fariszuh/IoT-Concrete-Heat-Hidration/Prototype/Gambar Panas Hidrasi.pptx

Permukaan yang dingin dan Thermal Cracking

Temperatur di tengah selama hidrasi

## Slide 2

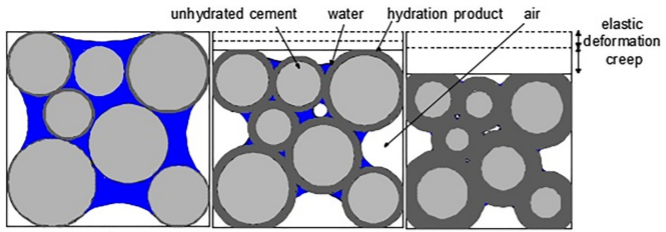
[picture p20: figure]
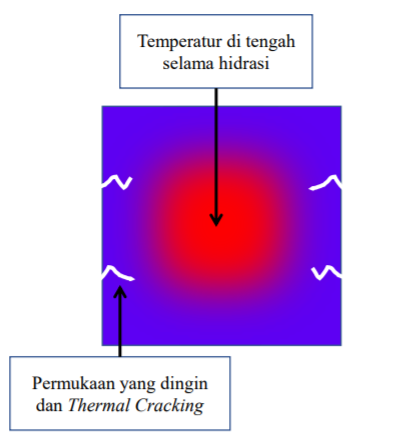
[picture p21: figure]

## Slide 3

Algoritma Pengolahan Data

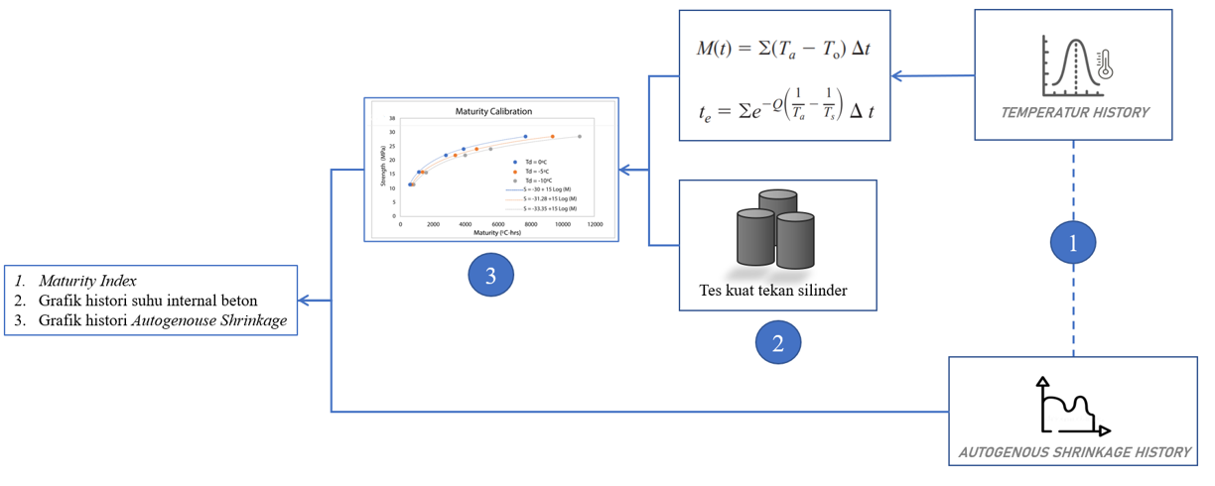
[picture p22: figure]

Cloud data base

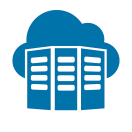
[picture p23: figure]

Penyimpanan Offline

Mikrokontroller ESP32

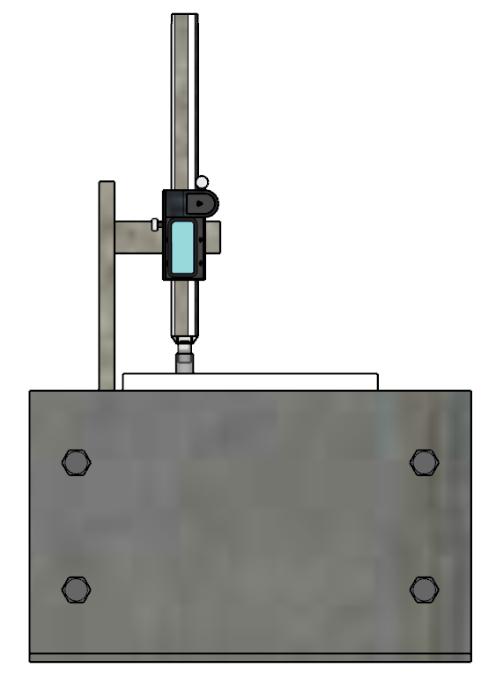
[picture p24: figure]

A

A

Tampak Depan

Unscaled

Digital Caliper

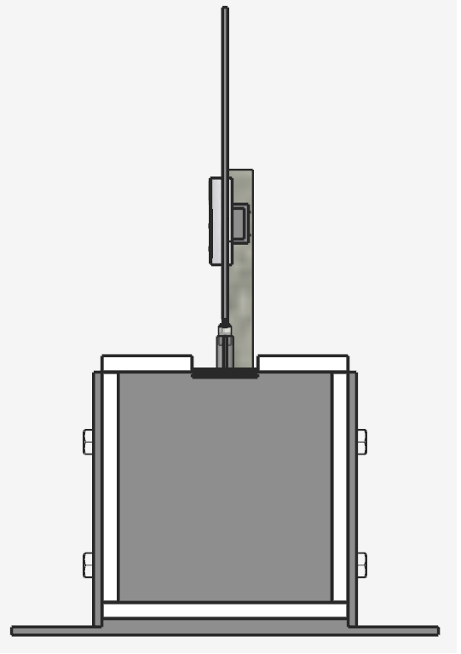
[picture p25: figure]

Potongan A-A

Unscaled

Cor Beton

Cetakan Beton

Sendor DS18B20

Insulasi

## Slide 4

Algoritma Pengolahan Data

## Slide 5

Algoritma Perhitungan

Potongan A-A

Unscaled

Cloud data base

Mikrokontroller ESP32

Penyimpanan Offline

A

A

Tampak Depan

Unscaled

Digital Caliper

Cor Beton

Cetakan Beton

Termokopel

Insulasi gabus

## Slide 6

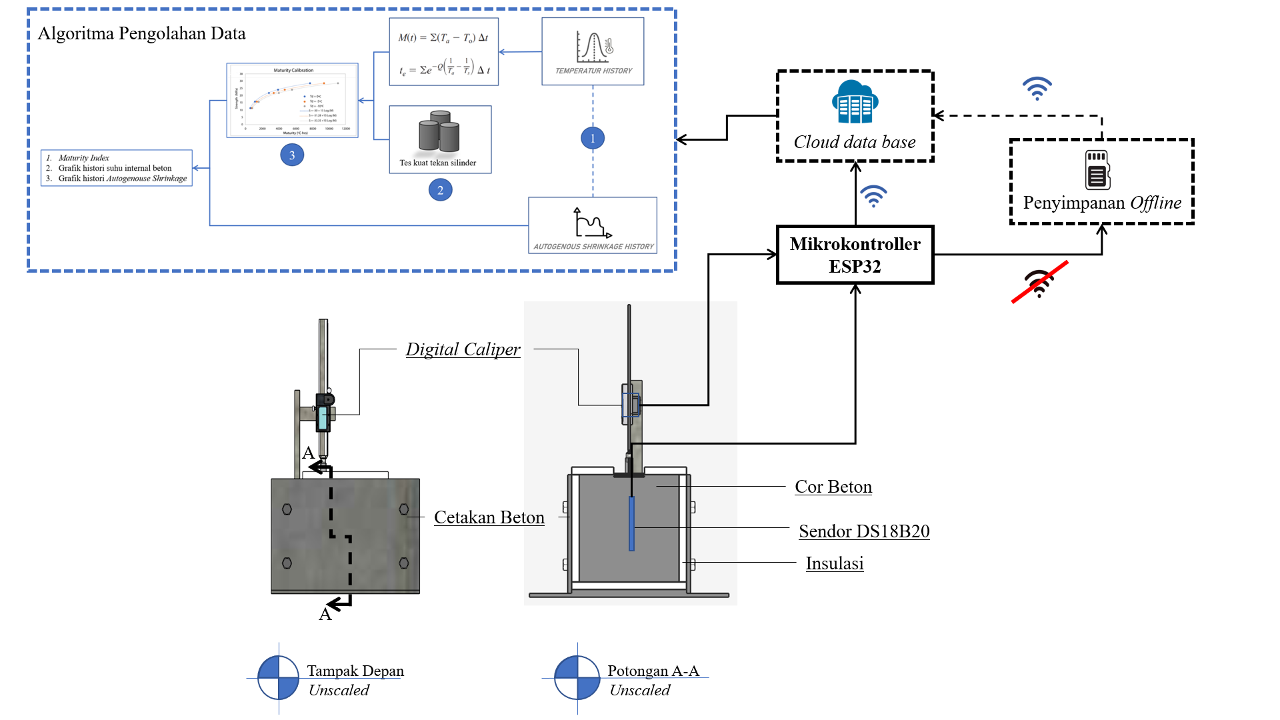
[picture p26: figure]

## Slide 7

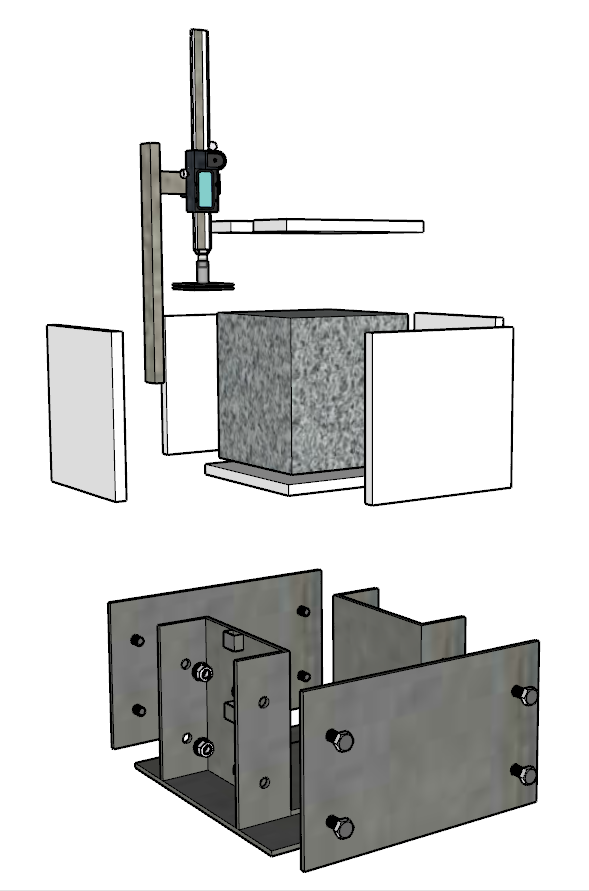
[picture p27: figure]
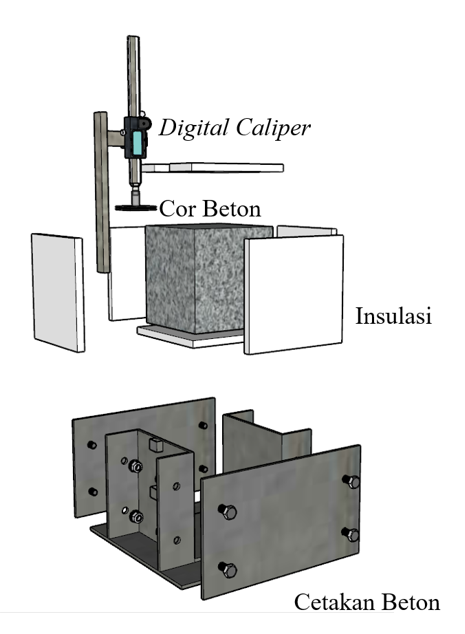
[picture p28: figure]

Digital Caliper

Cor Beton

Insulasi

Cetakan Beton

## Slide 8

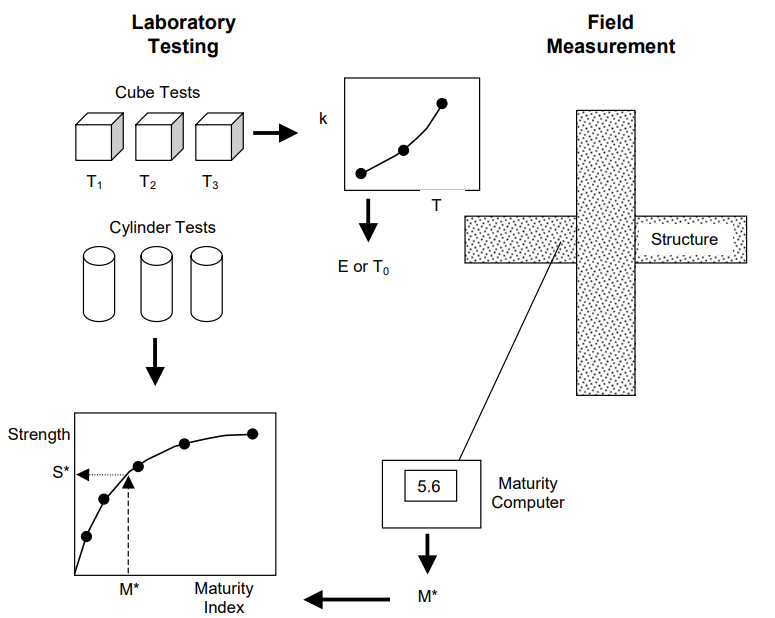
[picture p29: figure]

Pengukuran suhu Dengan alat yang sudah dibuat

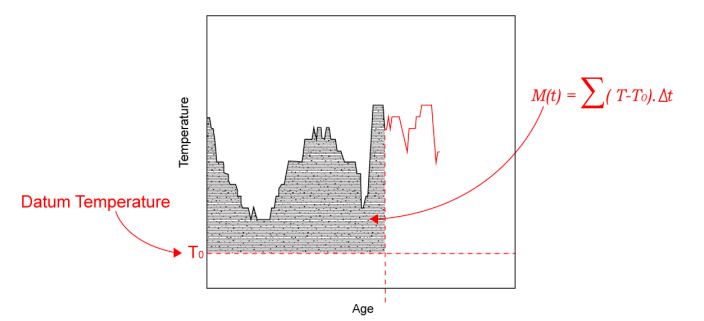
[picture p30: figure]
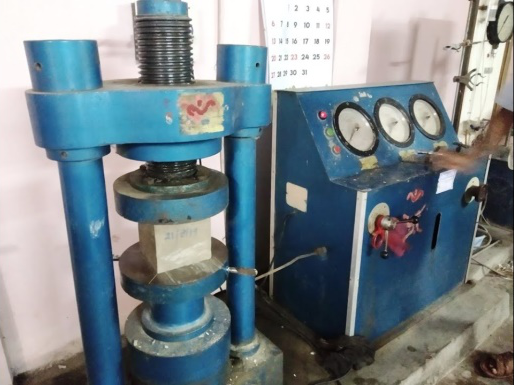
[picture p31: figure]
See the source image
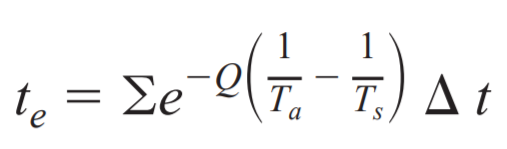
[picture p32: figure]
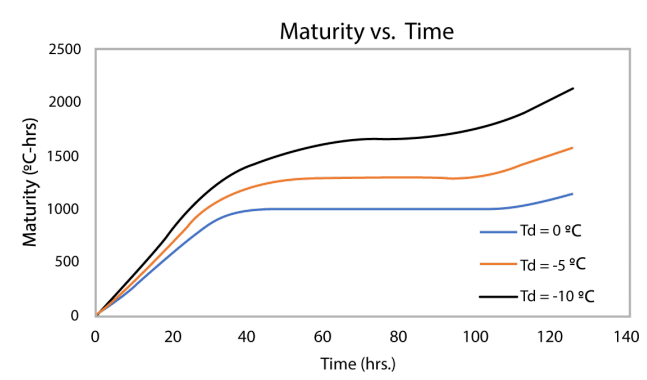
[picture p33: figure]
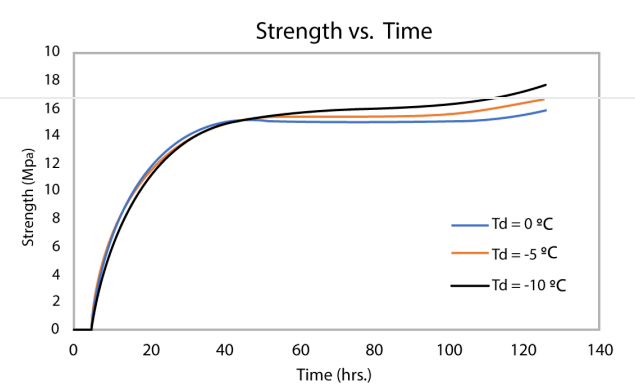
[picture p34: figure]
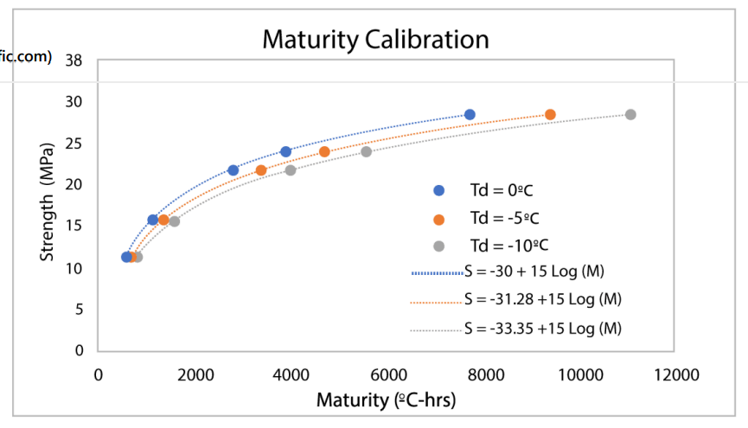
[picture p35: figure]

## Slide 9

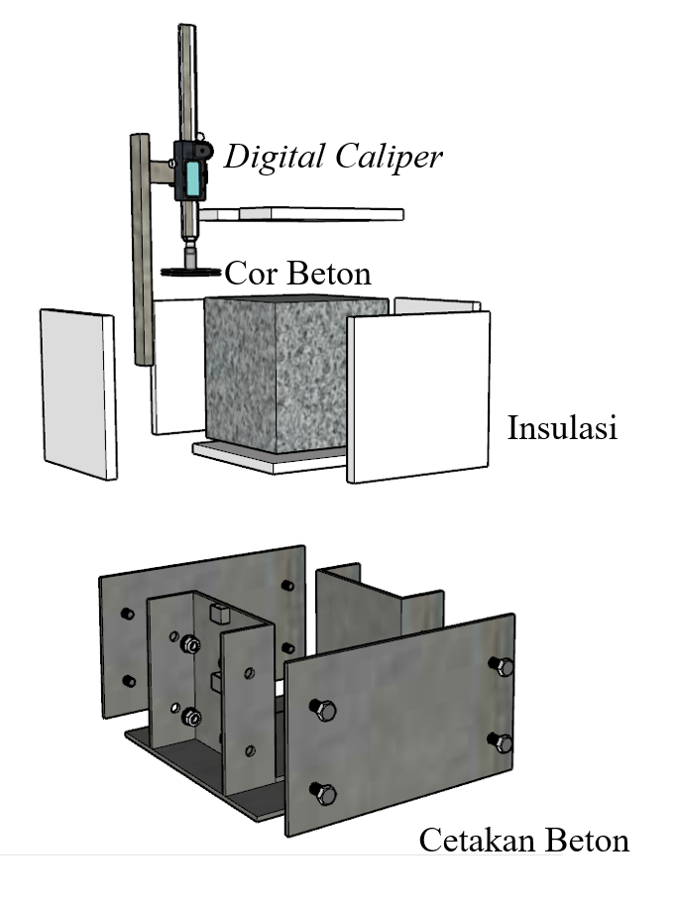
[picture p36: figure]
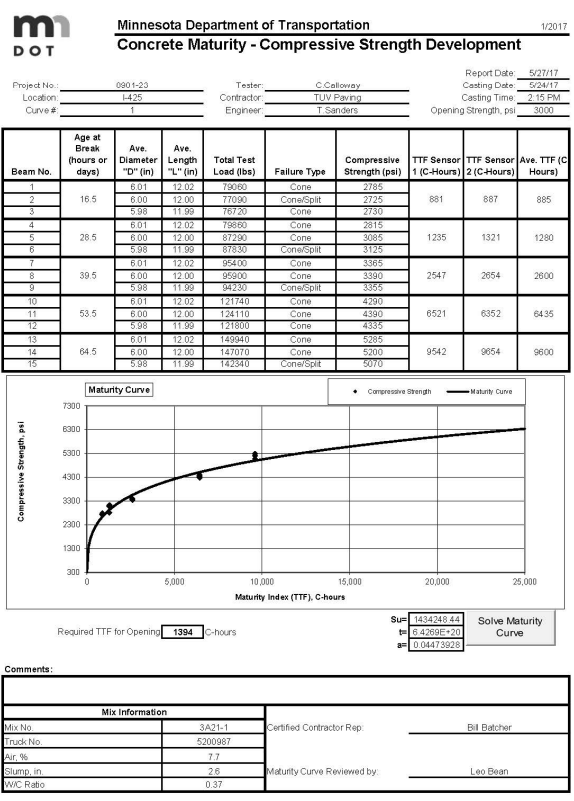
[picture p37: figure]
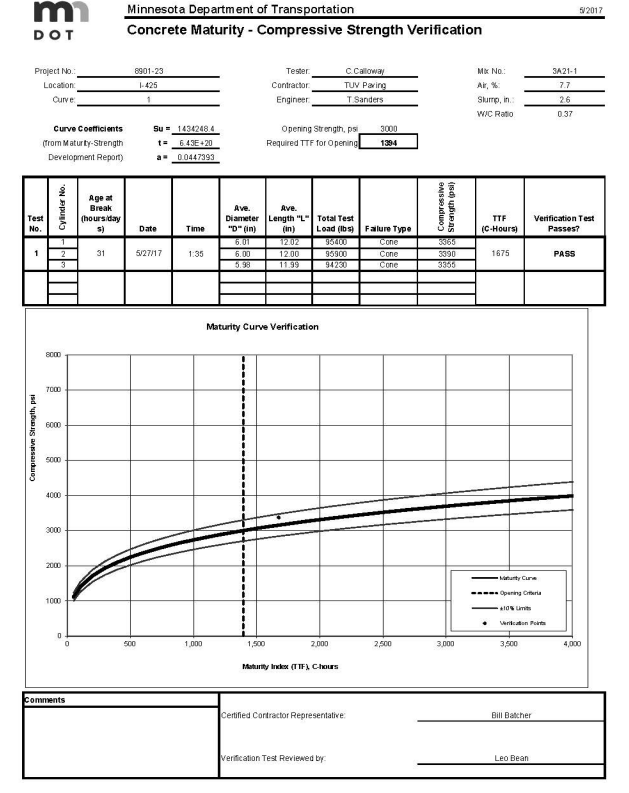
[picture p38: figure]

## Slide 10

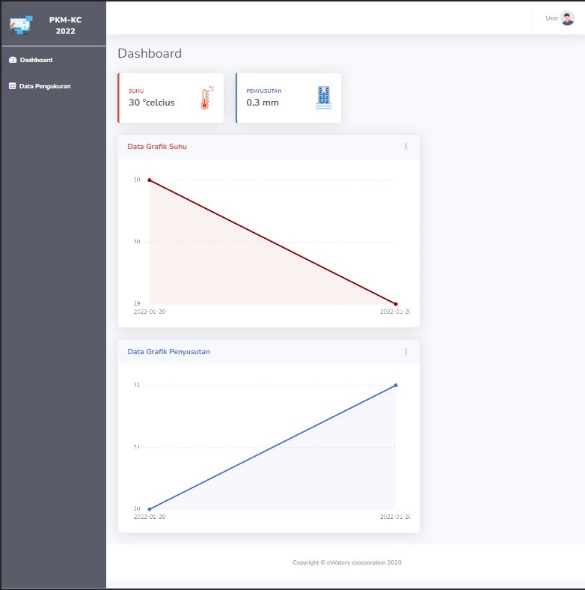
[picture p39: figure]
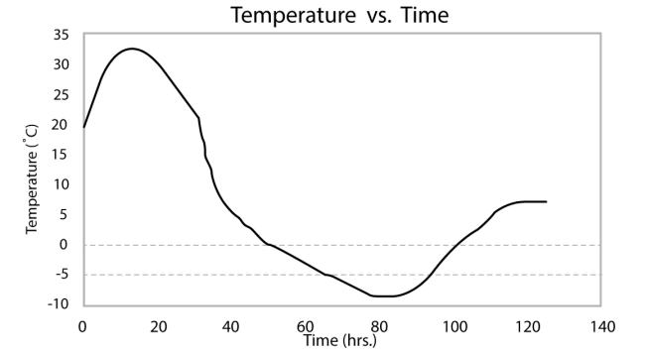
[picture p40: figure]
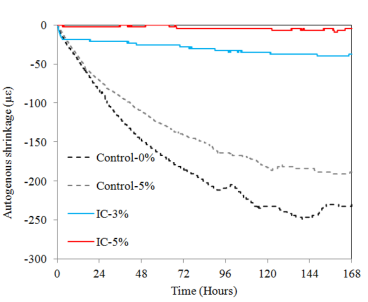
[picture p41: figure]

## Slide 11

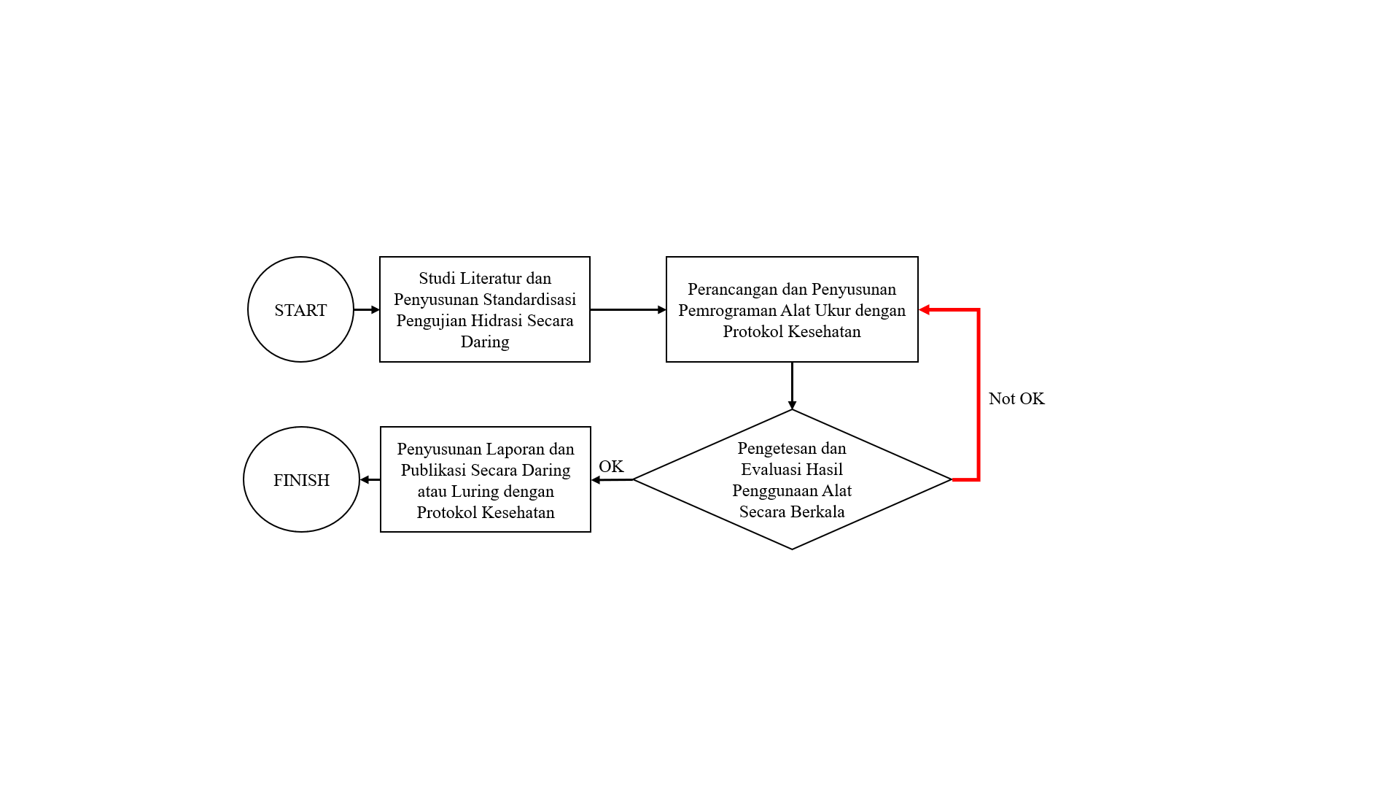
[picture p42: figure]
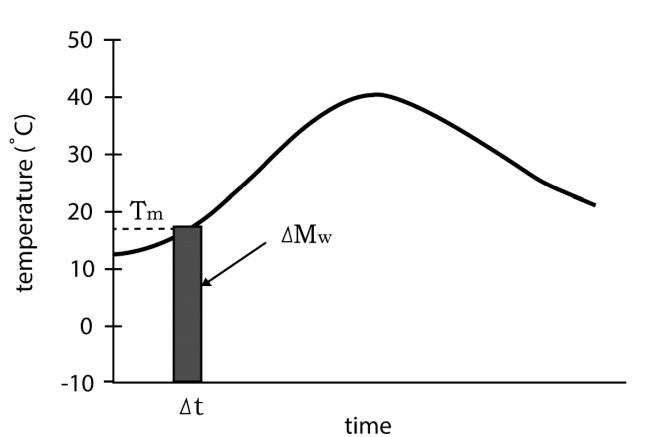
[picture p43: figure]

START

Studi Literatur dan Penyusunan Standardisasi Pengujian Hidrasi Secara Daring

Perancangan dan Penyusunan Pemrograman Alat Ukur dengan Protokol Kesehatan

Pengetesan dan Evaluasi Hasil Penggunaan Alat Secara Berkala

Not OK

FINISH

Penyusunan Laporan dan Publikasi Secara Daring atau Luring dengan Protokol Kesehatan

OK

## Slide 12

Tes Kuat Tekan Beton

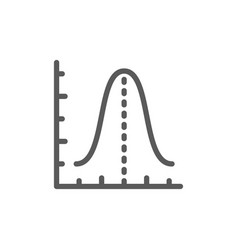
[picture p44: figure]
Curve Graph Vector Images (over 15,000)

TEMPERATUR HISTORY

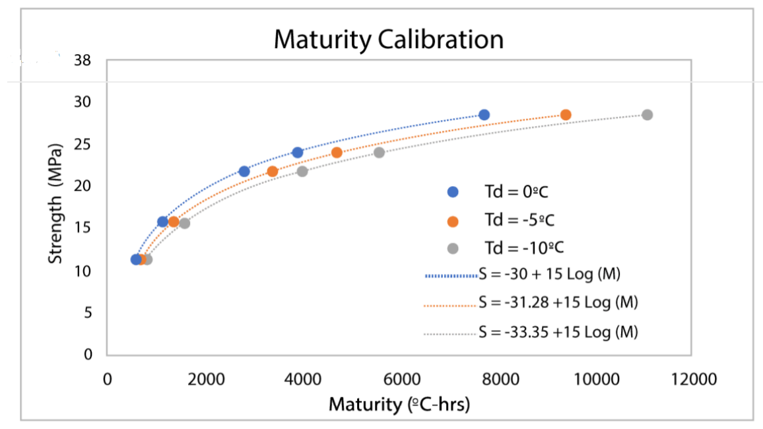
[picture p45: figure]

1. Maturity Index
2. Grafik histori suhu internal beton
3. Grafik histori Autogenouse Shrinkage

AUTOGENOUS SHRINKAGE HISTORY

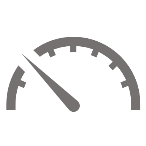
[picture p46: figure]
Speedometer Low with solid fill

## Slide 13

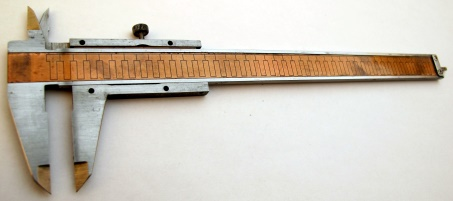
[picture p47: figure]
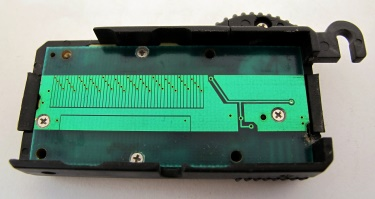
[picture p48: figure]
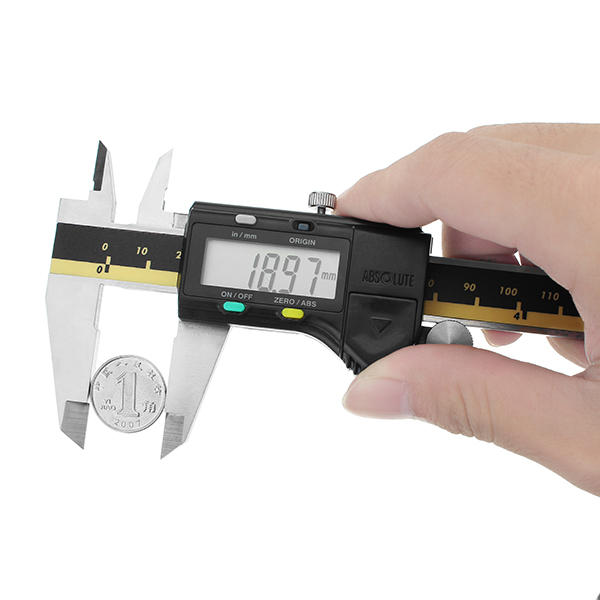
[picture p49: figure]
Hand Tools Business, Office & Industrial 6 Inch 150mm LCD Digital Electronic Vernier Caliper Micrometer Stainless Steel R suneducationgroup.com
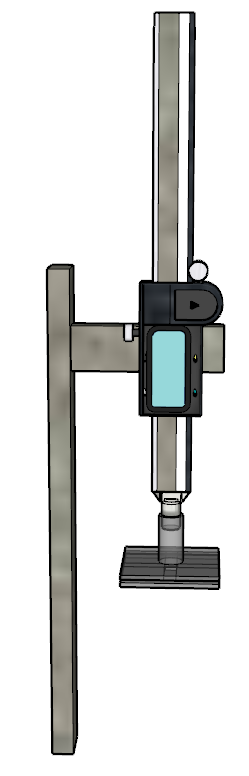
[picture p50: figure]

disambungkan

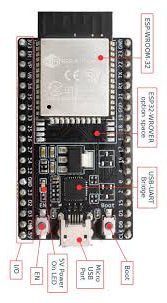
[picture p51: figure]
The Internet of Things with ESP32

1

2

3

disambungkan

Pengukuran Suhu Dengan Sensor
