fariszuh/IoT-Concrete-Heat-Hidration/Daftar Pustaka/Lapkhir.pdf

i

DAFTAR ISI

DAFTAR ISI | i
DAFTAR GAMBAR | i
DAFTAR TABEL | i
BAB 1. PENDAHULUAN | 1
1.1 | Latar Belakang | 1
1.2 | Perumusan Masalah | 2
1.3 | Tujuan | 3
BAB 2. TINJAUAN PUSTAKA | 3
2.1 Internet of Things (IoT) | 3
2.2 Modul Relay | 3
2.3 Sensor Arus ACS712 | 3
2.4 Sensor Tegangan ZMPT101B | 4
BAB 3. METODE PELAKSANAAN | 4
3.1 Studi Literatur | 4
3.2 Penyusunan Script | 4
3.3 Pembuatan Animasi | 4
3.4 Penyusunan Video | 4
3.5 Pembuatan Laporan | 4
BAB 4. HASIL YANG DICAPAI | 5
4.1 Hasil yang dicapai | 5
4.2 Potensi Khusus | 8
BAB 5 PENUTUP | 9
5.1 Kesimpulan | 9
5.2 Saran | 9
DAFTAR PUSTAKA | 10
LAMPIRAN | 11
Lampiran 1. Tabel Rincian Penggunaan Dana | 11
Lampiran 2. Nota Pembayaran | 12
Lampiran 3. Bukti Pendukung Kegiatan | 19
Lampiran 4. Lain Lain | 21
| DAFTAR GAMBAR
Gambar 1. Halaman Depan User Interface pada Aplikasi Pengguna | 9
Gambar 2. Desain Rangkaian Komponen Elcomic | 9
Gambar 3. Gambaran Peralatan Listrik Rumah Tangga | 10
Gambar 4. Gambaran Dalam Stop Kontak | 10
Gambar 5. Gambaran Depan Video Pelaksanaan Program | 11
| DAFTAR TABEL
Tabel 1.1 Tarif Dasar Listrik PLN dengan Daya 1300 VA Tahun 2015-2017.....4 Tabel 1.2 Perbandingan Elcomic dengan KWh Meter Digital dan Power Meter.5

BAB 1. PENDAHULUAN

### 1.1 Latar Belakang

Kenaikan pendapatan yang tidak sebanding dengan kebutuhan merupakan salah satu masalah ekonomi yang dirasakan oleh sebagian masyarakat Indonesia. Selain itu kenaikan biaya bahan bakar, pendidikan dan sembako juga menambah beban pengeluaran masyarakat. Adanya kebijakan menaikkan tarif dasar listrik menyebabkan pengeluaran masyarakat terus bertambah.
Salah satu belanja pokok masyarakat tiap bulan adalah biaya listrik yang dapat dihitung dengan cara besaran daya yang dipakai dikalikan tarif listrik lalu dikalikan waktu pemakaian. Pemakaian listrik semakin sulit untuk dikontrol dan dibatasi agar sesuai dengan anggaran keuangan rumah tangga yang tersedia seiring perkembangan teknologi. Akibat dari pemakaian yang tidak dibatasi, seringkali biaya listrik membengkak sehingga masyarakat harus sadar akan pemakaian listrik agar tidak berlebih. Dengan anggaran listrik rumah tangga yang terkontrol, sisa anggaran dapat dialokasikan untuk jenis pengeluaran yang lain dan juga tidak mengganggu anggaran belanja rumah tangga yang telah direncanakan.

Tabel 1.1 Tarif Dasar Listrik PLN dengan Daya 1300 VA Tahun 2015-2017
Tarif Dasar Listrik | Tahun
2014 | 2015 | 2016 | 2107
1300 VA | Rp 1.214/kWh | Rp 1.352/kWh | Rp 1.364,86/kWh | Rp 1.467,28/kWh

Saat ini kebanyakan rumah tangga di Indonesia menggunakan kWh meter digital yang dipakai untuk listrik prabayar. Alat tersebut hanya menampilkan daya listrik tersisa yang akan digunakan. Selain itu ada alat yang bernama Power Meter, yaitu alat yang mampu memonitor dan mengetahui besar daya listrik yang digunakan di dalam rumah. Kedua alat tersebut dapat memantau pemakaian daya listrik, namun tidak mampu melakukan pengawasan terhadap penggunaannya dari sisi biaya. Dari alat berbasis aplikasi ada juga yang dapat mengontrol penggunaan listrik perangkat elektronik yang terhubung dengan jaringan nirkabel namun tidak berbasis biaya listrik. Sehingga, solusi tersebut belum mampu mengatasi permasalahan anggaran pengeluaran kebutuhan listrik rumah tangga masyarakat Indonesia.
Oleh karena itu, dibutuhkan solusi berupa alat yang dapat memanage penggunaan listrik berdasarkan anggaran belanja rumah tangga yang dapat memonitor dan membantu konsumen untuk membatasi penggunaan listrik dengan menggunakan sistem wireless melalui smartphone dan aplikasi berbasis IoT (Internet of Things). Alat yang terdiri dari software dan hardware terintegrasi ini dilengkapi dengan algoritma yang menghitung penggunaan daya listrik berbasis tarif Rupiah untuk kemudian disampaikan kepada pengguna dalam bentuk alarm atau notifikasi penggunaan sebagai pengingat apabila penggunaan listrik hampir mendekati batas. Pada alat ini juga terdapat relay system yang terhubung dengan perangkat elektronik agar dapat mematikan peralatan listrik yang tidak terlalu dibutuhkan apabila pengunaan listrik di suatu rumah melebihi tarif yang ditentukan oleh budget planner secara otomatis dan real time. Alat ini dapat melakukan setting untuk berapa besar daya yang mau dikeluarkan bergantung biaya penggunaan listrik yang ingin dimasukkan dalam aplikasi. Selain itu, pada alat ini dilengkapi memory yang dapat menyimpan data penggunaan listrik bulan sebelumnya yang bisa digunakan untuk evaluasi pemakaian listrik. Dengan alat ini, tentunya mampu menjawab permasalahan masyarakat rumah tangga dalam menghemat listrik sehingga anggaran rumah tangga dapat dialokasikan ke kebutuhan yang lain.

Tabel 1.2 Perbandingan Elcomic dengan KWh Meter Digital dan Power Meter
| KWh Meter Digital (Schneider - IEM 3255) | Power Meter ( Siemens -SICAM P50/55) | ELCOMIC
Mengukur Daya Listrik | ✓ | ✓ | ✓
Mengukur Daya Listrik per Peralatan | - | ✓ | ✓
Mengukur Biaya Listrik yang Telah Digunakan | - | - | ✓
Pengingat Penggunaan Biaya Listrik | - | - | ✓
Rencana Anggaran Penggunaan Biaya Listrik | - | - | ✓
Pemutus Arus Listrik | ✓ | - | ✓

### 1.2 Perumusan Masalah

Permasalahan yang akan diselesaikan dari Program Kreativitas Mahasasiswa ini adalah bagaimana cara merancang desain, komponen penyusun alat, serta simulasi kerja alat ELCOMIC yang divisualisasikan dalam sebuah video animasi.

### 1.3 Tujuan

Tujuan yang akan dicapai dengan Program Kreativitas Mahasiswa ini berupa rancangan desain, komponen penyusun alat, serta simulasi kerja alat ELCOMIC yang divisualisasikan dalam sebuah video animasi.

### 1.4 Manfaat

Manfaat dari Program Kreativitas Mandiri ini sebagai berikut:
1. Bagi Rumah Tangga
Membantu merencanakan dan mengontrol penggunaan listrik sesuai dengan anggaran belanja sehingga dapat menghemat pengeluaran.
2. Bagi Mahasiswa
Mengembangkan kreativitas dalam bidang teknologi yang lebih efektif dan efisien sesuai dengan permasalahan yang ada dalam masyarakat.

BAB 2. TINJAUAN PUSTAKA

### 2.1 Internet of Things (IoT)

Terdapat lebih dari delapan juta perangkat berbasis Internet of Things (IoT) pada tahun 2019 (K.L.Lueth,2018).Internet of Things merupakan perpaduan perangkat keras yang diintegrasikan ke dalam jaringan informasi sebagai penghubung atau sarana komunikasi antar pengguna. Perangkat berbasis IoT dapat menghimpun dan membagikan data dari berbagai pengguna (J.Mills dkk.,2020). Dalam hal ini, data yang diperoleh dari sensor tegangan dan sensor arus akan dikirimkan kepada pengguna melalui sarana Internet of Things. Beberapa perangkat IoT seperti kamera keamanan, pelacak aktivitas kebugaran dan kesehatan, dan smartphones menghimpun data yang bersifat privasi sehingga pengguna tidak ingin membagikan data tersebut dengan pengguna lain. Sama halnya dengan alat yang ini dimana data dari sensor tegangan dan sensor arus hanya dibagikan kepada satu pengguna yang bersesuaian dengan sensor tersebut.

### 2.2 Modul Relay

Relay adalah alat yang digunakan sebagai pembuka/penutup suatu circuit elektrikal dengan suatu kondisi yang memicu. Relay merupakan elektromagnet yang sirkuit magnetnya terdiri atas coil, armature, switch contact point, dan spring yang bekerja berdasarkan medan elektromagnetik (Apples dkk.,1966). Relay menggunakan prinsip elektromagnetik untuk menggerakkan kontak saklar sehingga dengan arus listrik yang kecil dapat menghantarkan listrik yang bertegangan tinggi.. Dalam hal ini Modul Relay menjaga keamanan suatu rangkaian system elektrik dimana akan mendeteksi suatu keadaan abnormal dalam system lalu akan dilakukan tindakan sirkuit kontrol yang tepat (Kezunovic dkk., 2016).

### 2.3 Sensor Arus ACS712

Sensor Arus ACS712 merupakan sensor yang digunakan untuk mendeteksi arus listrik dengan keahlian memantau penggunaan arus listrik dan dapat memberikan nilai analog sehingga penggunaan tenaga listrik dapat dikontrol (Dalimunthe, 2018). Sensor ACS712 dapat mendeteksi arus baik AC maupun DC dimana sensor ini bekerja dengan prinsip efek Hall. Sensor ACS712 juga memiliki tingkat akurasi yang tinggi, linearitas yang baik, disuplai oleh 5V DC; tegangan output adalah 4.5V, dan perlu sedikit rangkaian untuk pengolahan data (Li dkk.,2010). Pada alat ini ACS712 berfungsi sebagai pendeteksi aliran arus listrik yang mengalir.

### 2.4 Sensor Tegangan ZMPT101B

Modul sensor tegangan ZMPT101B adalah sensor tegangan yang dibuat dari transformator tegangan ZMPT101B. Sensor ini memiliki akurasi tinggi, konsistensi yang baik untuk pengukuran tegangan dan dapat mengukur hingga 250V AC serta dilengkapi dengan potensiometer untuk menyesuaikan output ADC ke nilai yang sesuai dengan input referensi(Abubakar dkk., 2017). Pada alat ini ZMPT101B berfungsi sebagai pengukur tegangan pada peralatan listrik.

BAB 3. METODE PELAKSANAAN

### 3.1 Studi Literatur

Pada studi literatur dilakukan proses pencarian materi yang berkaitan dengan Internet of Things, Sensor Tegangan ZMPT101B, Sensor Arus ACS712, Modul Relay, STM32, Micro SD card, dan User Interface. Selain itu, juga dilakukan studi literatur mengenai permasalahan listrik rumah tangga. Literatur yang digunakan antara lain dari berita harian, artikel, jurnal, seminar internasional, dan publikasi ilmiah.

### 3.2 Penyusunan Script

Script dibuat agar video terarah serta terkonsep dengan baik. Script yang dibuat antara lain penjelasan latar belakang, animasi dialog, animasi desain interior, dan penjelasan mengenai User Interface aplikasi. Script ini sendiri dibuat di software Notepad.

### 3.3 Pembuatan Animasi

Animasi yang dibuat agar menjadikan video program lebih menarik serta dapat lebih dipahami dengan mudah. Animasi yang dibuat yaitu animasi dialog Elco dan Mico. mengenai alat ini serta animasi interior rumah dengan peralatan yang diintegrasikan dengan alat dan aplikasi Elcomic. Animasi Elco dan Mico dibuat menggunakan software Adobe After Effect, sedangkan animasi interior rumah dibuat menggunakan software SketchUp.

### 3.4 Penyusunan Video

Pada proses penyusunan video, seluruh scene dan animasi disusun dan diedit dengan menambahkan musik dan tulisan penjelasan didalamnya. Video diedit dan disusun menggunakan software Adobe Premiere Pro.

### 3.5 Pembuatan Laporan

Proses penulisan laporan dilakukan setelah semua tahap terselesaikan sehingga hasil yang diperoleh dapat dijelaskan secara rinci sesuai dengan data yang diperoleh. Kemudian semua kegiatan yang telah dilakukan akan didokumentasikan dalam foto dan pembuatan video simulasi sebagai luaran yang akan menggantikan prototipe karena faktor masa pandemi yang tidak memungkinkan kegiatan di luar rumah.

BAB 4. HASIL YANG DICAPAI

### 4.1 Hasil yang dicapai

Adapun hasil yang dicapai pada program kreatifitas mahasiswa ini adalah sebagai berikut :
1. Studi Literatur
Hasil : Mendapatkan berbagai sumber pendukung dari jurnal – jurnal yang terindeks scopus (jurnal ieee, springer, science direct), yaitu tentang STM32, sensor arus ACS712, sensor tegangan ZMPT101B dan relay.
2. Pembuatan User Interface
Hasil : Mendapatkan desain User Interface aplikasi Elcomic yang nantinya diterapkan di smartphone calon pengguna. Desain aplikasi dibuat menggunakan Adobe Ilustrator.Aplikasi ini terdiri dari beberapa fitur, diantaranya :
- Halaman depan (sign in & sign up) ;
- Halaman utama (home)-->memantau besar pemakaian ;
- History-->sejarah pemakaian ;
- Setting-->pengaturan & penambahan peralatan ;
- Beranda (terdapat fitur account user, about us, notification, infromation, dan help) :
*[account user]-->user mana yang terkoneksi dengan alat ; *[notification]-->pemberitahuan mengenai opsi pemutusan peralatan ;

*[information]-->informasi mengenai peraturan pemakaian & tarif.

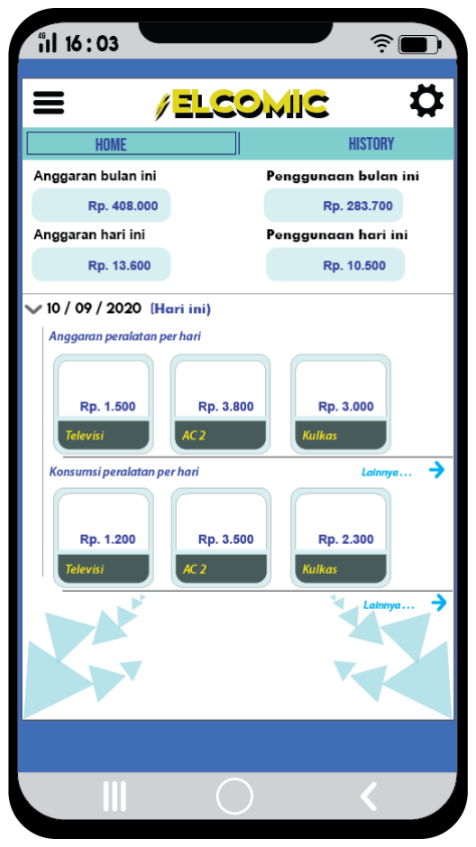
[picture p228: figure]

Gambar 1. Halaman Depan User Interface pada Aplikasi Pengguna
3. Assembly komponen
Hasil : Mendapatkan desain rangkaian komponen yang dibuat dalam bentuk 2D.

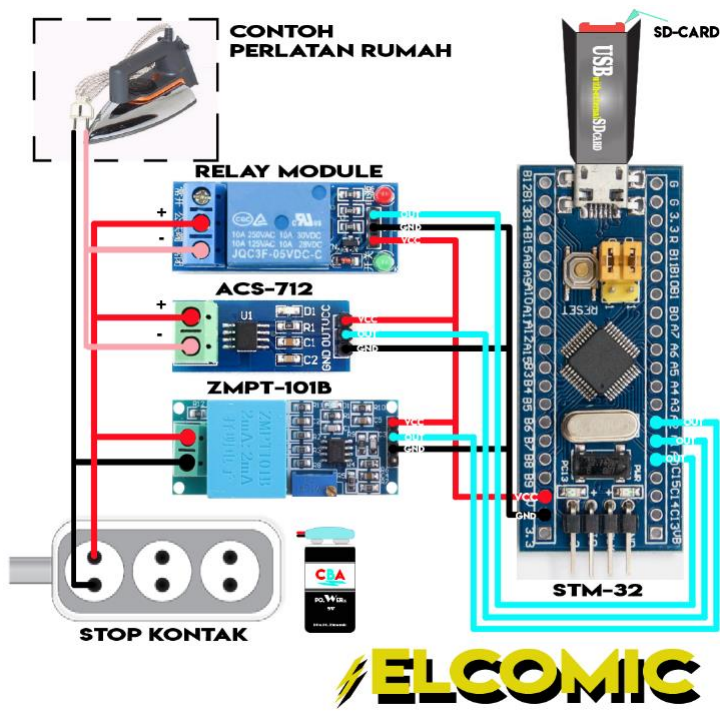
[picture p229: figure]

Gambar 2. Desain Rangkaian Komponen Elcomic

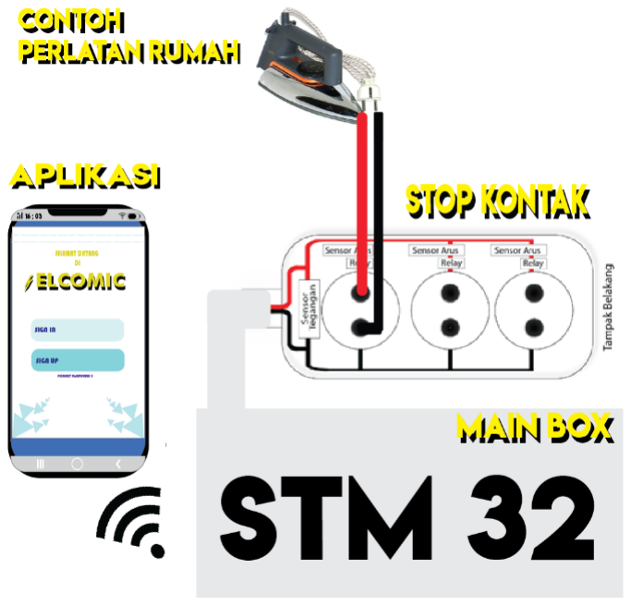
[picture p230: figure]

Gambar 3. Gambaran Peralatan Listrik Rumah Tangga

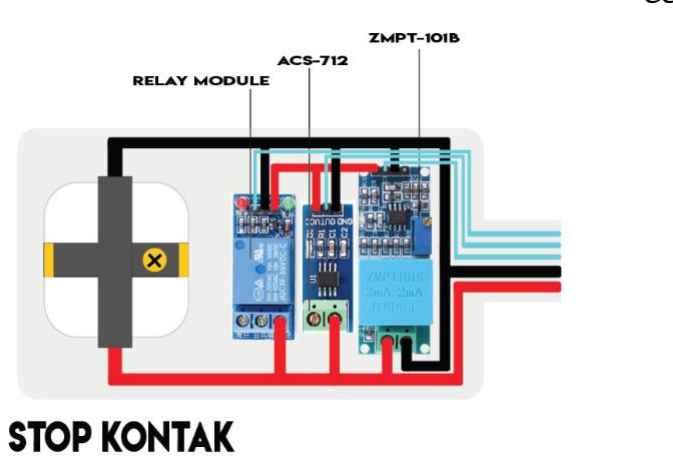
[picture p231: figure]

Gambar 4. Gambaran Dalam Stop Kontak
4. Analisis manfaat dan kontribusi alat terhadap masyarakat
Hasil : Mendapatkan analisis manfaat produk terhadap teknologi terkini, ekonomi dan sosial untuk saat ini dan masa depan serta kontribusi terhadap kebutuhan masyarakat.
5. Video Pelaksanaan Program
Hasil: Mendapatkan video penjelasan latar belakang, penjelasan rumusan masalah, pembuatan desain User Interface, dan pembuatan desain rangkaian komponen dari PKM ini.

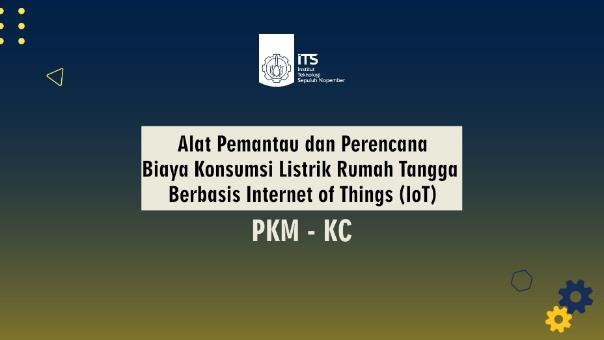
[picture p232: figure]

Gambar 5. Gambaran Depan Video Pelaksanaan Program

### 4.2 Potensi Khusus

Potensi khusus dari program kreatifitas mahasiswa ini adalah sebagai berikut :

### 1. Potensi Paten

Inovasi yang ada pada Elcomic terdapat pada fitur dimana user dapat memantau besar penggunaan masing peralatan elektronik secara real time serta fitur dimana user dapat melakukan tindakan pemutusan arus pada suatu peralatan elektronik apabila pengunaan listrik melebihi tarif yang ditentukan oleh budget planner secara otomatis dan real time yang bersifat opsional (terdapat notifikasi konfirmasi peralatan tertentu sudah dekat dengan batas pakai berupa “ya” atau “tidak”,untuk melakukan pemutusan). Terdapat juga perbadingan produk dengan produk paten No. 2016-13940 (Japan Patent) dimana keunggulan produk Elcomic, yaitu dapat melakukan monitoring biaya per peralatan, merencanakan biaya per peralatan, serta display monitoring menggunakan smartphone yang membuat lebih fleksibel. Hal berikut menjadikan produk kami berbeda dengan Kwh meter yang hanya menampilkan daya listrik tersisa yang akan digunakan dan Power Meter yang hanya memonitor dan mengetahui besar daya listrik yang digunakan di dalam rumah. Pernyataan ini mendukung produk Elcomic sangat potensial untuk dipatenkan.

### 2. Manfaat Bagi Teknologi Terkini, Ekonomi, dan Sosial untuk Saat

Ini dan Masa Depan
Dalam bidang teknologi di Indonesia belum ada alat atau prototipe yang dapat memantau laju penggunaan listrik rumah tangga setiap waktunya. Masyarakat hanya mengetahui biaya pemakaian listrik perbulannya untuk pascabayar dan mengetahui pulsa listrik akan habis terpakai untuk prabayar. Melalui produk ini, masyarakat dapat memantau serta mengontrol laju penggunaan listrik rumah tangga melalui aplikasi di smartphone. Hal tersebut menunjukkan manfaat dari produk untuk teknologi terkini. Subsidi listrik di APBN 2020 dianggarkan sebesar Rp. 54,79 triliun, diperkirakan akan membengkak menjadi Rp. 62,93 triliun akibat pengalokasian tambahan dalam bentuk keringanan tagihan listrik bagi masyarakat terdampak covid-19(Yolandha, 2020). Melalui produk ini, masyarakat setidaknya membantu mengurangi anggaran subsidi listrik dengan cara mengontrol penggunaan listrik rumah tangga. Pengurangan anggaran subsidi listrik dapat dialokasikan untuk pembangunan ekonomi lainnya seperti pembangunan infrastruktur, jalan tol, dan lain sebagainya. Hal tersebut menunjukkan manfaat produk dalam bidang ekonomi saat ini dan yang akan datang.
Pada awal semester tahun 2019, 61% dari 58.519 MW yang diproduksi oleh pembangkit listrik di Indonesia berasal dari batu bara (Banjarnahor, 2019). Penggunaan batu bara secara masif untuk bahan bakar pembangkit listrik dapat berdampak buruk bagi lingkungan yakni pemanasan global. Melalui cara mengontrol penggunaan listrik rumah tangga dari produk ini, masyarakat dapat mengurangi pemanasan global yang disebabkan dari bahan bakar fosil tersebut. Selain itu, mengontrol penggunaan listrik dapat dijadikan upaya untuk menghemat energi secara konkret. Hal tersebut menunjukkan manfaat dari produk dalam bidang sosial saat ini dan yang akan datang.

### 3. Kontribusi Produk Terhadap Kebutuhan Masyarakat

Adapun kontribusi produk terhadap kebutuhan masyarakat, yaitu membantu memanage perekonomian rumah tangga khususnya dalam pemakaian listrik karena adanya produk, pemakaian listrik rumah tangga dapat diatur sesuai kondisi kebutuhan dan keuangan dimana pengguna dapat memantau besar pengeluaran listrik tiap peralatan yang digunakan. Produk diharapkan menjadikan pemakaian peralatan listrik yang lebih displin dan efisiensi dengan terdapatnya relay pada produk guna membatasi pemakaian peralatan listrik dengan melakukan pemutusan terhadap sebuah peralatan yang bersifat opsional.

BAB 5 PENUTUP

### 5.1 Kesimpulan

Kesimpulan yang dapat diambil dari produk ELCOMIC, yaitu merupakan alat pemantau dan perencana biaya konsumsi listrik rumah tangga berbasis Internet of Things (IoT) yang tidak hanya dapat melakukan pengukuran daya listrik, listrik perperalatan, dan pemutusan arus listrik seperti pada KWh meter dan Power meter, tetapi juga dapat melakukan pengukuran biaya listrik yang telah digunakan, mengingatkan penggunaan biaya listrik yang akan dinotifikasikan melalui apklikasi produk, perencanaan anggaran penggunaan biaya listrik, serta dapat melakukan tindak pemutusan opsional tehadap suatu stop kontak peralatan jika pemakaian peralatan telah melewati batas penggunaan. Melalui ini, pengguna dapat terbantu dalam permasalahan perekonomian mereka khususnya dalam hal penggunaan listrik dimana menjadikan pengguna dapat memanage berapa besar biaya penggunaan listrik yang ingin mereka gunakan / keluarkan sehingga dapat menghemat pengeluaran.

### 5.2 Saran

Saran yang didapat adalah sebagai berikut :
1. Untuk desain main box yang berisi Mikrokontroler STM32, Micro SD Card, Regulator, dan modul WI-FI dapat dimaksimalkan dalam unsur seninya.
2. Aplikasi Elcomic dapat ditambahkan fitur spesifikasi peralatan yang didapatkan dari library atau internet setelah user memasukkan merk dan serinya.

DAFTAR PUSTAKA
Abubakar, dkk. 2017. Calibration of ZMPT101B Voltage Sensor ModSule using Polynomial Regression for Accurate Load Monitoring. APRN Journal of Engineering and Applied Sciences. Volume 12, No. 4.
Appels J. Th dan Geels B. H. 1966. Handbook of Relay Switching Technique. Springer-Verlag Berlin Heidelberg.
Banjarnahor, Donald. 2019. Dari 58 Ribu MW, 61% Pembangkit Listrik RI Masih Batu Bara. www.cnbcindonesia.com/news/20190923114710-4-101382/dari-58-ribu-mw-61-pembangkit-listrik-ri-masih-batu-bara (diakses tanggal 20 Agustus 2020)
Dalimunthe, R. A. 2018 .Pemantau Arus Listrik Berbasis Alarm Dengan Sensor Arus. Seminar Nasional Royal., pp. 333–338
Kezunovic, Mladen, dkk. 2016. Design, Modeling dan Evaluation of Protective Relays for Power Systems. Springer International Publishing Switzerland Li, L. dkk,. 2010. The Application of Hall Sensors ACS712 in The Protection Circuit of Controller for Humanoid Robots. International Conference on Computer Sciences and Appliead Mathematics. vol. 12.
Lueth, K.L. 2018. State of the IoT 2018: Number of IoT Devices Now at 7B—Market Accelerating. Available: iot-analytics.com/state-of-the-iot-update-q1-q2-2018-number-of-iot-devices-now-7b
Mills, J. dkk. 2020. Communication-Efficient Federated Learning for Wireless Edge Intelligence in IoT. IEEE Internet of Things Journal. Vol. 7, No. 7, pp. 5986-5994.
Yolandha, Friska. 2020. Subsidi Listrik Diproyeksi Jebol Sampai Rp 62,93 Triliun. www.republika.co.id/berita/qeewjv370/subsidi-listrik-diproyeksi-jebol-sampai-rp-6293-triliun (diakses tanggal 20 Agustus 2020)

LAMPIRAN

Lampiran 1. Tabel Rincian Penggunaan Dana

### 1. Pemasukan

No. | Keterangan | Total (Rp)
1. | Pendanaan PKM 2020 | Rp 5.000.000
TOTAL PEMASUKAN (Rp) | | Rp 5.000.000

### 2. Pengeluaran

No | Keterangan | Total (Rp)
1. | Kuota Internet | Rp 593.050
2. | Produk | Rp3.574.100
3. | Media penyimpanan soft file | Rp 825.000
TOTAL PENGELUARAN (Rp) | | Rp.4.992.150

### 3. Saldo

No | Keterangan | Total (Rp)
1. | Total Pemasukan | Rp 5.000.000
2. | Total Pengeluaran | Rp.4.992.150
SALDO = PEMASUKAN - PENGELUARAN | | Rp 7.850
(Tujuh Ribu Delapan Ratus Lima Puluh Rupiah)

Lampiran 2. Nota Pembayaran No. | Tanggal
Keterangan | Nota Pembayaran | Jumlah

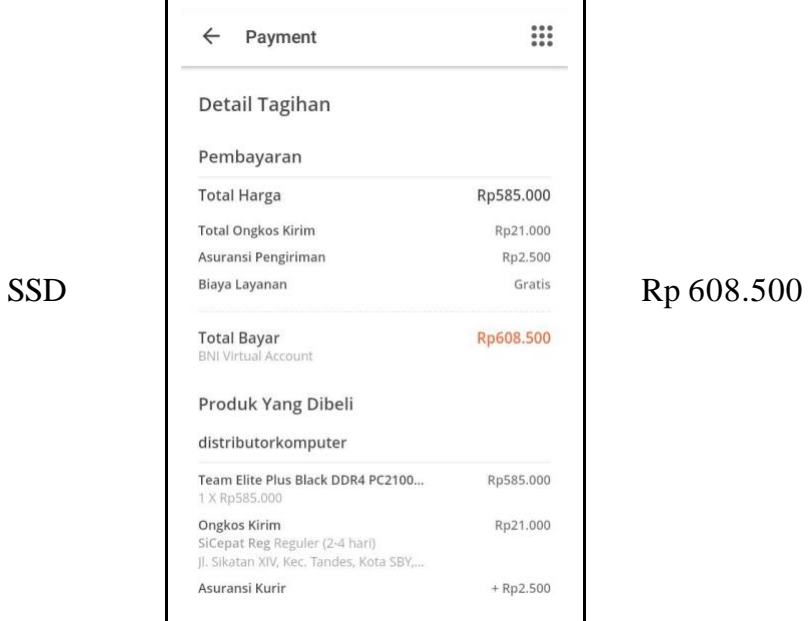
[picture p233: figure]
SSD

1. 28/0
8

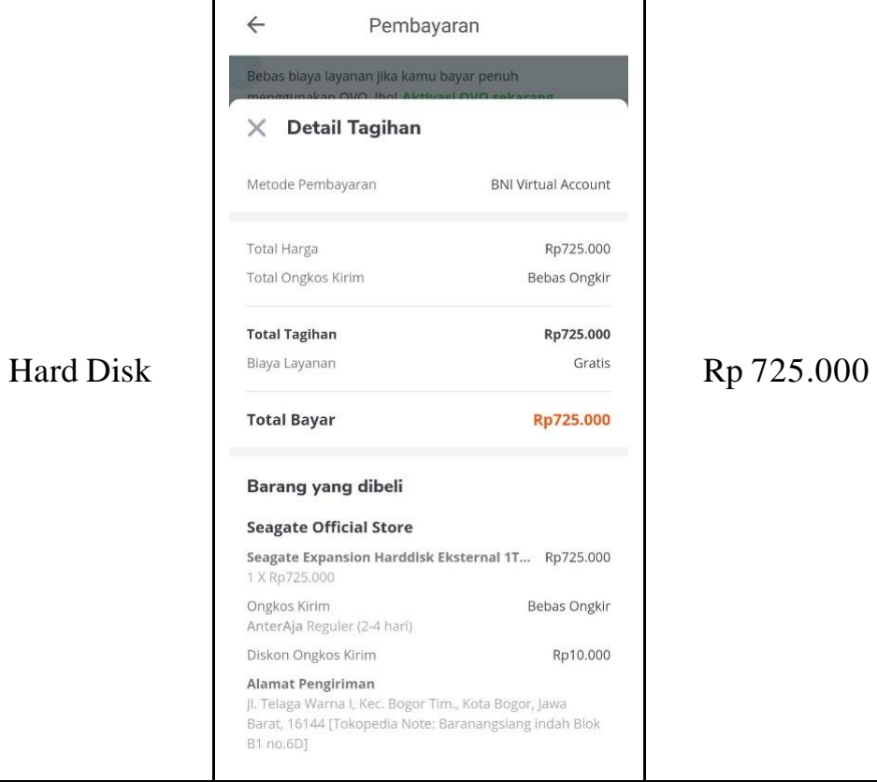
[picture p234: figure]
Hard Disk

2. 20/0
9

3. 28/0
9

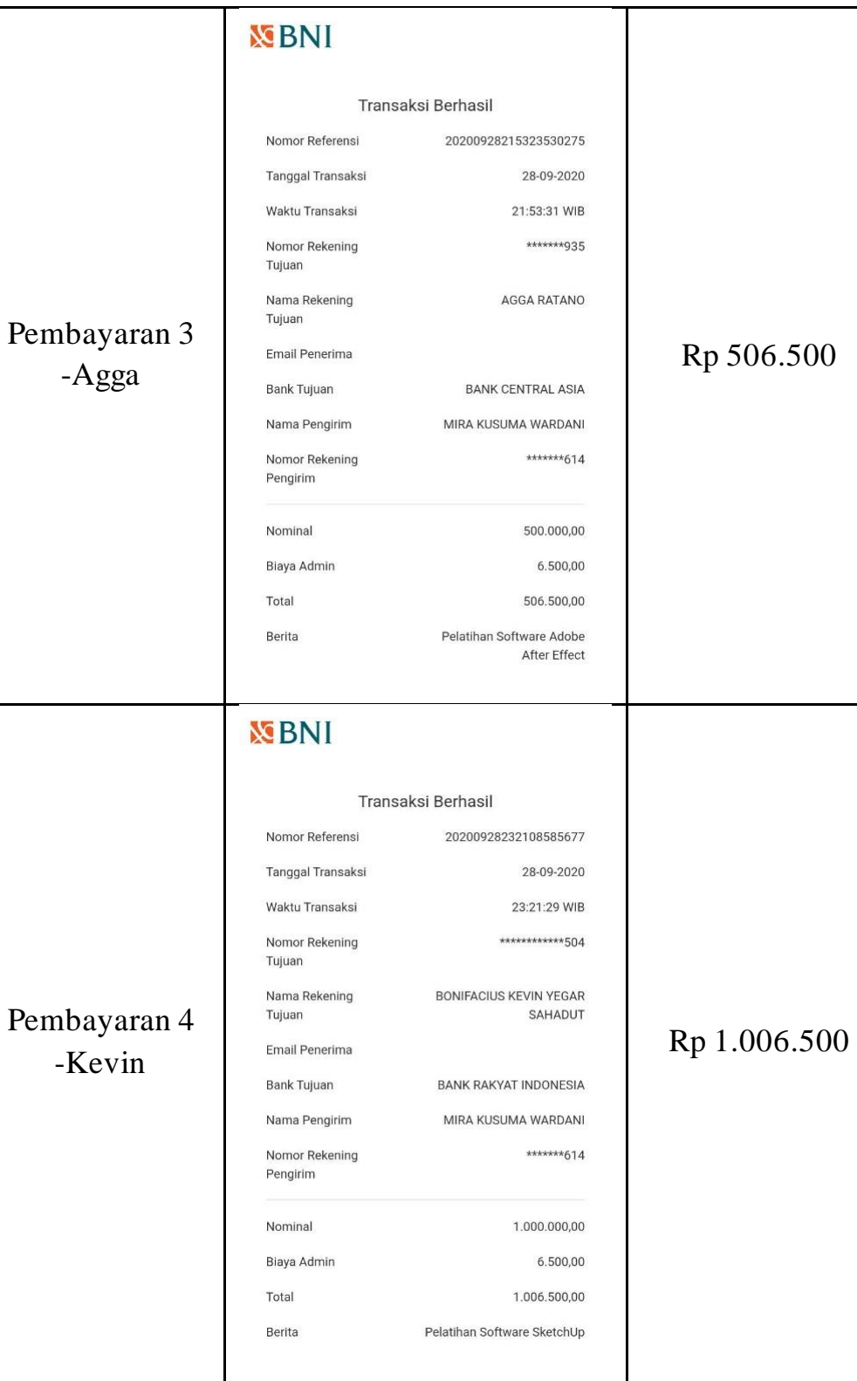
[picture p235: figure]
-Agga; Pembayaran 4; -Kevin

Pembayaran 3

4. 28/0
9

5.

24/0
9
Pulsa Arnold | Rp 198.550

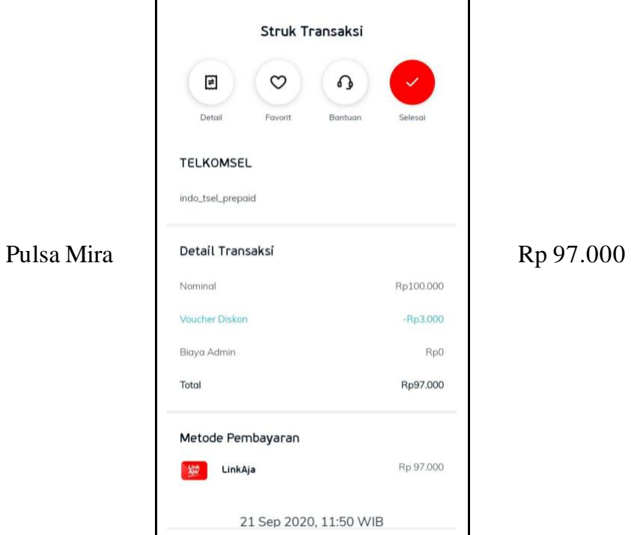
[picture p236: figure]
Pulsa Mira

6.

21/0
9

29/0
9

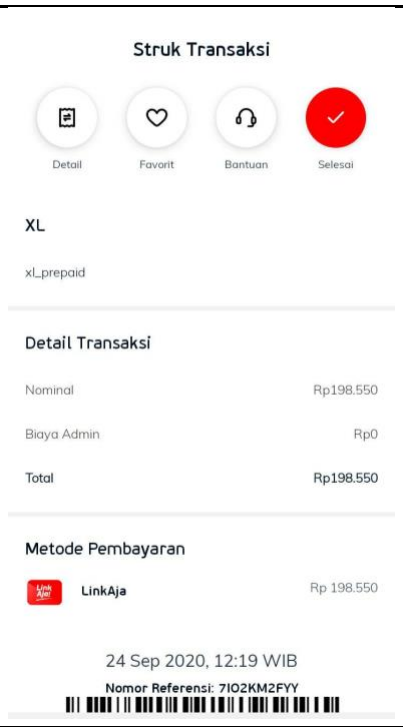
[picture p237: figure]

Pulsa Mira | Rp 100.000

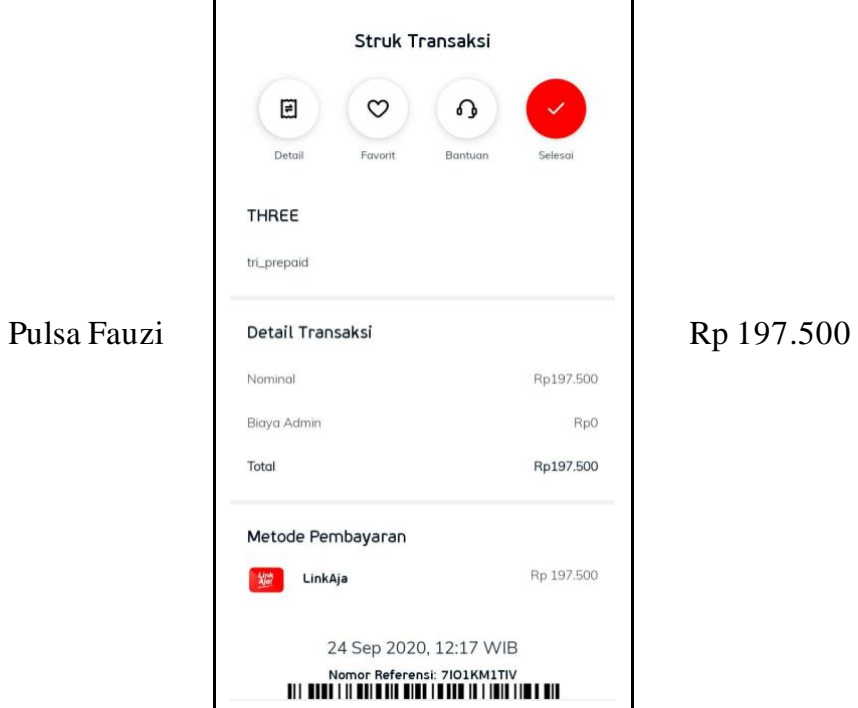
[picture p238: figure]
Pulsa Fauzi

7.

24/0
9

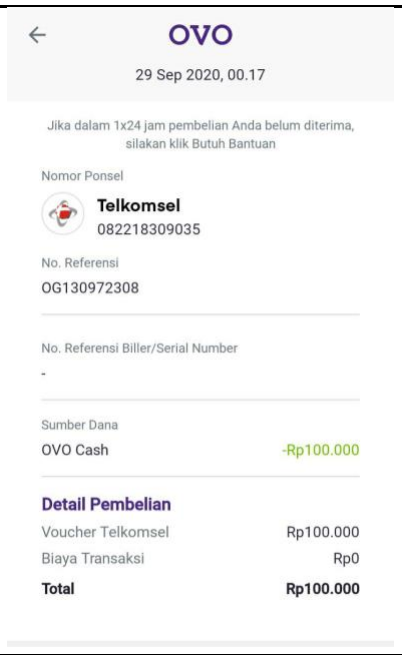
[picture p239: figure]

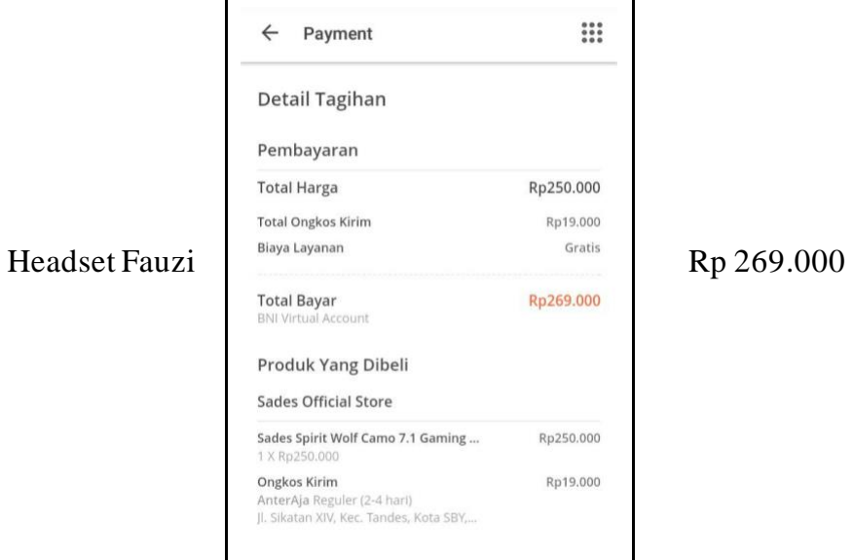
[picture p240: figure]
Headset Fauzi

8.

22/0
9

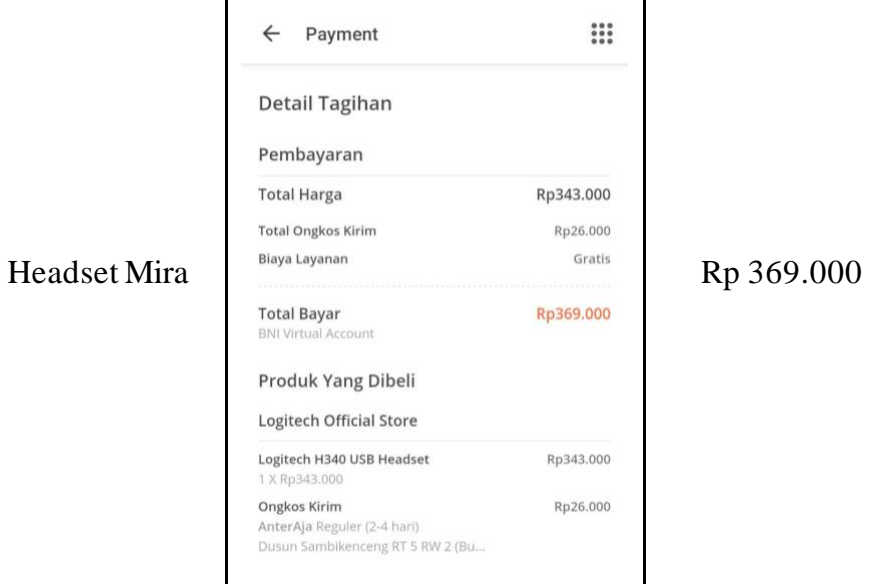
[picture p241: figure]
Headset Mira

9.

23/0
9

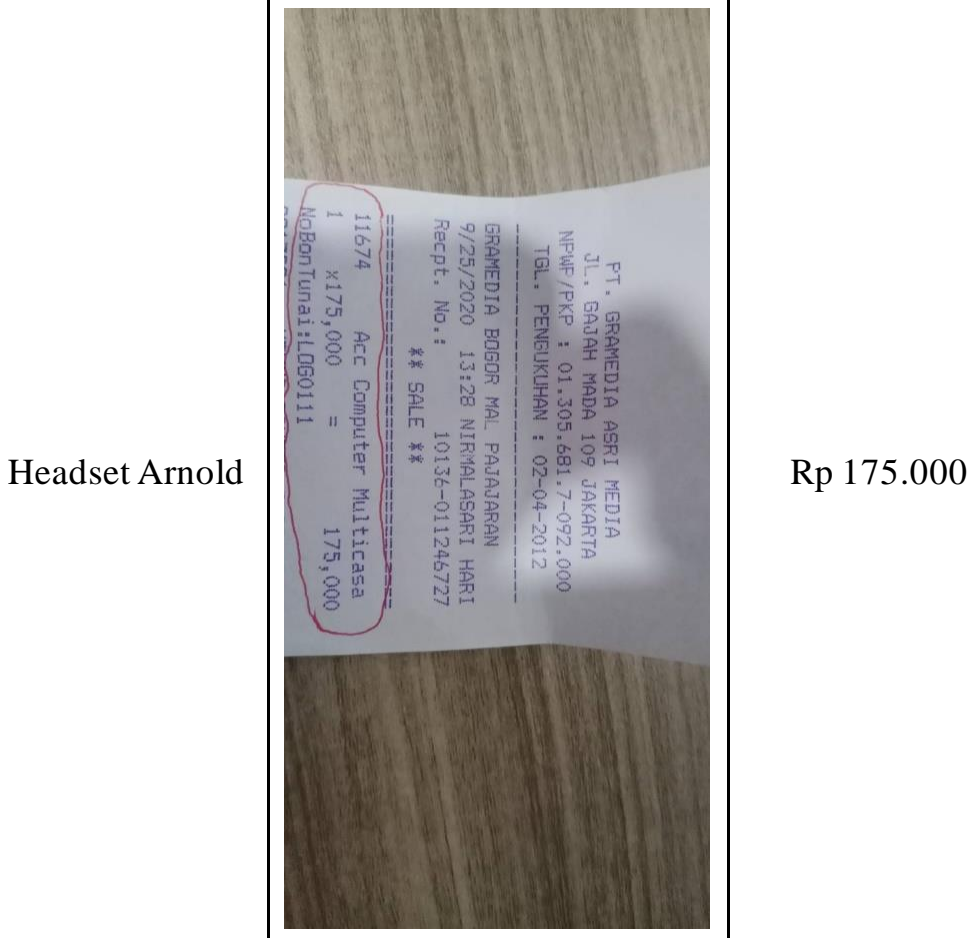
[picture p242: figure]
Headset Arnold

1
0.

25/0
9

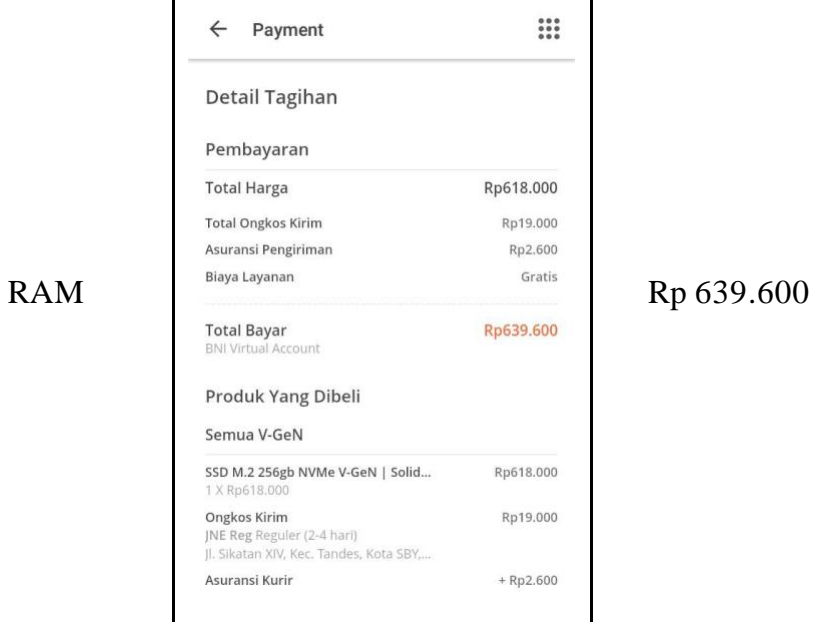
[picture p243: figure]
RAM

1
1.

28/0
8

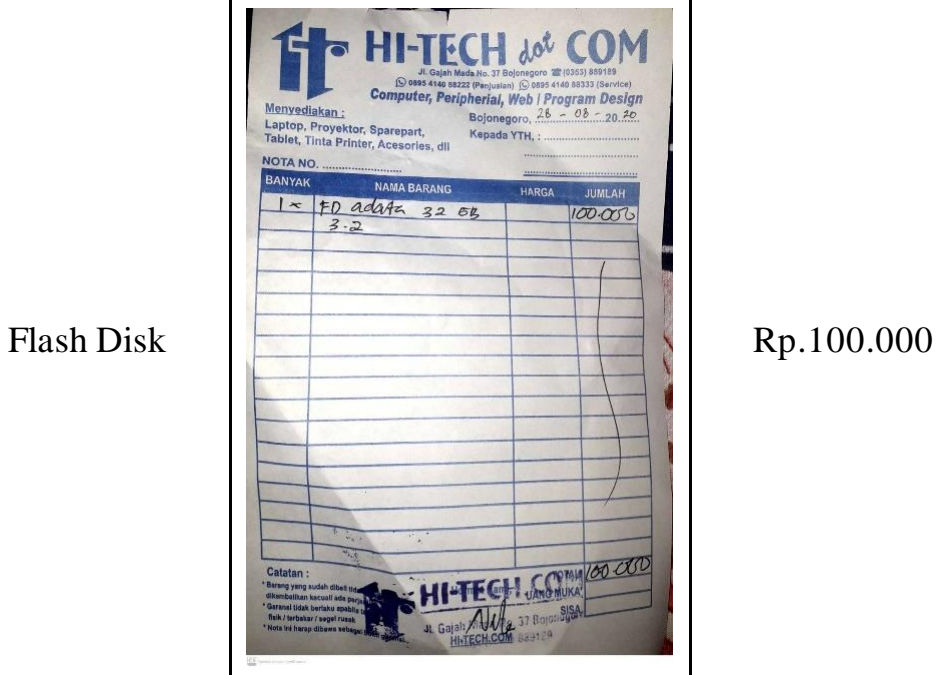
[picture p244: figure]
Flash Disk

1
2.

28/0
8
TOTAL | Rp.4.992.150

Lampiran 3. Bukti Pendukung Kegiatan No. | Tanggal | Keteranga n | Dokumentasi

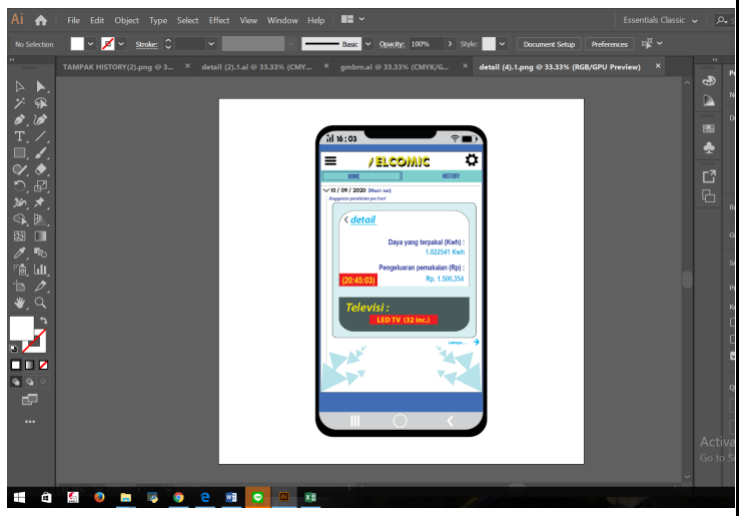
[picture p245: figure]

1. 24/0 | 9 | Kegiatan

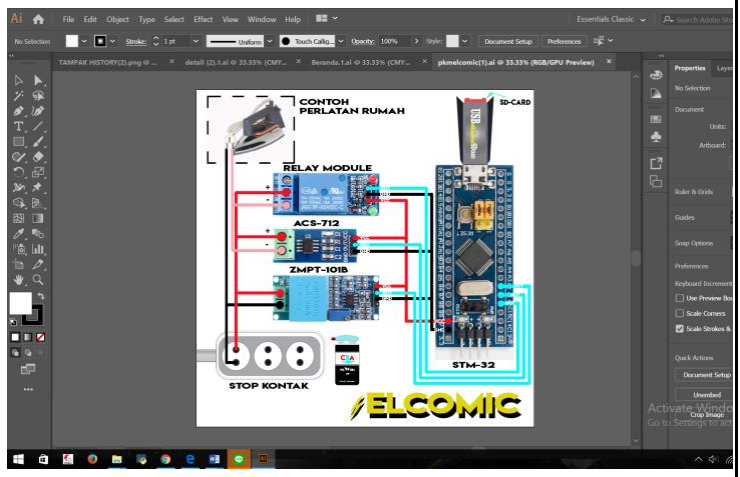
[picture p246: figure]

2. 26/0 | 9 | Kegiatan

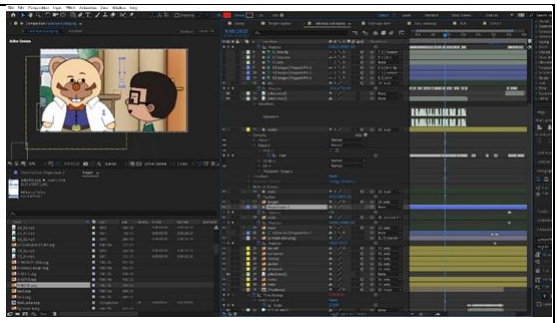
[picture p247: figure]

3. 27/0 | 9 | Kegiatan 3

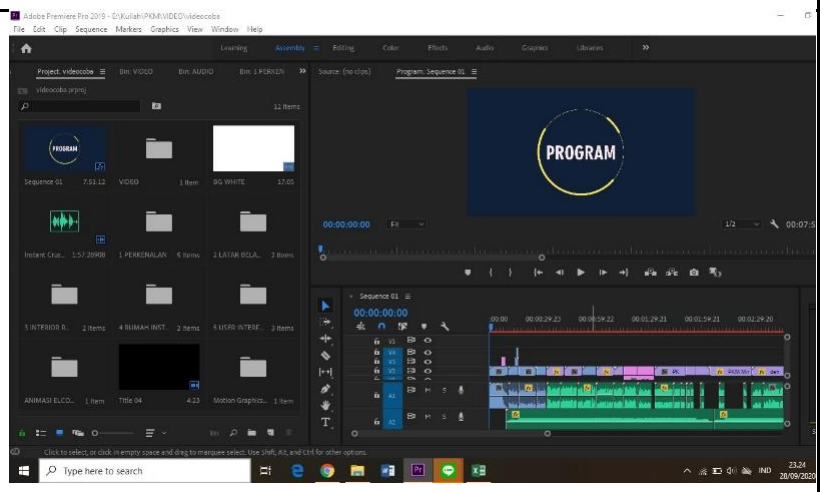
[picture p248: figure]

4. 28/0 | 9 | Kegiatan 4

Lampiran 4. Lain Lain
No. | Keterangan | Link
1. | Video Pelaksanaan PKM KC | https://youtu.be/fXeNl7Yi94w
