fariszuh/IoT-Concrete-Heat-Hidration/KALENDER KERJA/PPT Monev/BIKOM 1 FIXX.pptx

## PKM – KC : SISTEM AKUISISI DATA BERBASIS WIRELESS UNTUK EVALUASI EFEK PANAS HIDRASI BETON PADA UMUR AWAL

Institut Teknologi Sepuluh Nopember - Wikipedia bahasa Indonesia, ensiklopedia bebas

PKM – KC 2461

Dosen Pembimbing :
Ir. Faimun, M.sc., Ph.D.

## ANGGOTA TIM :

PKM – KC 2461

AHMAD DZIRULLAH AKBAR

MUHAMMAD FARIS
ZUHAIRI

HAKHI
GYA
YEKTIANTO

MUHAMMAD ALFIYAN ZULFA

TEKNIK
SIPIL
03111940000005

TEKNIK ELEKTRO
07111940000164

TEKNIK ELEKTRO
07111940000022

TEKNIK
SIPIL
5012201003

## WORK PACKAGES

## TABLE OF CONTENTS KETERBARUAN INOVASI 01

02

03

KEBERMANFAATAN
JANGKA PANJANG

WORK BREAKDOWN STRUCTURE

PKM – KC 2461

## Latar Belakang

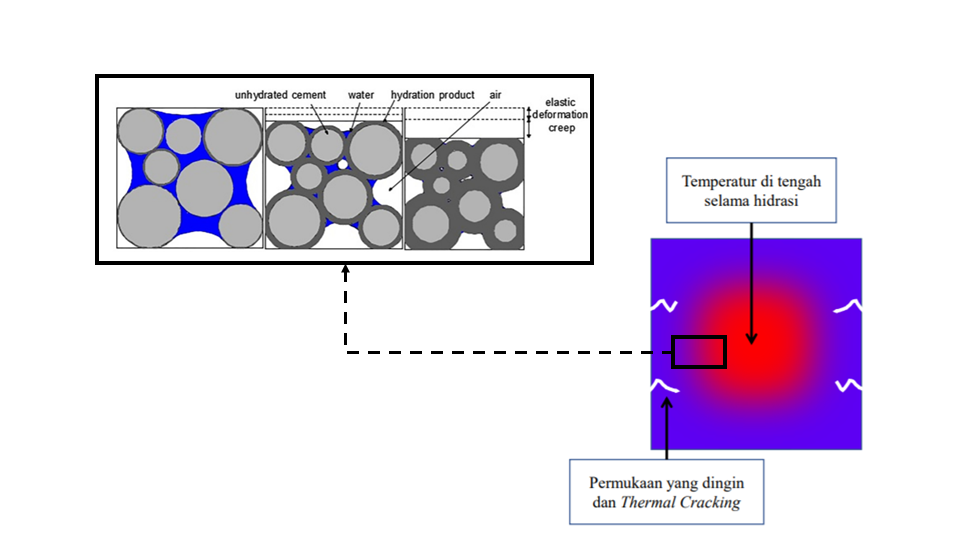
[picture p293: figure]

## Standardisasi yang digunakan

- Penyiapan Spesimen Uji
a. Mix design beton (ACI 211.1.91 dan SNI 03-3449-2002)
b. Uji konsistensi normal semen (ASTM C 187-16, SNI 03-6826-2002)
c. Uji setting time semen (ASTM C 191-3, SNI 15-2049-2004)
d. Uji saringan/lolos ayakan (ASTM C 117-95)
e. Uji slump (SNI 03-1972-1990)
f. Uji kuat tekan (SNI 03-1974-1990)
- Prasyarat Standardisasi Alat
a. Uji suhu internal beton segar (ASTM C 1064)
b. Uji autogenous shrinkage (ASTM C 1698-09)
c. Estimasi kematangan beton (ASTM C 1074)

## KETERBARUAN INOVASI

PKM – KC 2461

## KETERBARUAN INOVASI

Dikutip dari,
- Pengukuran dan monitoring suhu dan susut akibat hidrasi umumnya menggunakan data logger, sensor suhu dan pengukur displacement yang dihasilkan tiap waktu yang ditetapkan. Data yang tersimpan diakusisi oleh data logger menuju komputer.
- Sensor suhu yang digunakan adalah thermocouple. Pada penelitian (Kim et al., 2009) sensor yang digunakan adalah DS18B20.
- Sedangkan, pengukuran susut yang ada saat ini menggunakan LVDT, dilatometer, dan strain gauge (Holt, 2001; Springenschmid, 2004).
- Pengolahan data untuk analisis masih manual.

ASTM C1698

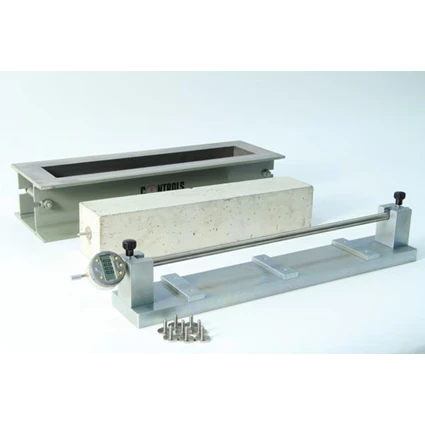
[picture p294: figure]

PKM – KC 2461

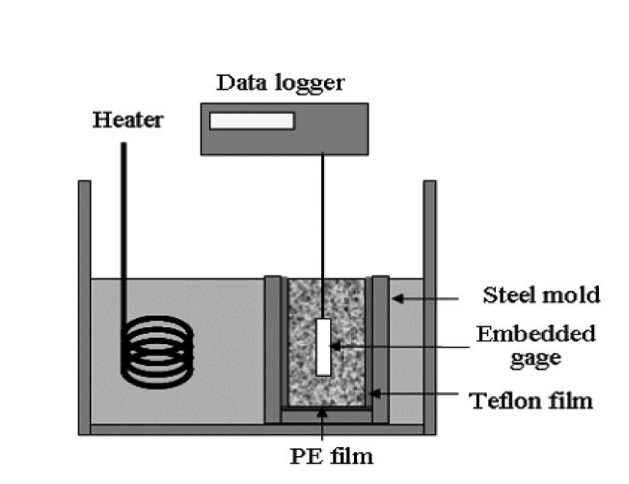
[picture p295: figure]

## KETERBARUAN INOVASI

Oleh karena itu,
Pada PKM – KC kali ini, kami melakukan pembaruan terhadap alat yang sudah ada, pembaruan tersebut meliputi :
- Penggunaan sistem monitoring dengan automasi transfer data ke cloud database sebagai wadah penyimpanan dan pengolahan data.
- Modifikasi digital kaliper yang semula menggunakan jangka sorong digital, menjadi alat pengukur susut beton yang bekerja bersamaan dengan thermocouple.

PKM – KC 2461

## Slide 10

Algoritma Pengolahan Data


Cloud data base

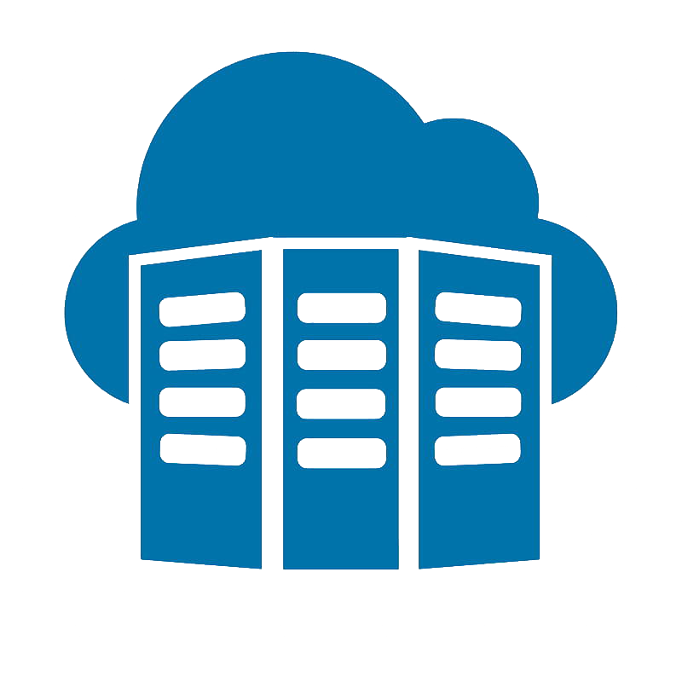
[picture p296: figure]
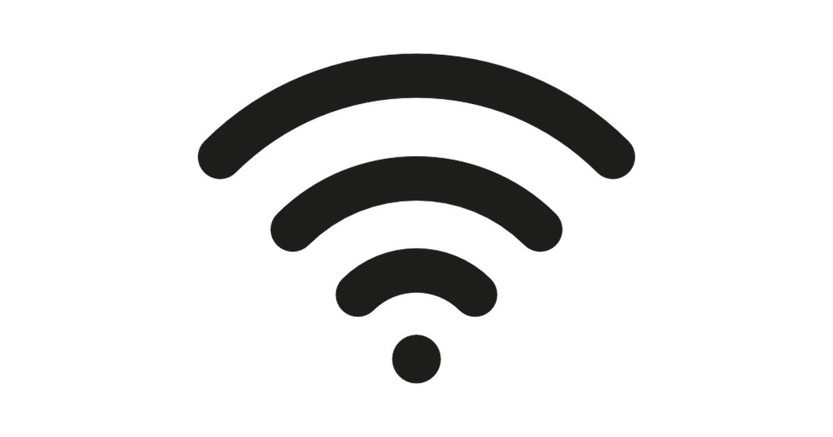
[picture p297: figure]
Wifi Signal free vector icons designed by Freepik | Wifi icon, Vector icon design, Icon design

Penyimpanan Offline

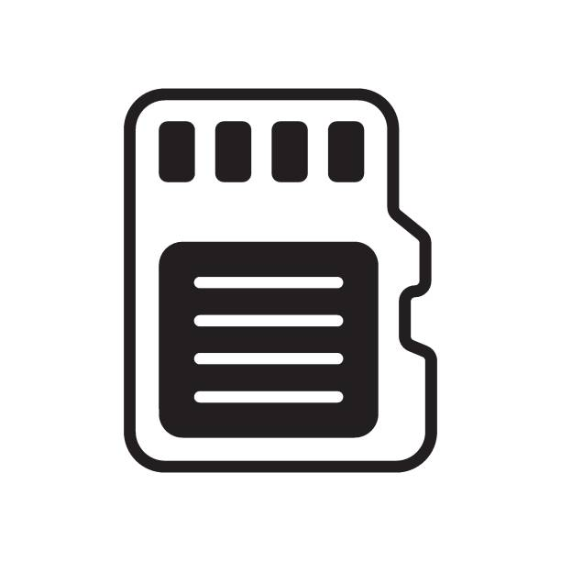
[picture p298: figure]
Micro Sd Card Vector Art, Icons, and Graphics for Free Download

Mikrokontroller ESP32

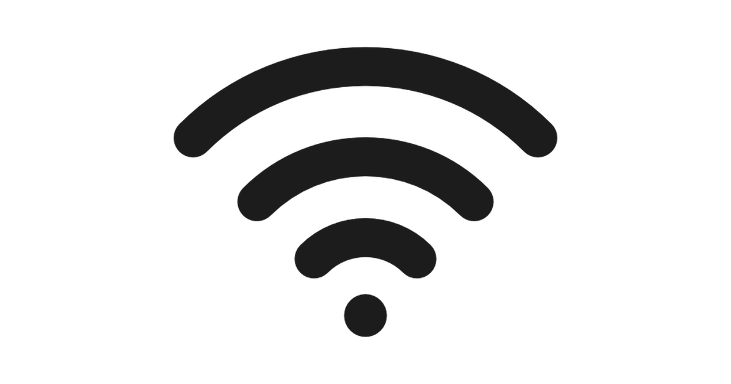
[picture p299: figure]
Wifi Signal free vector icons designed by Freepik | Wifi icon, Vector icon design, Icon design

A

A

Tampak Depan

Unscaled

Digital Caliper


Potongan A-A

Unscaled

Cor Beton

Cetakan Beton

Thermocouple

Insulasi

## KETERBARUAN INOVASI


## OUTPUT:

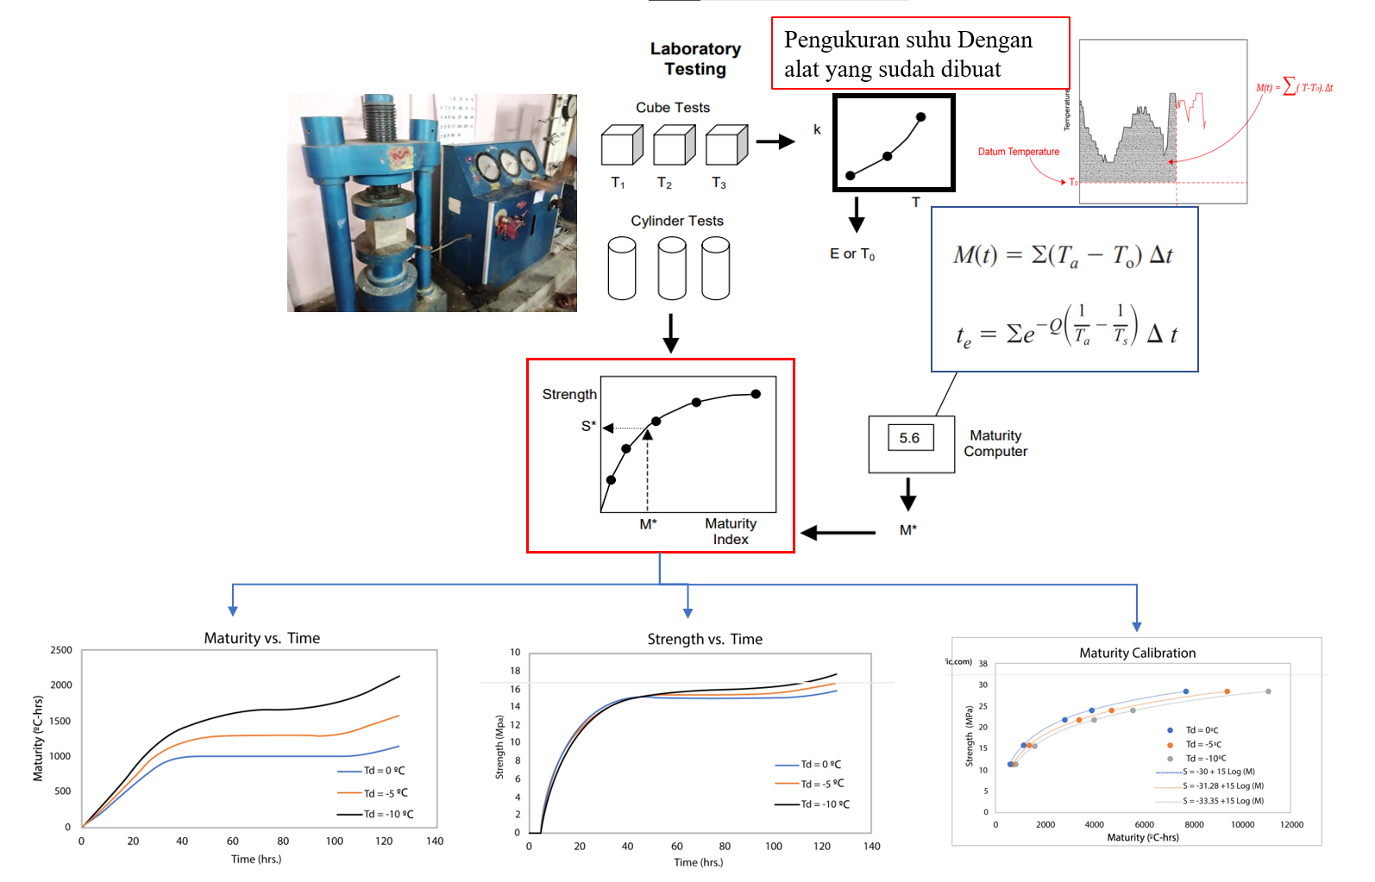
[picture p300: figure]
P670#yIS1

## Slide 13

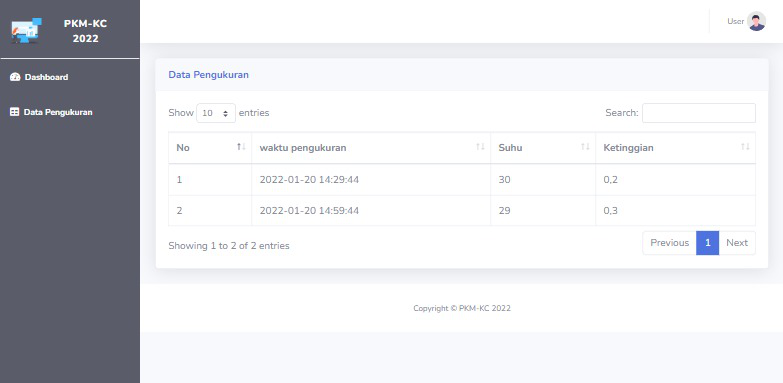
[picture p301: figure]
P675#yIS1

## Slide 14

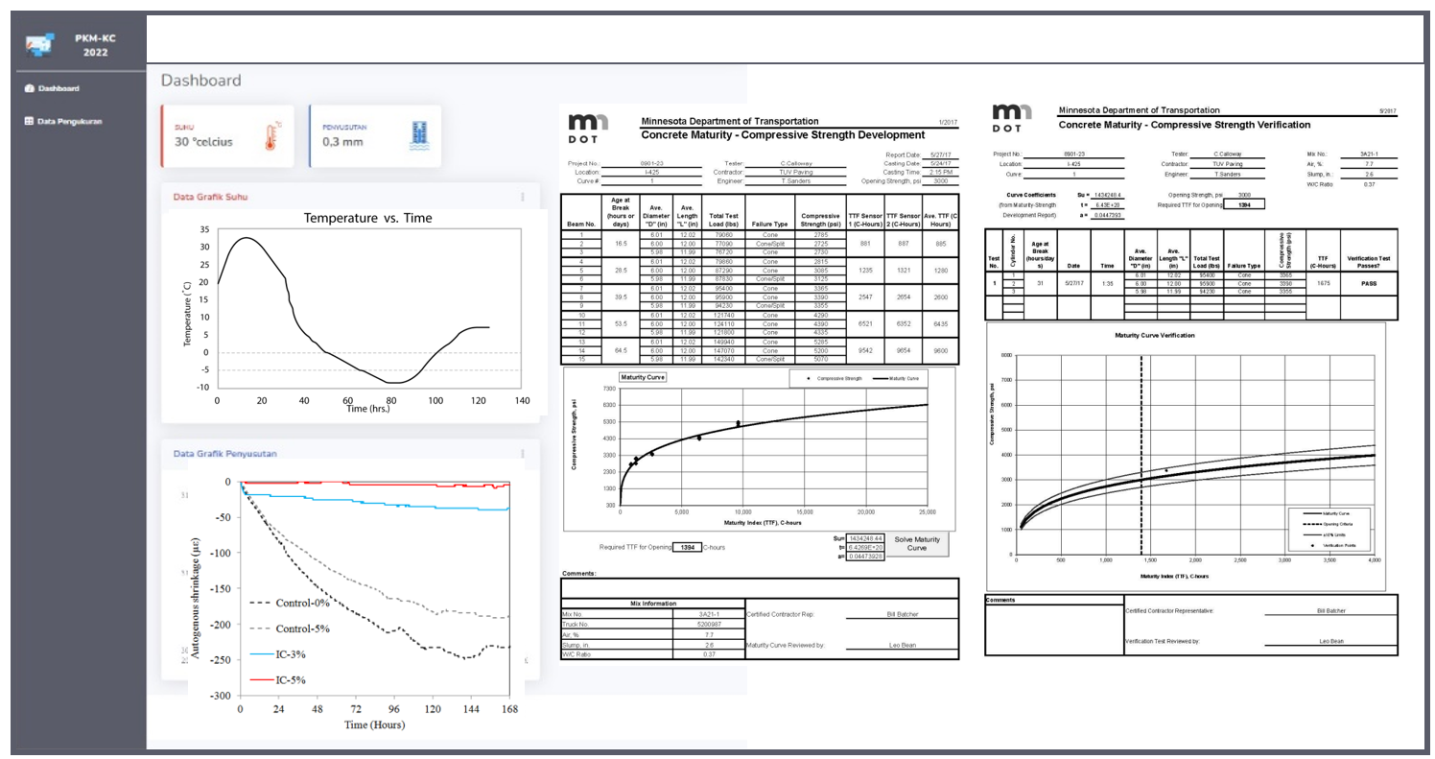
[picture p302: figure]
P673#yIS1

## KEBERMANFAATAN JANGKA PANJANG

PKM – KC 2461

## KEBERMANFAATAN JANGKA PANJANG

Pada dasarnya, sistem akuisisi ini bertujuan untuk melakukan evaluasi kematangan beton akibat efek panas hidrasi pada beton umur awal. Output dari pengukusan sistem akuisisi ini sendiri adalah :
- Maturity Index dari Beton
- Grafik hubungan antara susut dan perubahan suhu akibat panas hidrasi yang terjadi pada beton

PKM – KC 2461

## KEBERMANFAATAN JANGKA PANJANG

Dua output tersebut digunakan untuk memprediksi kekuatan beton yang diuji.
Dengan kata lain, pengetesan suhu dan susut pada beton umur awal ini bertujuan untuk :
- Memprediksi apakah kuat tekan beton yang digunakan sudah sesuai dengan kuat tekan beton yang telah direncanakan sebelumnya.
- Mengukur seberapa besar pengaruh panas hidrasi pada kuat tekan beton.
Jadi, dengan adanya inovasi ini maka akan meningkatkan nilai akurasi dari pengukuran suhu dan susut pada beton. Sehingga nilai kuat beton hasil pengolahan data adalah nilai kuat beton yang paling sesuai dengan kondisi suhu dan susut yang telah dicatat oleh system.

PKM – KC 2461

## KEBERMANFAATAN JANGKA PANJANG

Jika ditinjau lebih jauh, inovasi ini akan sangat bermanfaat dibidang konstruksi kedepannya. Mengingat akan dilakukan proyek pembangunan IKN Baru yang tentunya akan melakukan pembangunan besar-besaran di bidang konstruksi.
Oleh karena itu, diharapkan alat ini nantinya dapat menjadi salah satu alat uji yang digunakan oleh pelaku proyek pembangunan IKN Baru untuk pengujian beton.

PKM – KC 2461

## WORK BREAKDOWN STRUCTURE

PKM – KC 2461

## WORK BREAKDOWN STRUCTURE

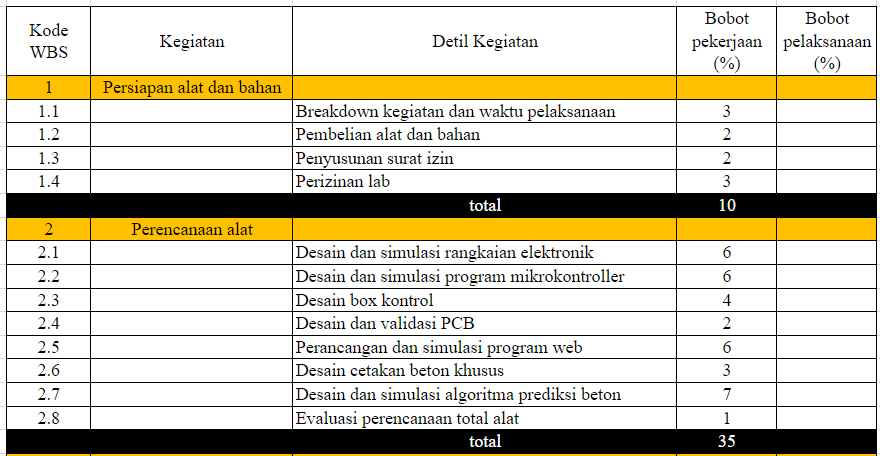
[picture p303: figure]

PKM – KC 2461

## WORK BREAKDOWN STRUCTURE

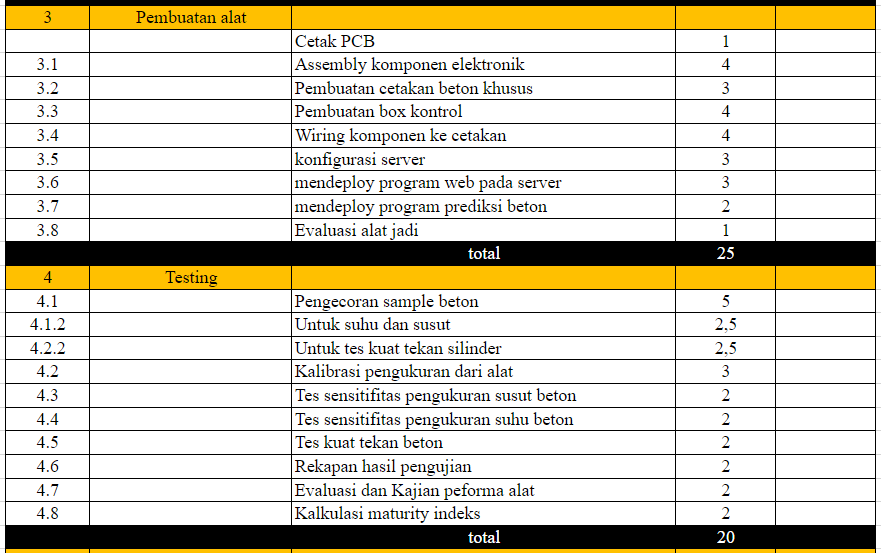
[picture p304: figure]

PKM – KC 2461

## WORK BREAKDOWN STRUCTURE

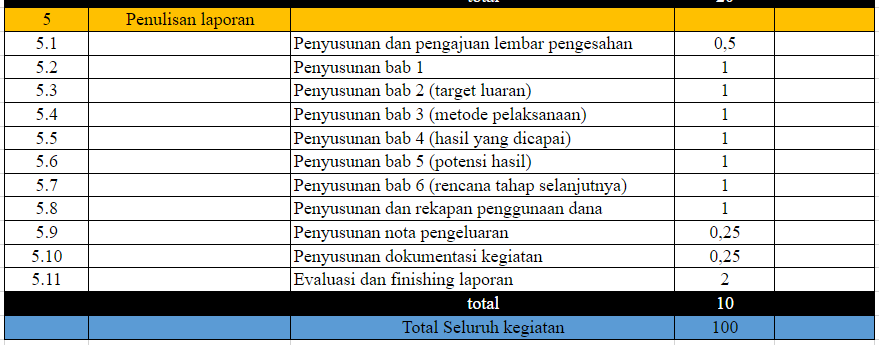
[picture p305: figure]

Total Rancangan Anggaran Biaya : Rp6.950.000

PKM – KC 2461

## Timeline

## Detail Rincian RAB

## THANK YOU!
