fariszuh/IoT-Concrete-Heat-Hidration/KALENDER KERJA/Progress pelaksanaan/Progreess kerja.pptx

## 30/05/2022 → Breakdown kegiatan dan revisi anggaran
