fariszuh/IoT-Concrete-Heat-Hidration/Daftar Pustaka/Maturity/20220627_205502.jpg

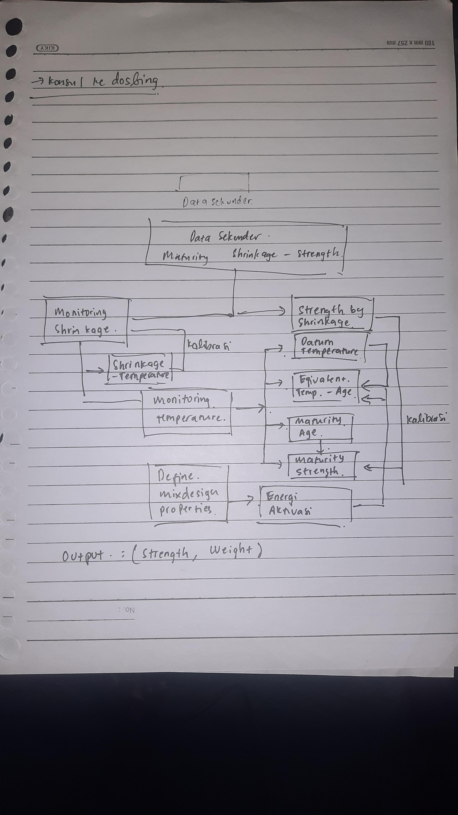
Daftar Pustaka/Maturity/20220627_205502.jpg
