fariszuh/IoT-Concrete-Heat-Hidration/Daftar Pustaka/Maturity/Calculation of Index Maturity.png

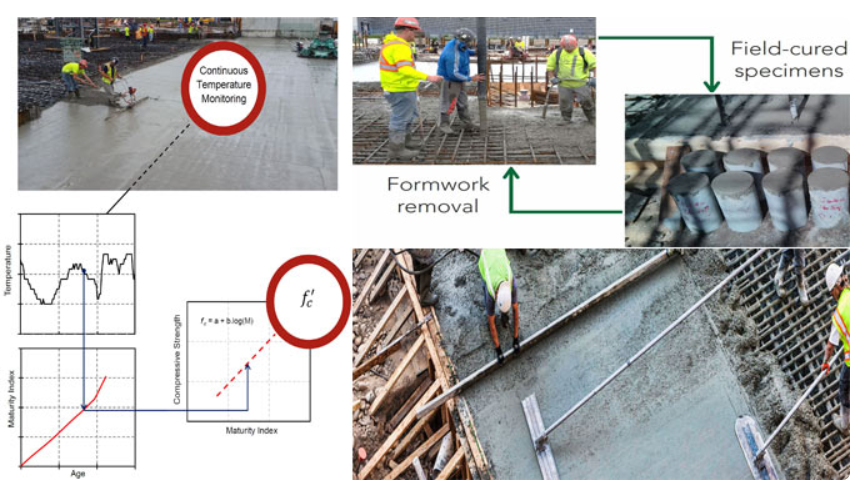
Daftar Pustaka/Maturity/Calculation of Index Maturity.png
