fariszuh/IoT-Concrete-Heat-Hidration/Daftar Pustaka/Maturity/Concrete prediction/WhatsApp Image 2022-09-01 at 14.39.11.jpeg

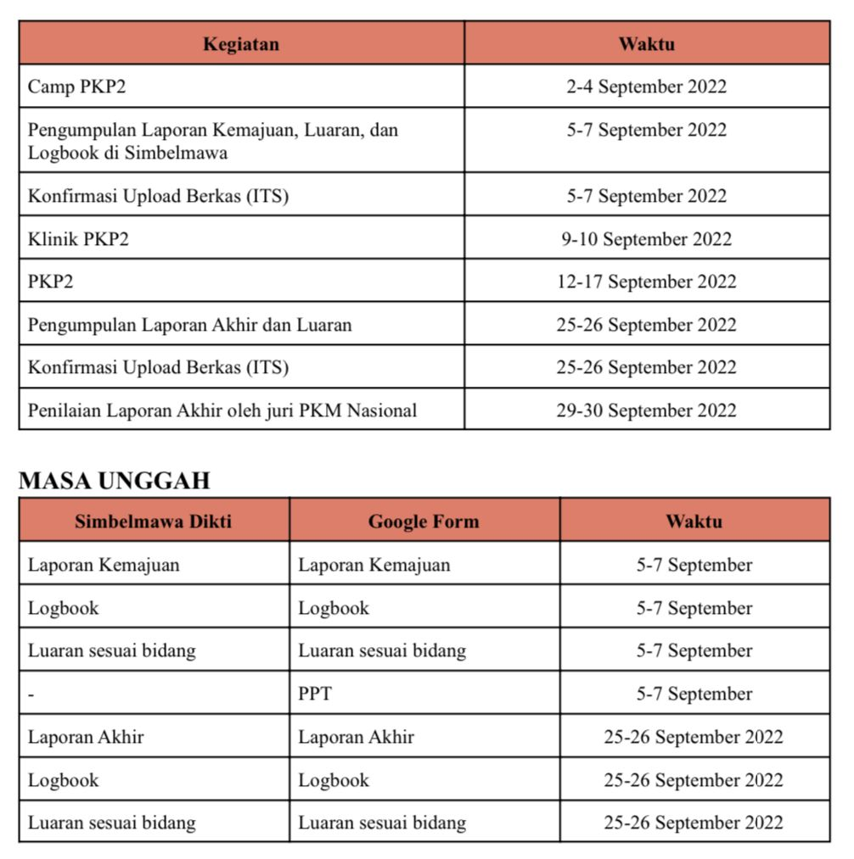
Daftar Pustaka/Maturity/Concrete prediction/WhatsApp Image 2022-09-01 at 14.39.11.jpeg
