fariszuh/IoT-Concrete-Heat-Hidration/Dokumentasi/Cuplikan layar 2022-05-30 192725.png

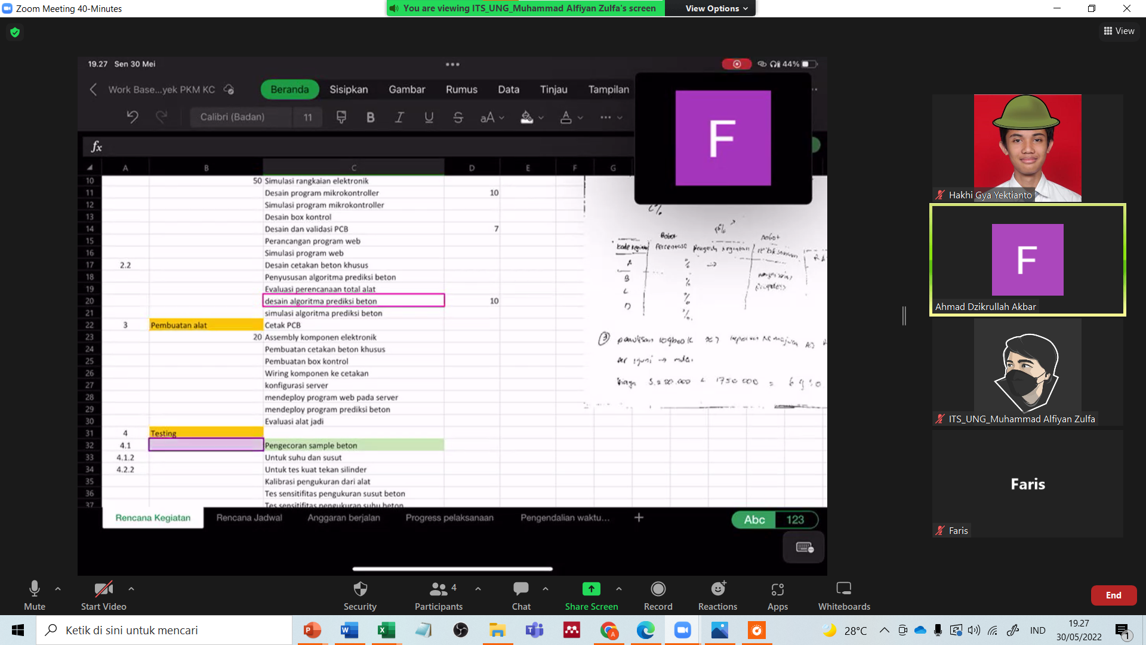
Dokumentasi/Cuplikan layar 2022-05-30 192725.png
