fariszuh/IoT-Concrete-Heat-Hidration/Dokumentasi/Cuplikan layar 2022-12-15 222952.jpg

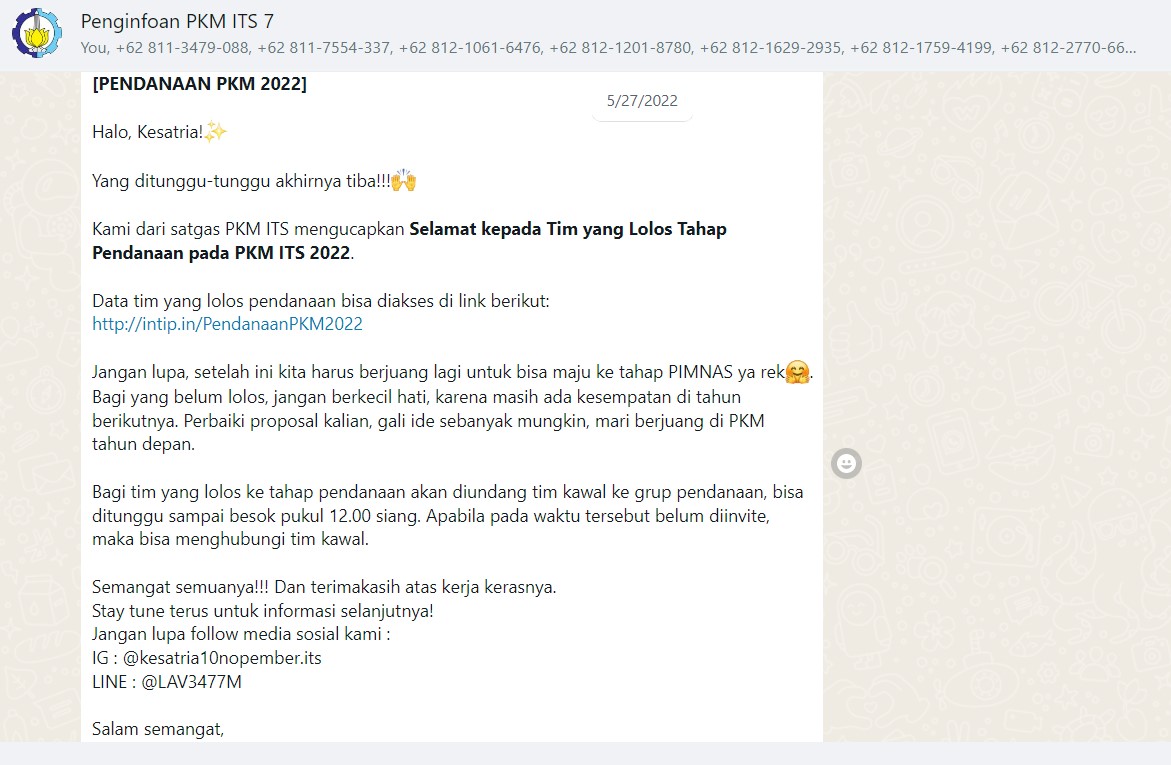
Dokumentasi/Cuplikan layar 2022-12-15 222952.jpg
