fariszuh/IoT-Concrete-Heat-Hidration/Dokumentasi/Cuplikan layar 2022-12-15 223126.jpg

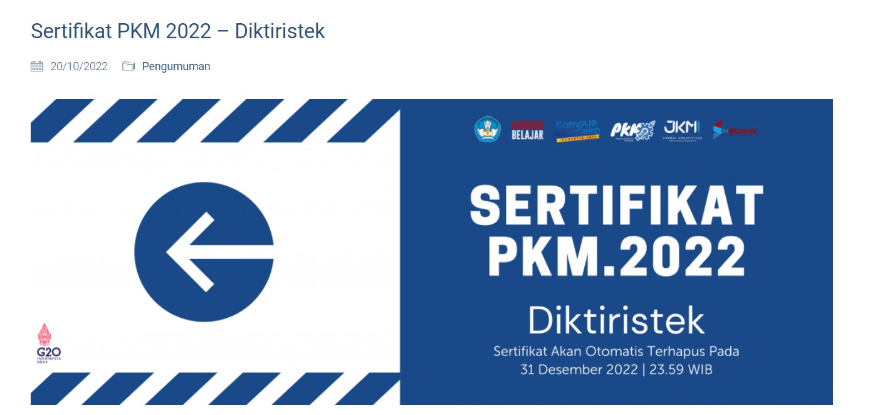
Dokumentasi/Cuplikan layar 2022-12-15 223126.jpg
