fariszuh/IoT-Concrete-Heat-Hidration/Dokumentasi/identifikasi caliper.jpg

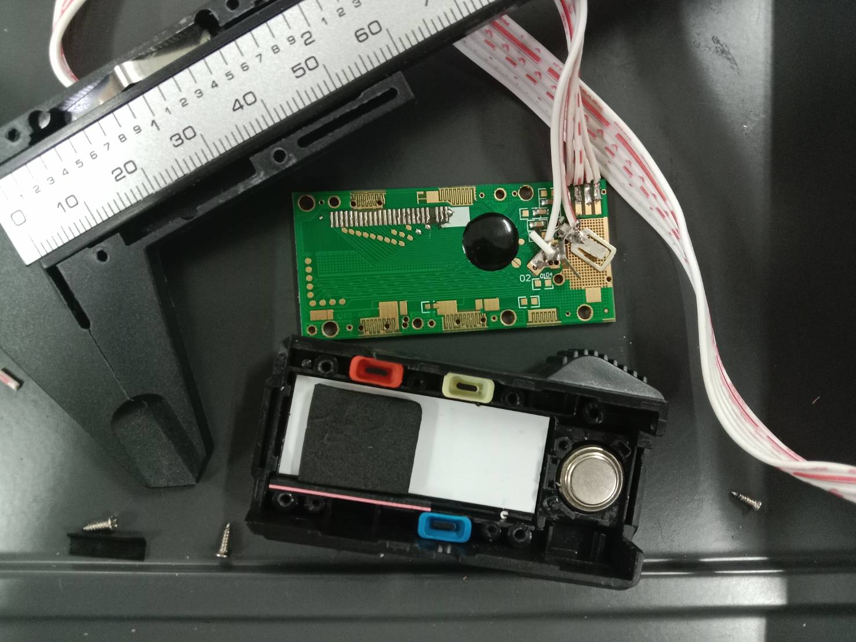
Dokumentasi/identifikasi caliper.jpg
