fariszuh/IoT-Concrete-Heat-Hidration/Dokumentasi/Sosialisasi/WhatsApp Image 2022-05-28 at 20.03.18.jpeg

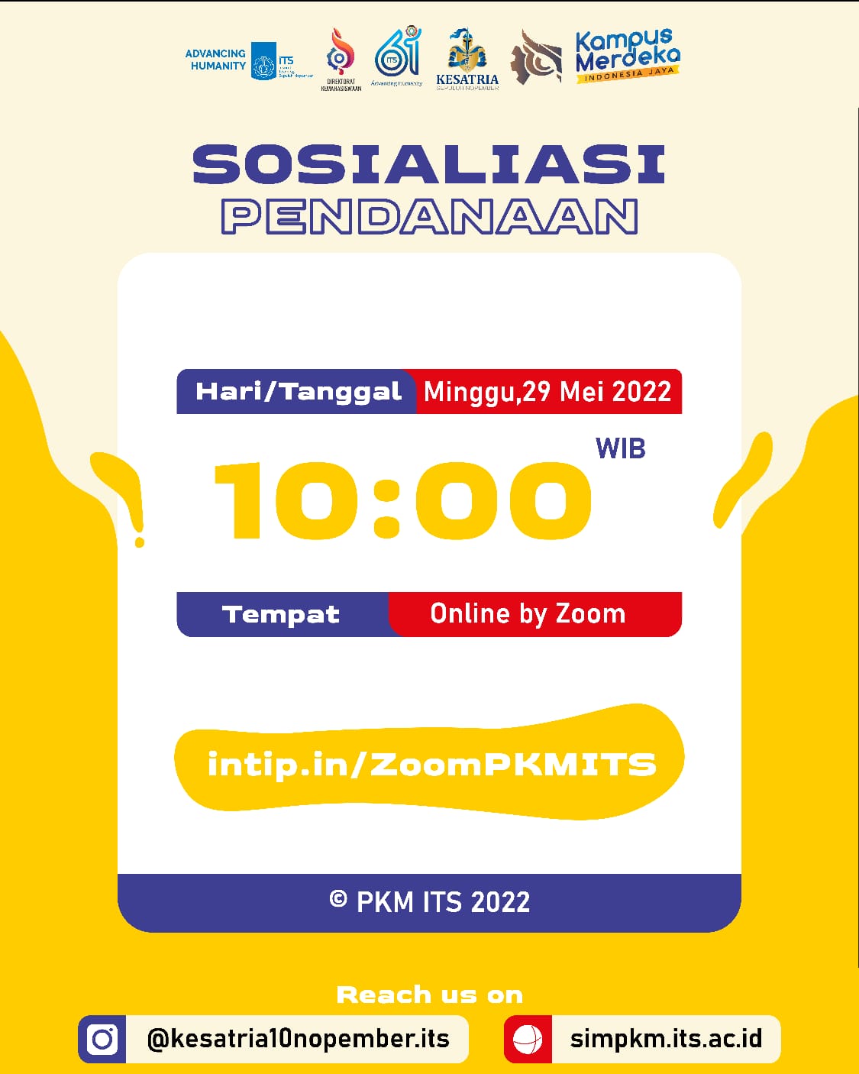
Dokumentasi/Sosialisasi/WhatsApp Image 2022-05-28 at 20.03.18.jpeg
