fariszuh/IoT-Concrete-Heat-Hidration/Dokumentasi/Sosialisasi/WhatsApp Image 2022-05-29 at 10.45.23.jpeg

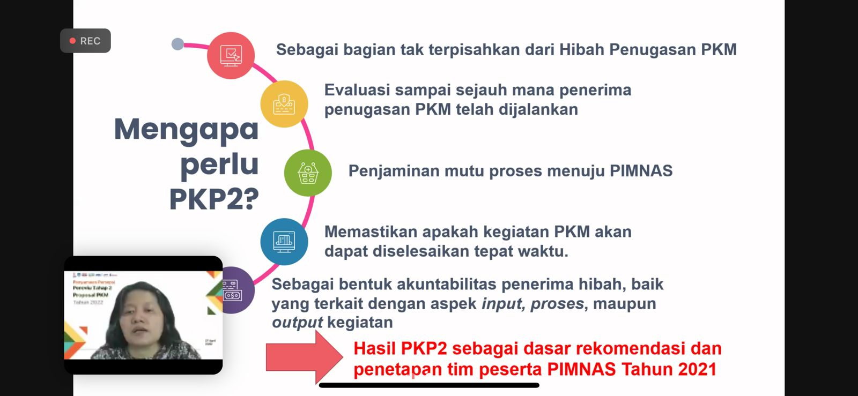
Dokumentasi/Sosialisasi/WhatsApp Image 2022-05-29 at 10.45.23.jpeg
