fariszuh/IoT-Concrete-Heat-Hidration/Dokumentasi/Sosialisasi/WhatsApp Image 2022-05-29 at 13.06.50.jpeg

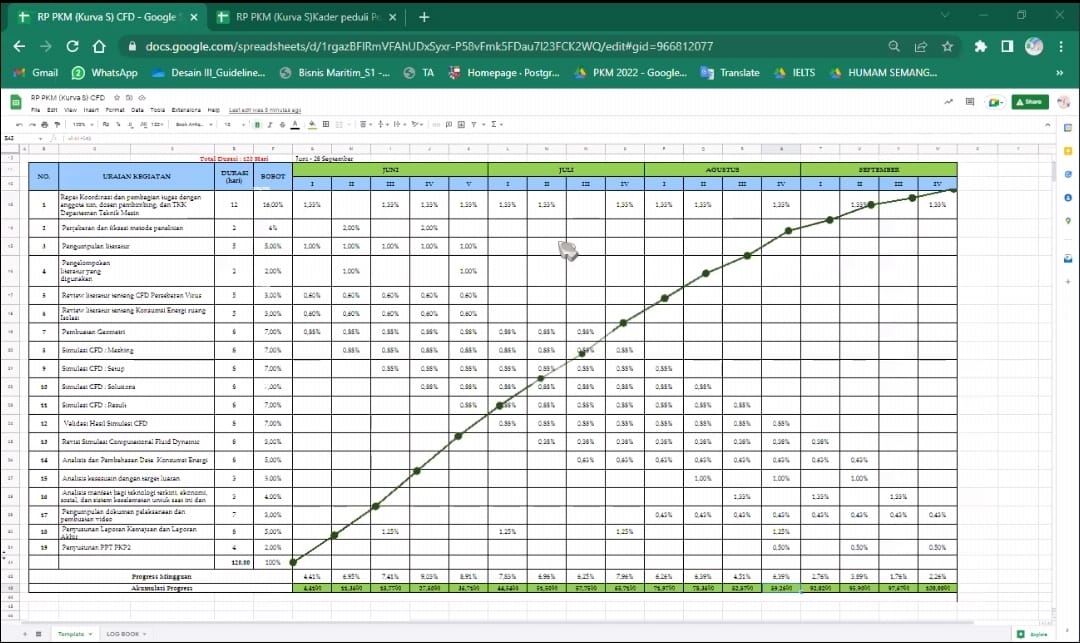
Dokumentasi/Sosialisasi/WhatsApp Image 2022-05-29 at 13.06.50.jpeg
