fariszuh/IoT-Concrete-Heat-Hidration/Dokumentasi/Sosialisasi/WhatsApp Image 2022-05-29 at 13.06.52 (1).jpeg

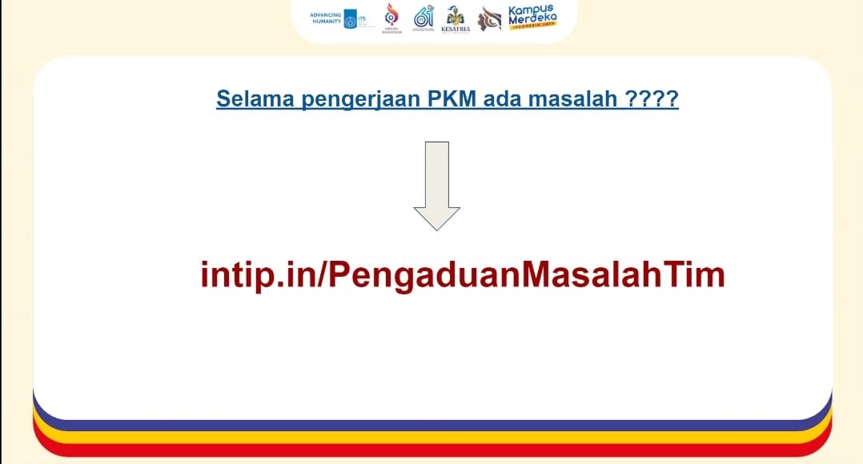
Dokumentasi/Sosialisasi/WhatsApp Image 2022-05-29 at 13.06.52 (1).jpeg
