fariszuh/IoT-Concrete-Heat-Hidration/Dokumentasi/WhatsApp Image 2022-05-29 at 10.45.27.jpeg

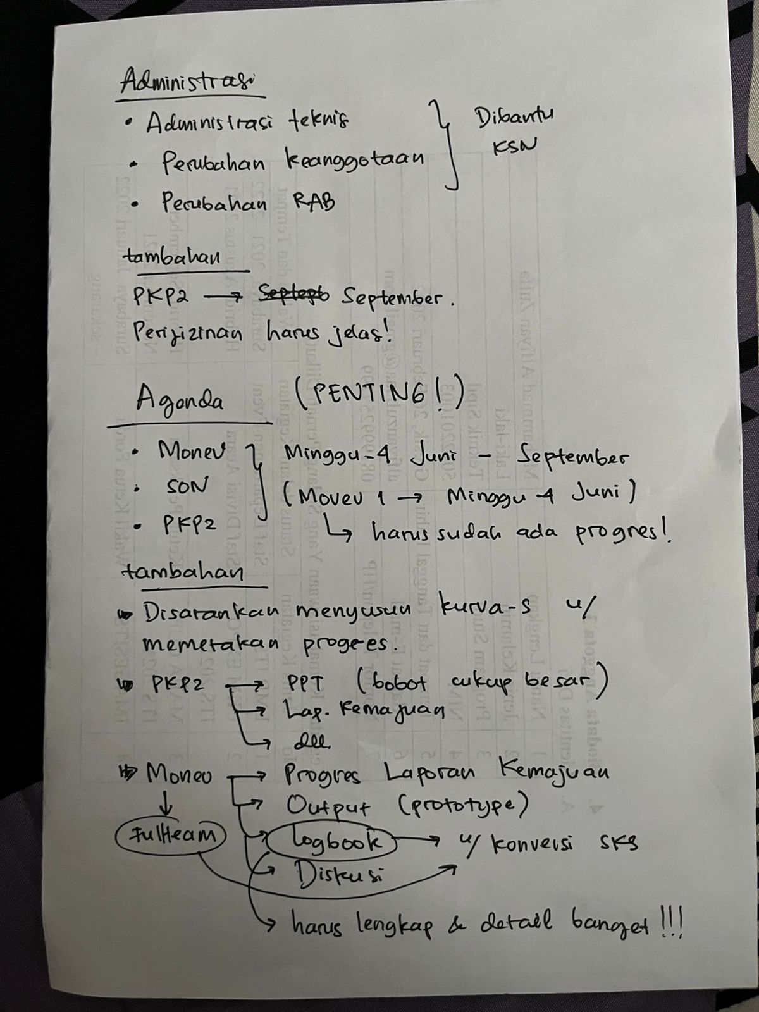
Dokumentasi/WhatsApp Image 2022-05-29 at 10.45.27.jpeg
