fariszuh/IoT-Concrete-Heat-Hidration/Dokumentasi/WhatsApp Image 2022-05-30 at 18.29.06.jpeg

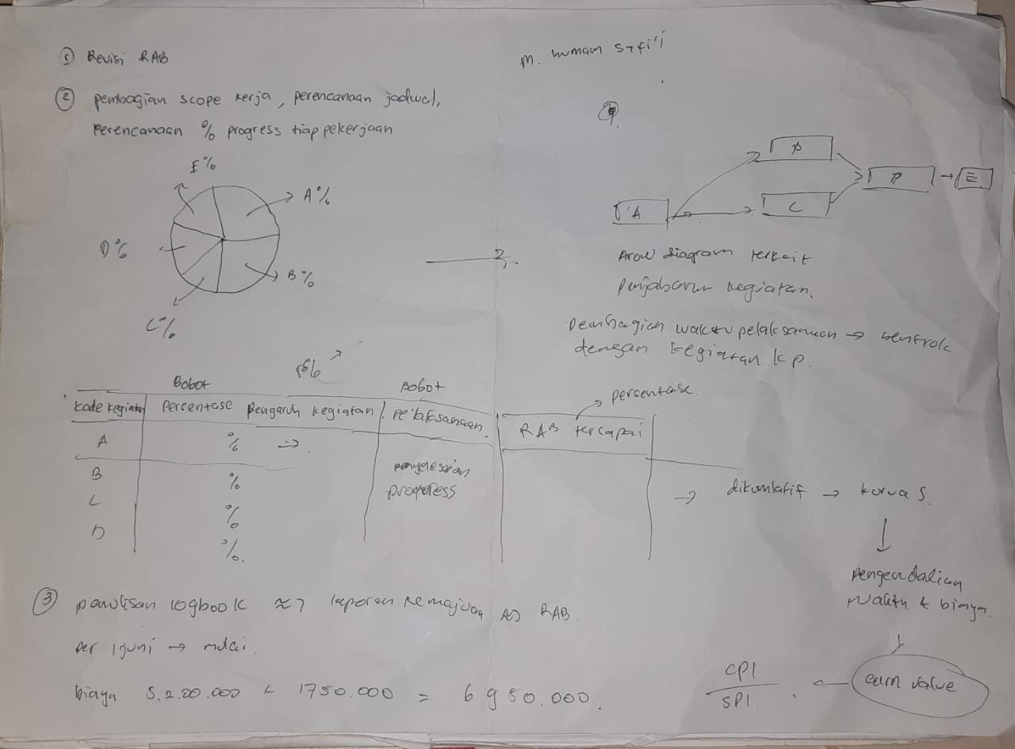
Dokumentasi/WhatsApp Image 2022-05-30 at 18.29.06.jpeg
