fariszuh/IoT-Concrete-Heat-Hidration/Dokumentasi/WhatsApp Image 2022-06-24 at 21.39.59.jpeg

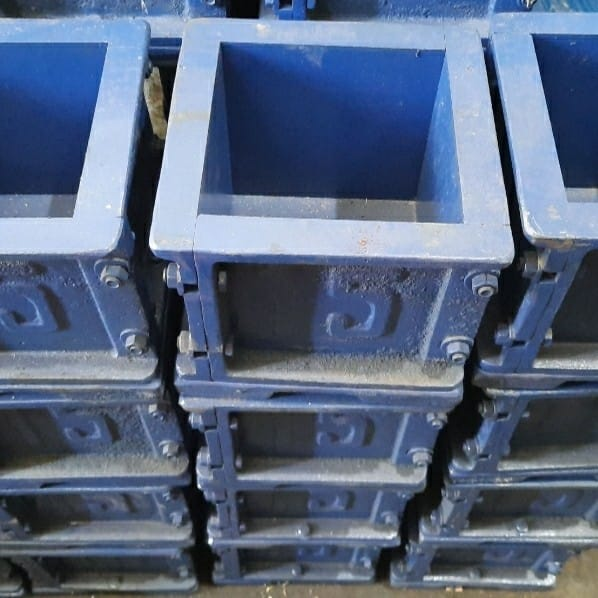
Dokumentasi/WhatsApp Image 2022-06-24 at 21.39.59.jpeg
