fariszuh/IoT-Concrete-Heat-Hidration/Dokumentasi/WhatsApp Image 2022-07-04 at 14.36.48.jpeg

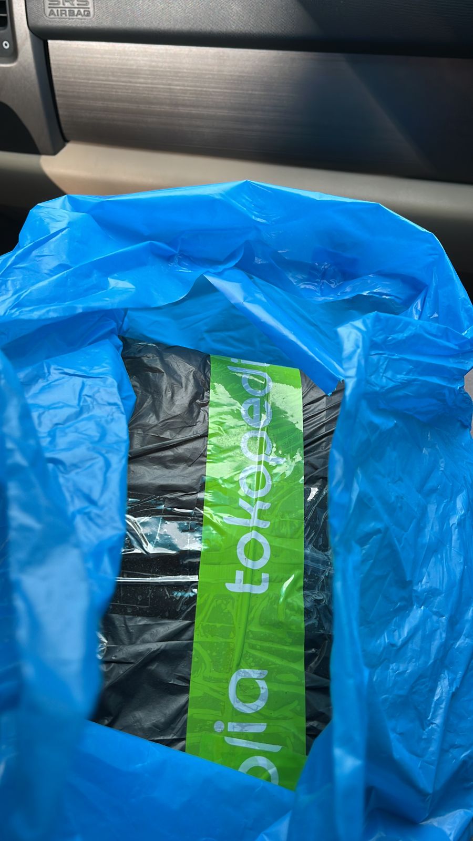
Dokumentasi/WhatsApp Image 2022-07-04 at 14.36.48.jpeg
