fariszuh/IoT-Concrete-Heat-Hidration/Dokumentasi/WhatsApp Image 2022-07-06 at 11.50.43.jpeg

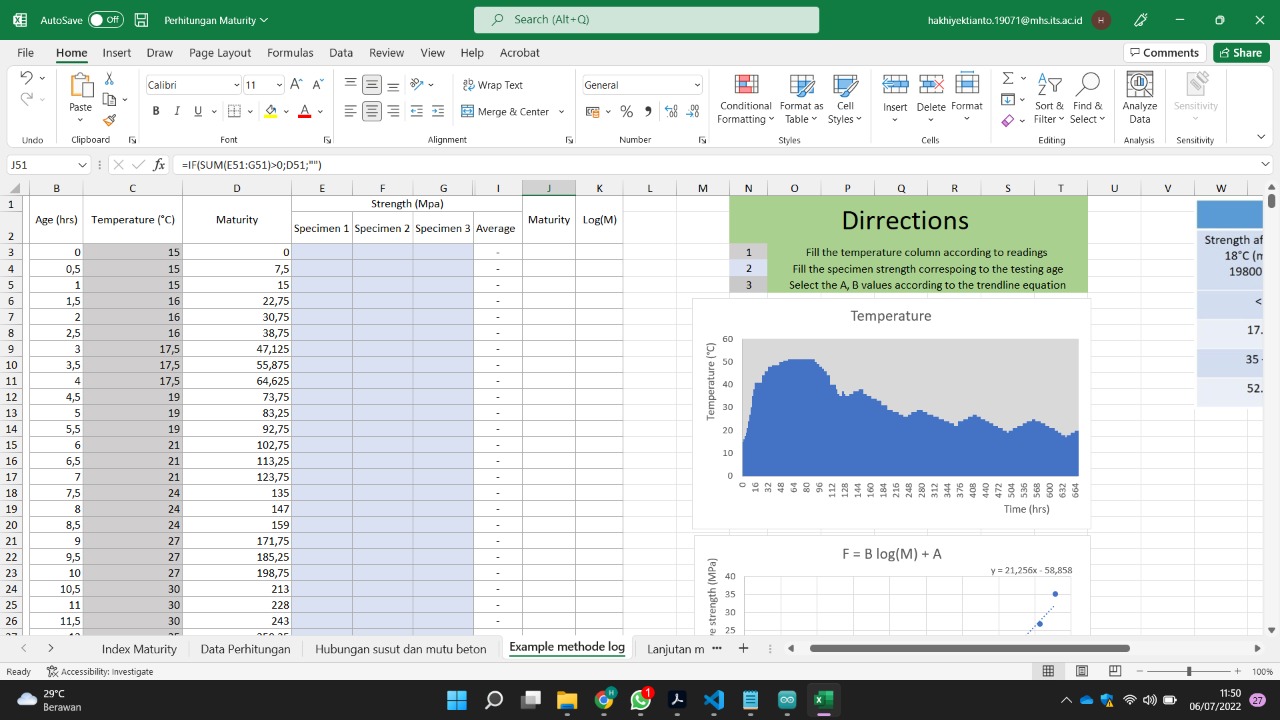
Dokumentasi/WhatsApp Image 2022-07-06 at 11.50.43.jpeg
