fariszuh/IoT-Concrete-Heat-Hidration/Dokumentasi/WhatsApp Image 2022-07-09 at 10.05.34.jpeg

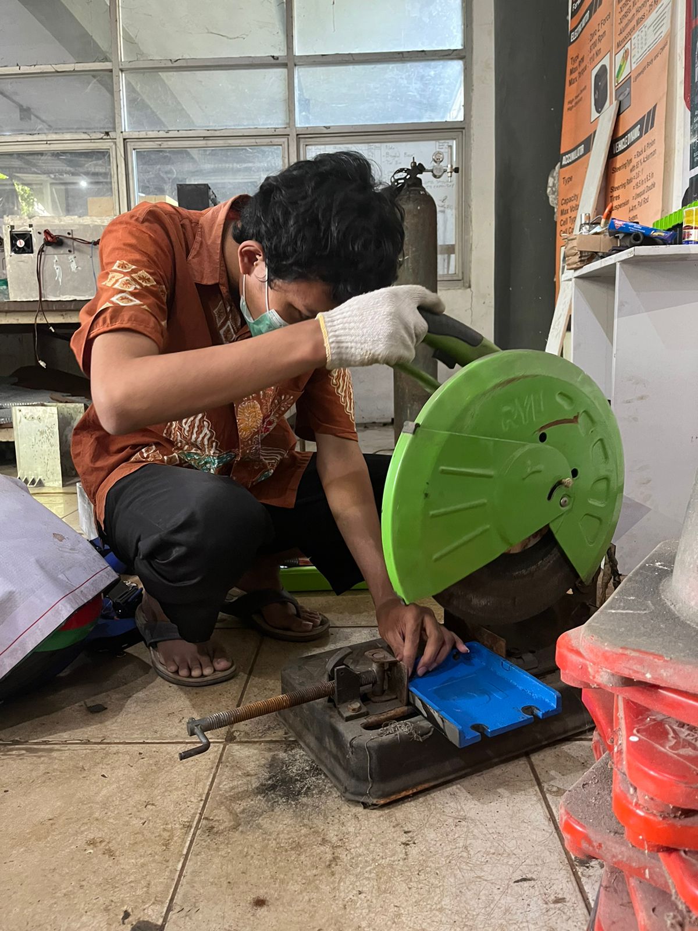
Dokumentasi/WhatsApp Image 2022-07-09 at 10.05.34.jpeg
