fariszuh/IoT-Concrete-Heat-Hidration/Dokumentasi/WhatsApp Image 2022-07-09 at 10.05.36.jpeg

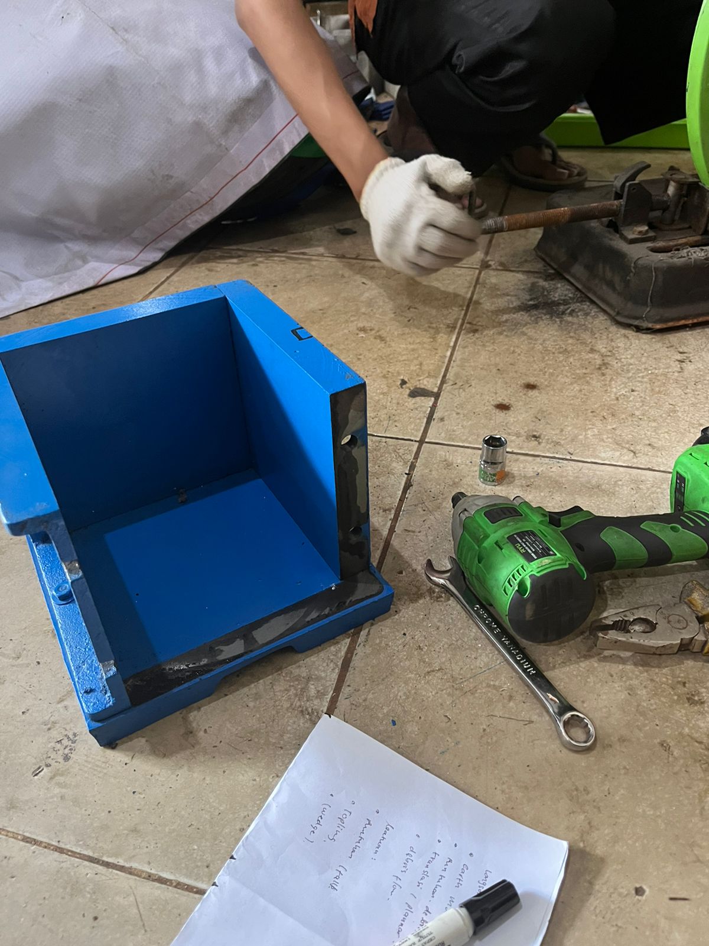
Dokumentasi/WhatsApp Image 2022-07-09 at 10.05.36.jpeg
