fariszuh/IoT-Concrete-Heat-Hidration/Dokumentasi/WhatsApp Image 2022-07-18 at 22.02.26.jpeg

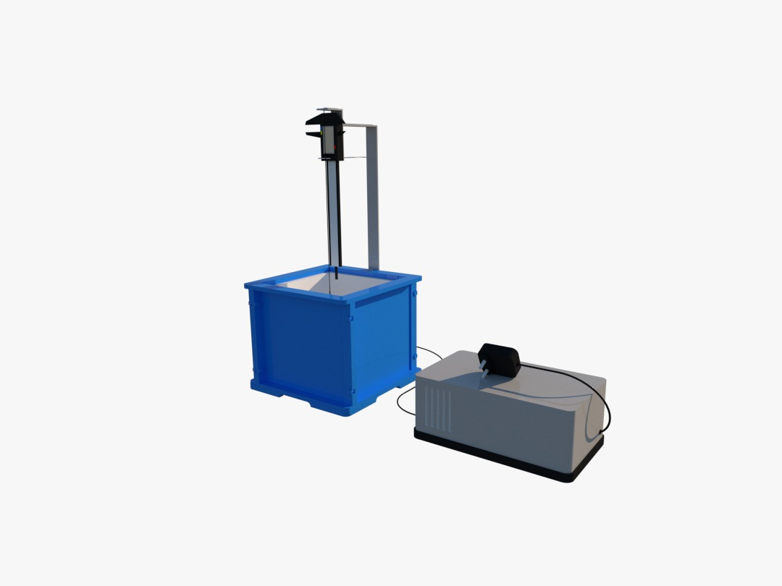
Dokumentasi/WhatsApp Image 2022-07-18 at 22.02.26.jpeg
