fariszuh/IoT-Concrete-Heat-Hidration/KALENDER KERJA/Timeline PKM Fase 2 ITS.jpeg

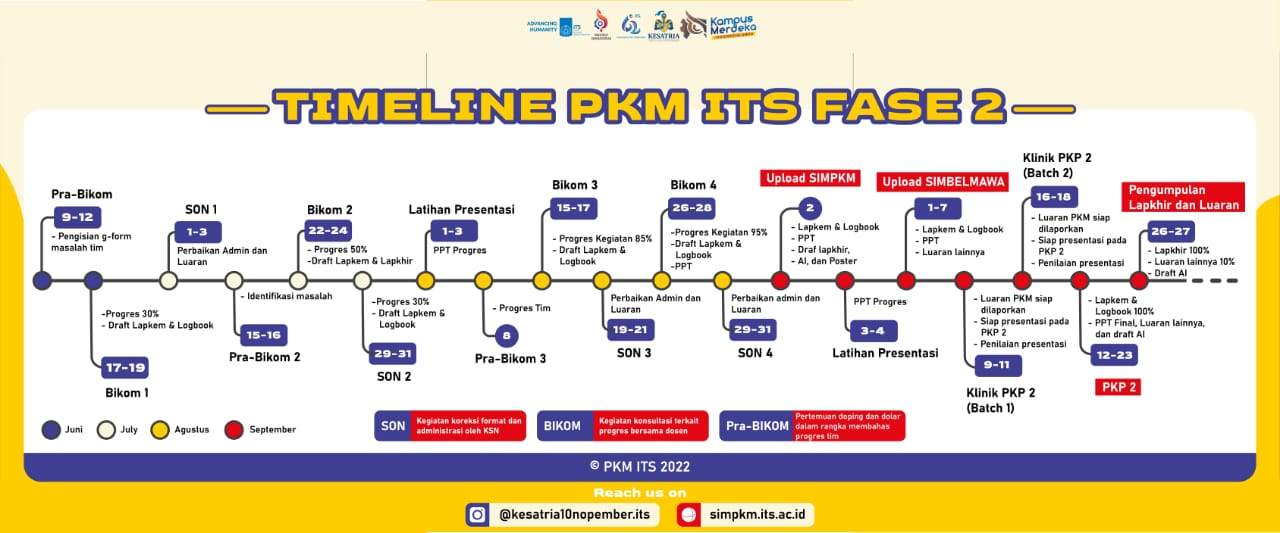
KALENDER KERJA/Timeline PKM Fase 2 ITS.jpeg
