fariszuh/IoT-Concrete-Heat-Hidration/Luaran PKM (Video dan Foto)/Album foto/2.jpg

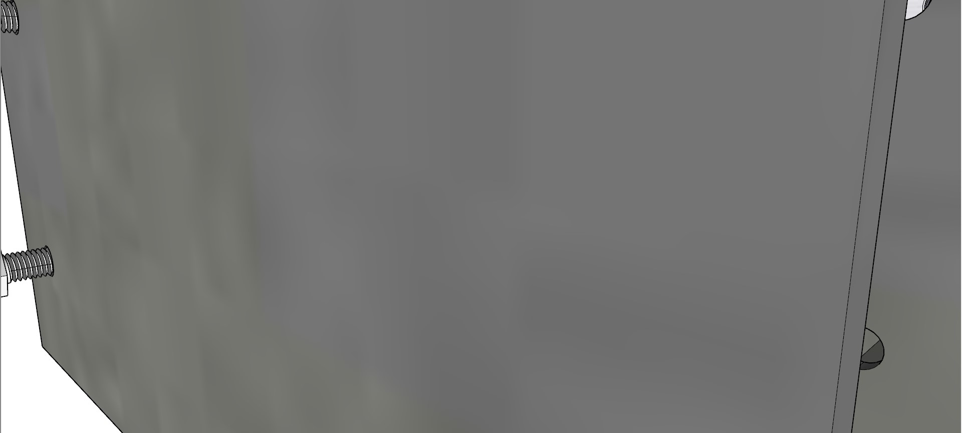
Luaran PKM (Video dan Foto)/Album foto/2.jpg
