fariszuh/IoT-Concrete-Heat-Hidration/Luaran PKM (Video dan Foto)/Album foto/3.jpg

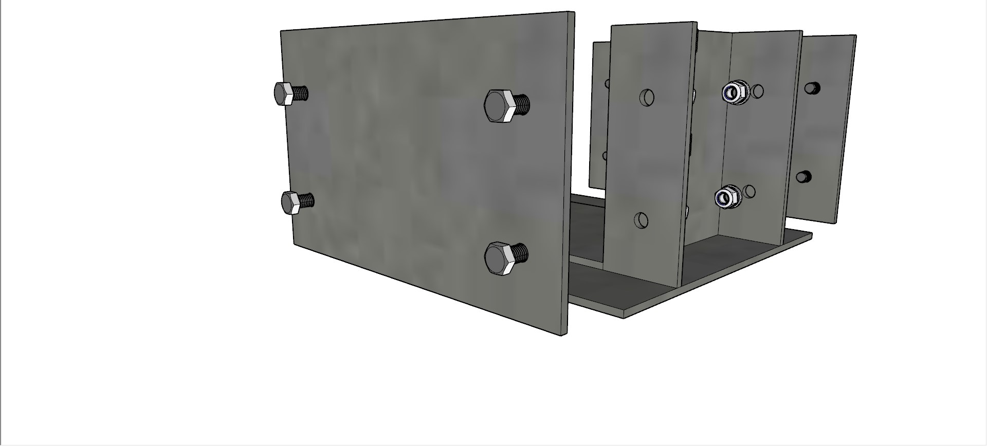
Luaran PKM (Video dan Foto)/Album foto/3.jpg
