fariszuh/IoT-Concrete-Heat-Hidration/Luaran PKM (Video dan Foto)/Album foto/4.jpg

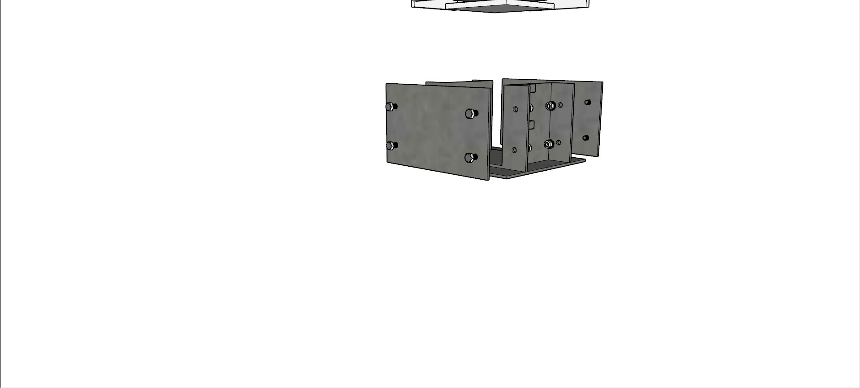
Luaran PKM (Video dan Foto)/Album foto/4.jpg
