fariszuh/IoT-Concrete-Heat-Hidration/Luaran PKM (Video dan Foto)/Album foto/11.jpg

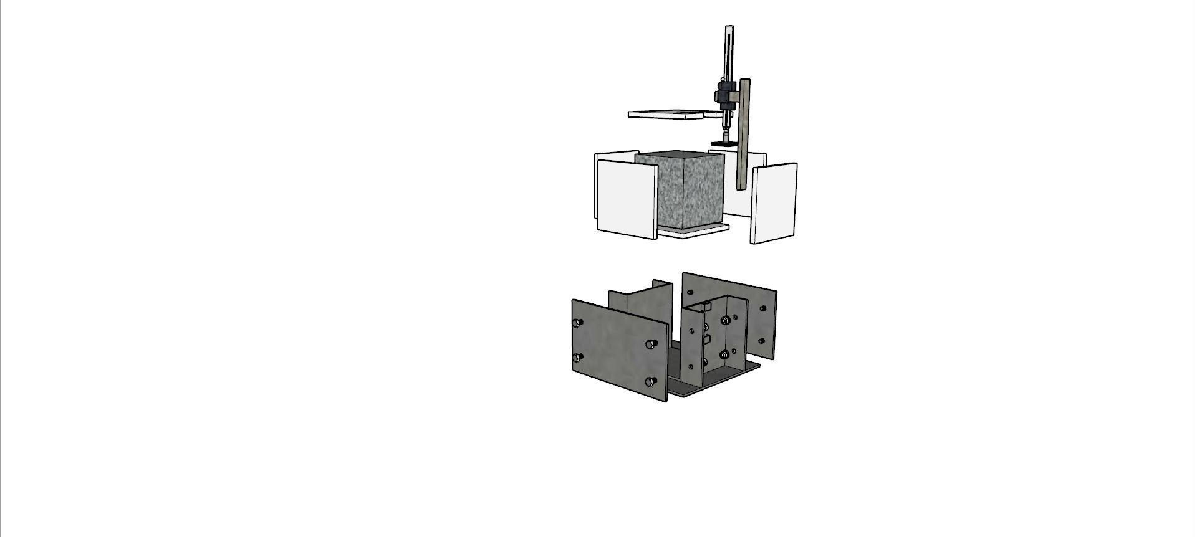
Luaran PKM (Video dan Foto)/Album foto/11.jpg
