fariszuh/IoT-Concrete-Heat-Hidration/Luaran PKM (Video dan Foto)/Album foto/14.jpg

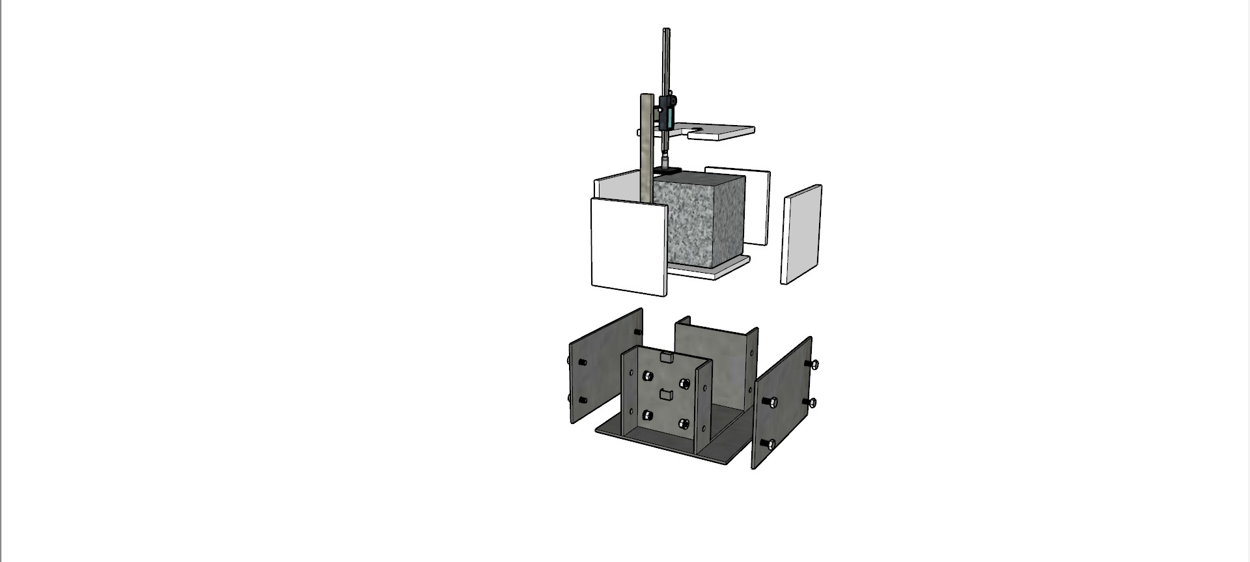
Luaran PKM (Video dan Foto)/Album foto/14.jpg
