fariszuh/IoT-Concrete-Heat-Hidration/Luaran PKM (Video dan Foto)/Album foto/20210918_203038.jpg

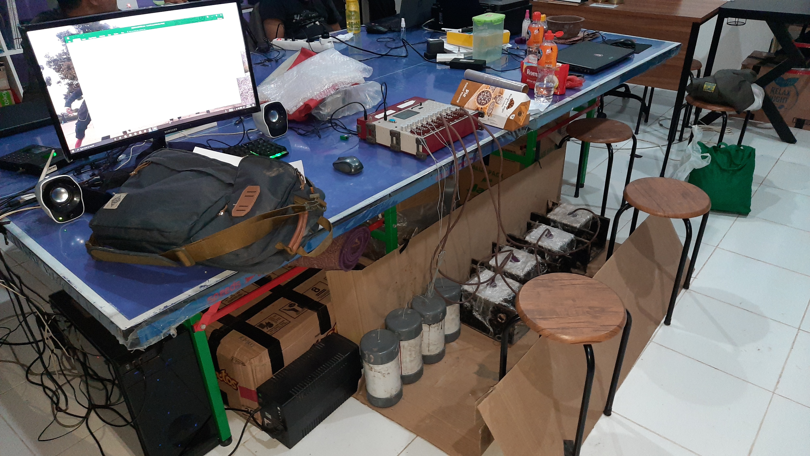
Luaran PKM (Video dan Foto)/Album foto/20210918_203038.jpg
