fariszuh/IoT-Concrete-Heat-Hidration/Luaran PKM (Video dan Foto)/Album foto/20220827_115939.jpg

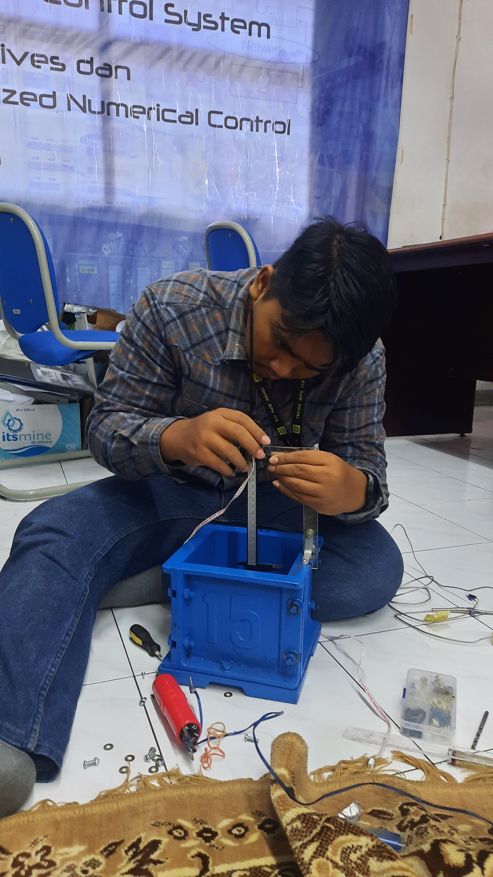
Luaran PKM (Video dan Foto)/Album foto/20220827_115939.jpg
