fariszuh/IoT-Concrete-Heat-Hidration/Luaran PKM (Video dan Foto)/Album foto/20220905_112701.jpg

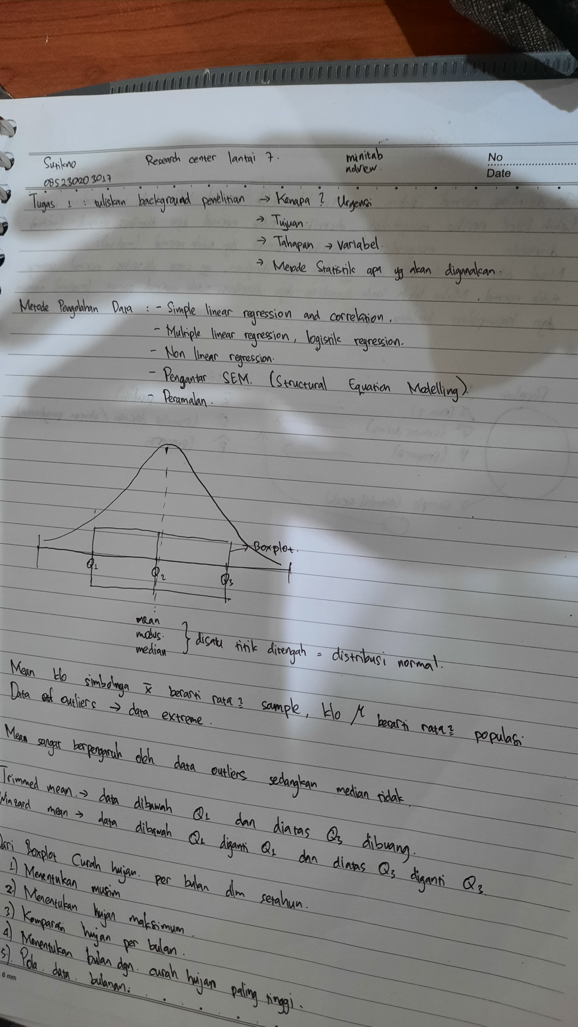
Luaran PKM (Video dan Foto)/Album foto/20220905_112701.jpg
