fariszuh/IoT-Concrete-Heat-Hidration/Luaran PKM (Video dan Foto)/Album foto/20220905_112703.jpg

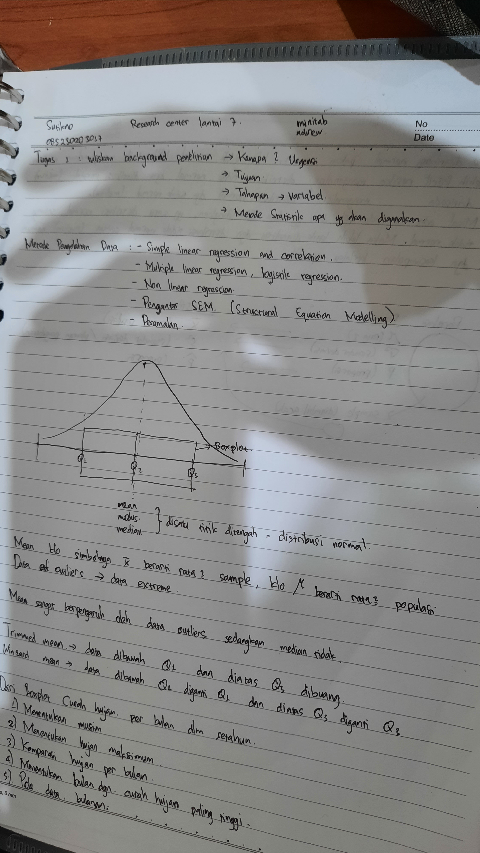
Luaran PKM (Video dan Foto)/Album foto/20220905_112703.jpg
