fariszuh/IoT-Concrete-Heat-Hidration/Luaran PKM (Video dan Foto)/Album foto/20220905_155105.jpg

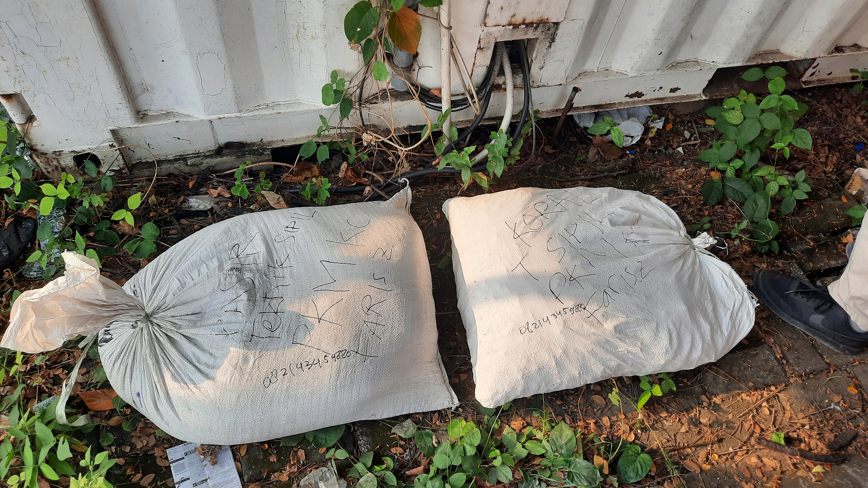
Luaran PKM (Video dan Foto)/Album foto/20220905_155105.jpg
