fariszuh/IoT-Concrete-Heat-Hidration/Luaran PKM (Video dan Foto)/Album foto/20220908_114701.jpg

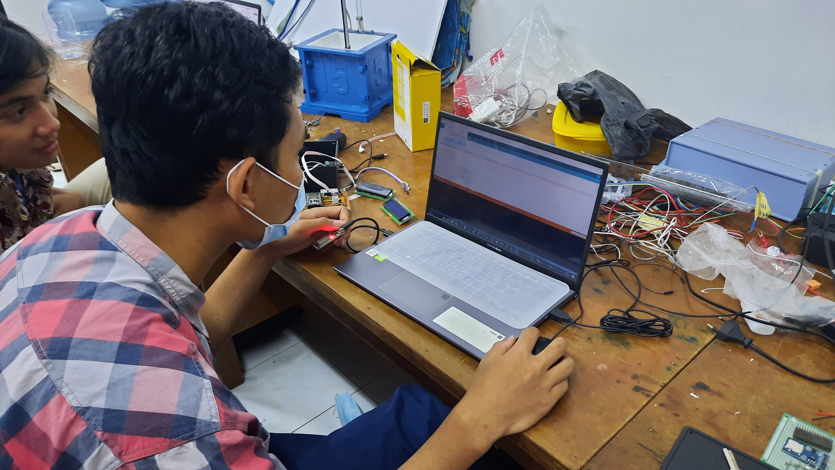
Luaran PKM (Video dan Foto)/Album foto/20220908_114701.jpg
