fariszuh/IoT-Concrete-Heat-Hidration/Luaran PKM (Video dan Foto)/Album foto/20220908_132144_Moment.jpg

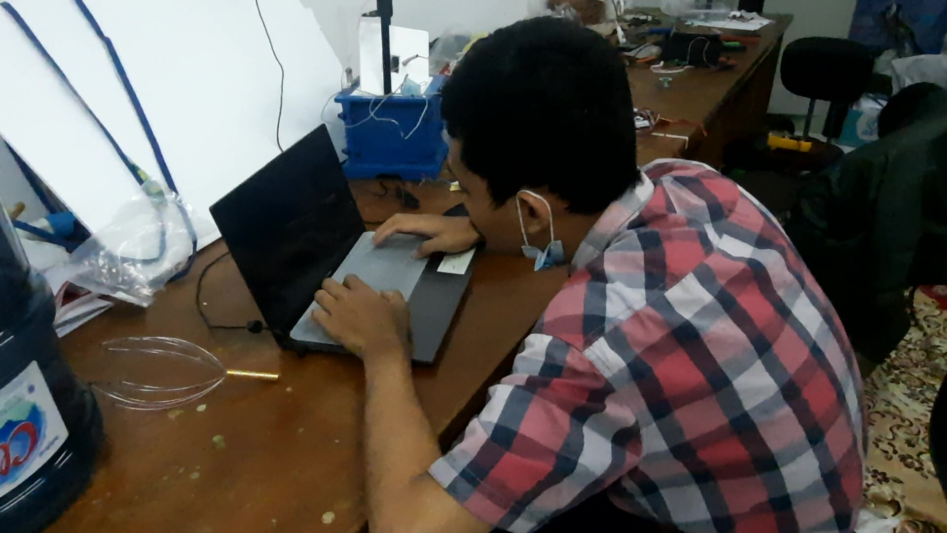
Luaran PKM (Video dan Foto)/Album foto/20220908_132144_Moment.jpg
