fariszuh/IoT-Concrete-Heat-Hidration/Luaran PKM (Video dan Foto)/Album foto/20220908_165541_Momenti.jpg

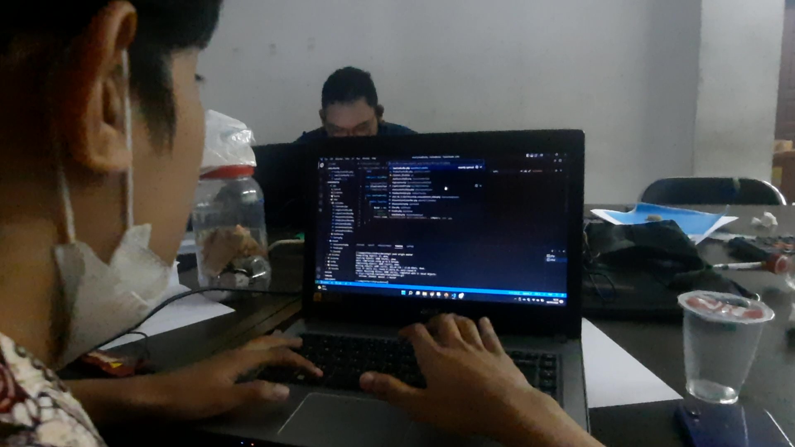
Luaran PKM (Video dan Foto)/Album foto/20220908_165541_Momenti.jpg
