fariszuh/IoT-Concrete-Heat-Hidration/Luaran PKM (Video dan Foto)/Album foto/cover1.jpg

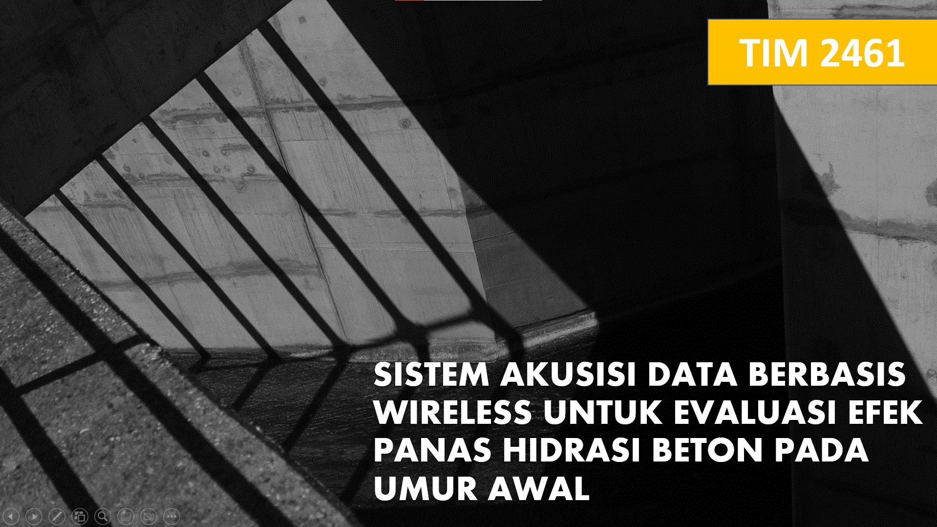
Luaran PKM (Video dan Foto)/Album foto/cover1.jpg
