fariszuh/IoT-Concrete-Heat-Hidration/Luaran PKM (Video dan Foto)/Album foto/Cuplikan layar 2022-09-08 184816.jpg

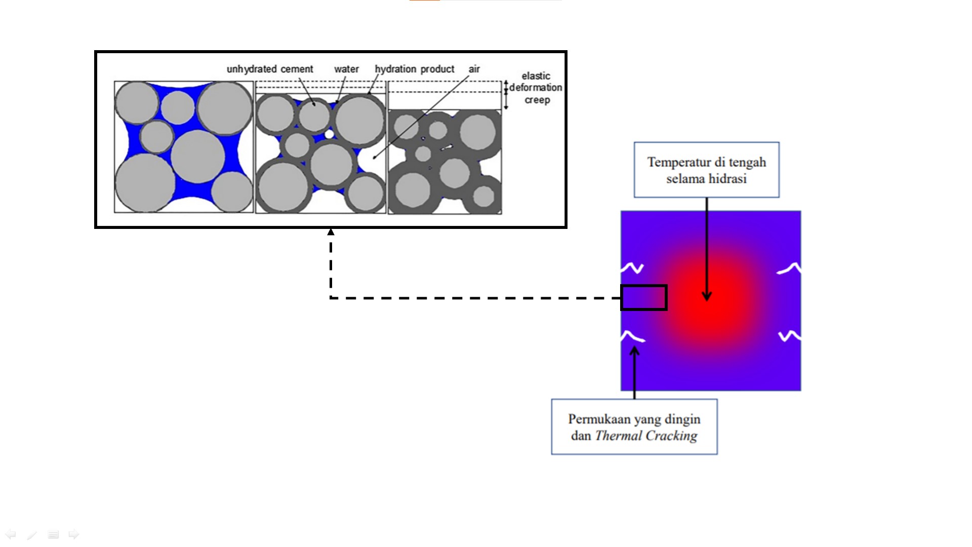
Luaran PKM (Video dan Foto)/Album foto/Cuplikan layar 2022-09-08 184816.jpg
