fariszuh/IoT-Concrete-Heat-Hidration/Luaran PKM (Video dan Foto)/Album foto/grafik.jpg

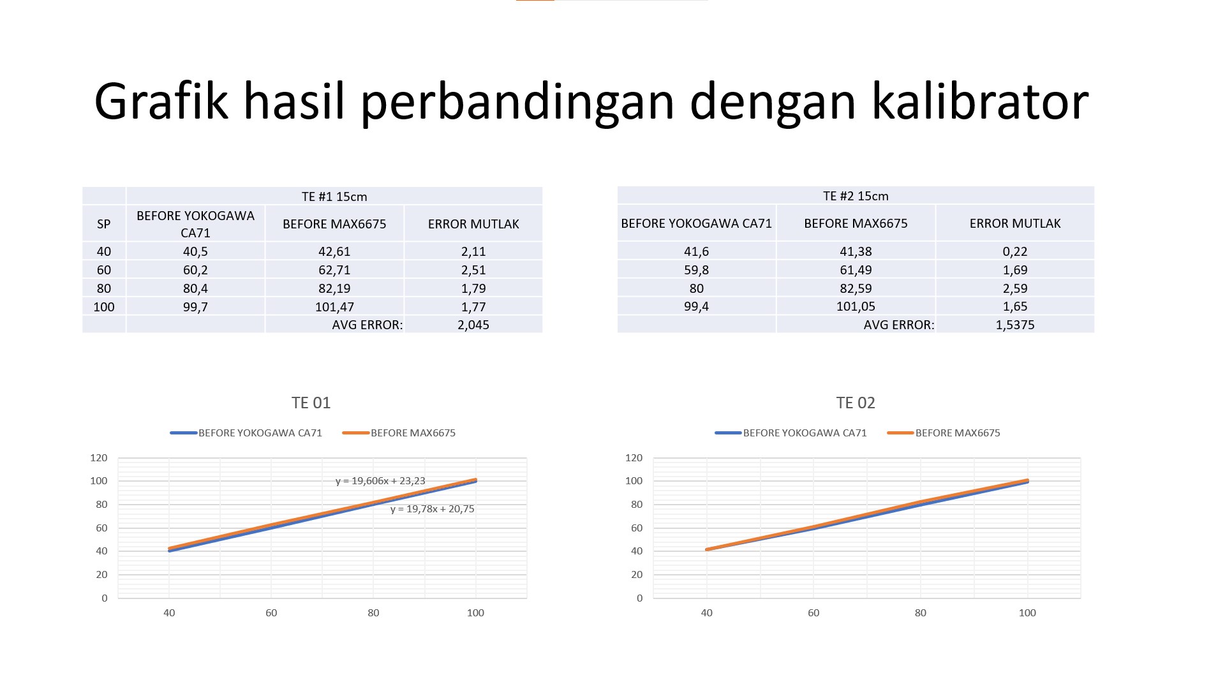
Luaran PKM (Video dan Foto)/Album foto/grafik.jpg
