fariszuh/IoT-Concrete-Heat-Hidration/Luaran PKM (Video dan Foto)/Album foto/hasil1.jpg

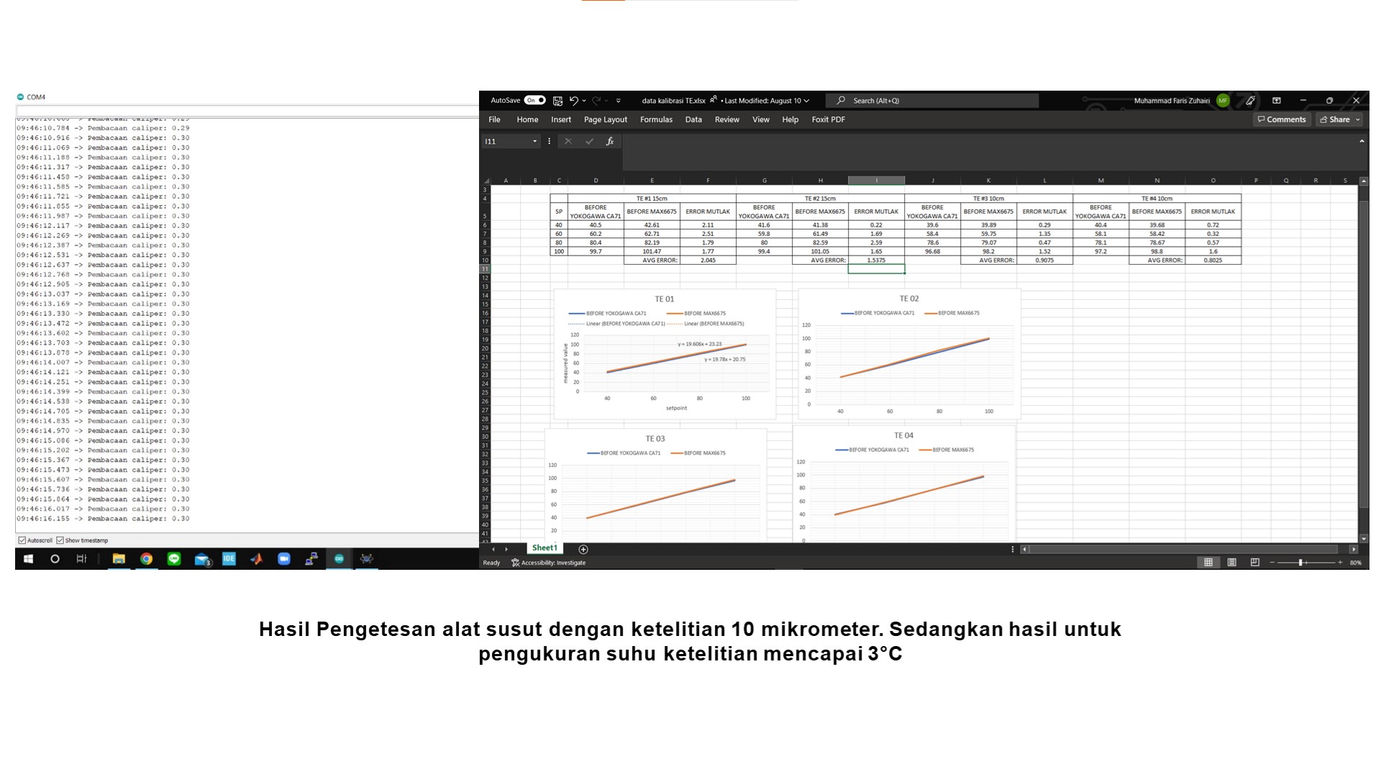
Luaran PKM (Video dan Foto)/Album foto/hasil1.jpg
