fariszuh/IoT-Concrete-Heat-Hidration/Luaran PKM (Video dan Foto)/Album foto/maturity.jpg

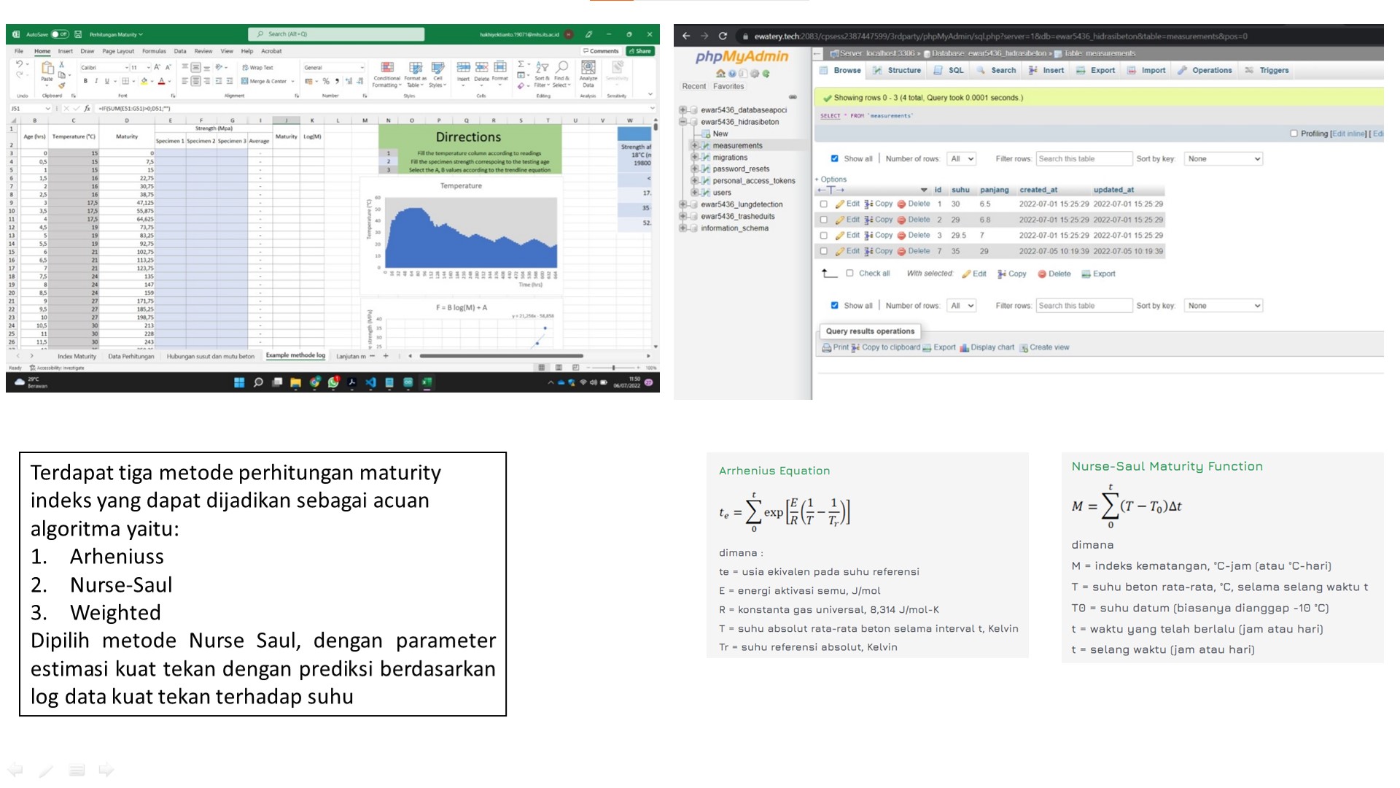
Luaran PKM (Video dan Foto)/Album foto/maturity.jpg
