fariszuh/IoT-Concrete-Heat-Hidration/Luaran PKM (Video dan Foto)/Album foto/progress.jpg

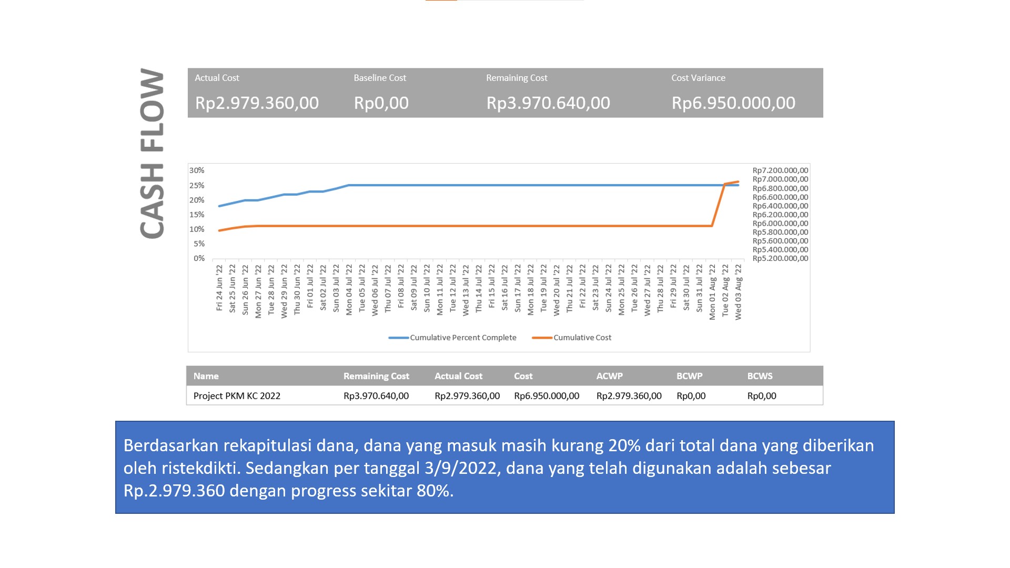
Luaran PKM (Video dan Foto)/Album foto/progress.jpg
