fariszuh/IoT-Concrete-Heat-Hidration/Luaran PKM (Video dan Foto)/Album foto/ss.jpg

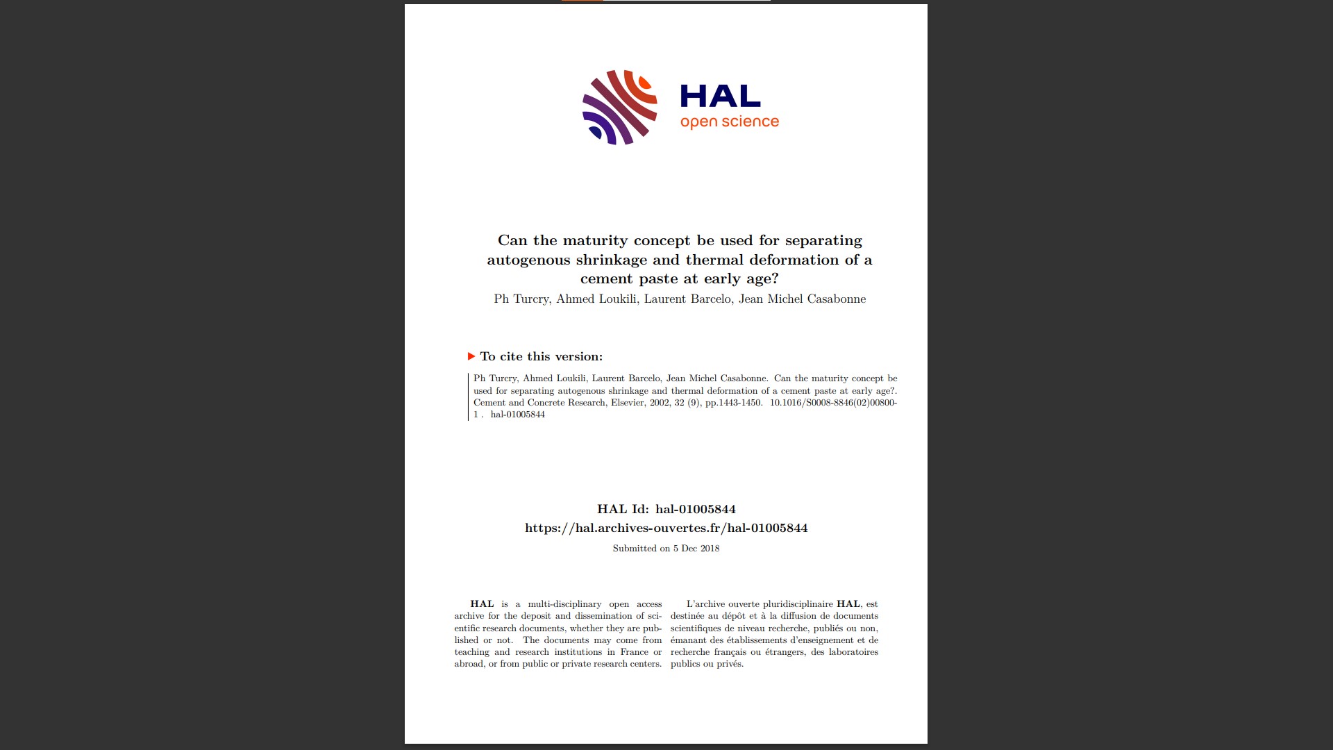
Luaran PKM (Video dan Foto)/Album foto/ss.jpg
