fariszuh/IoT-Concrete-Heat-Hidration/Luaran PKM (Video dan Foto)/Album foto/trim2_Moment.jpg

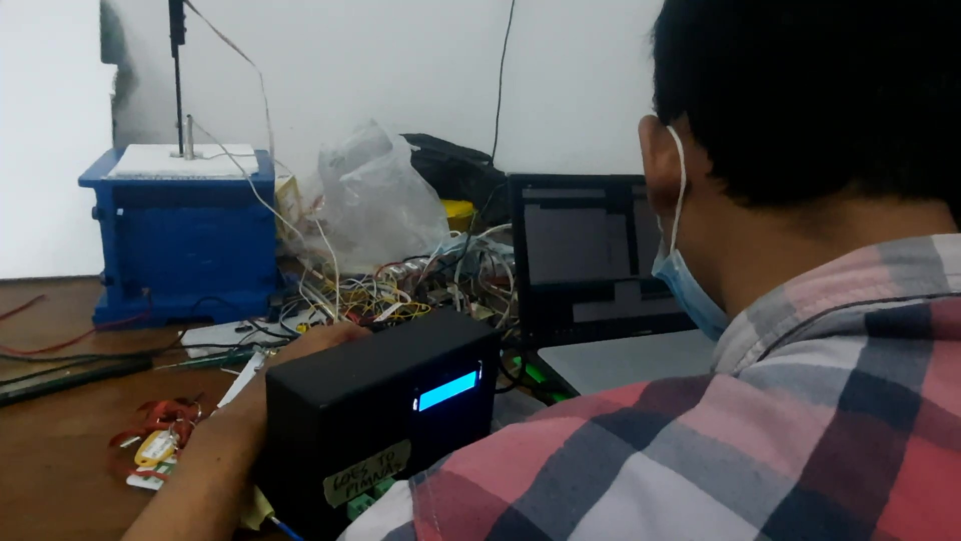
Luaran PKM (Video dan Foto)/Album foto/trim2_Moment.jpg
