fariszuh/IoT-Concrete-Heat-Hidration/Luaran PKM (Video dan Foto)/Album foto/WhatsApp Image 2022-09-02 at 19.49.33.jpeg

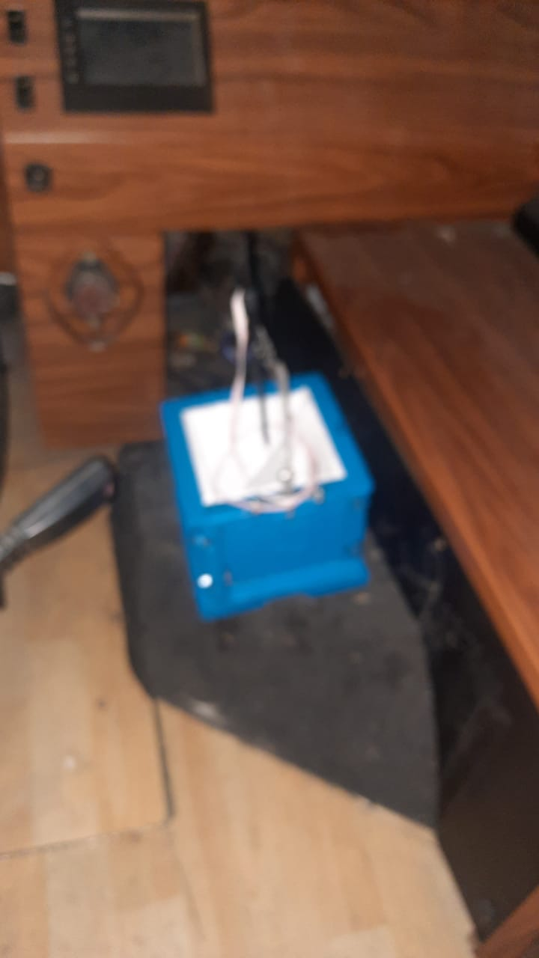
Luaran PKM (Video dan Foto)/Album foto/WhatsApp Image 2022-09-02 at 19.49.33.jpeg
