fariszuh/IoT-Concrete-Heat-Hidration/Luaran PKM (Video dan Foto)/Album foto/WhatsApp Image 2022-09-07 at 17.58.14.jpeg

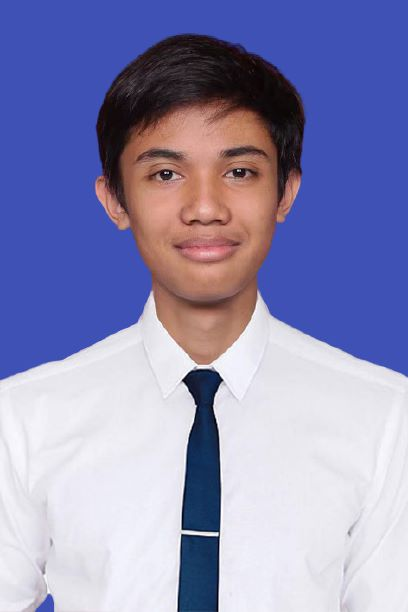
Luaran PKM (Video dan Foto)/Album foto/WhatsApp Image 2022-09-07 at 17.58.14.jpeg
