fariszuh/IoT-Concrete-Heat-Hidration/Luaran PKM (Video dan Foto)/Album foto/WhatsApp Image 2022-09-08 at 21.05.03.jpeg

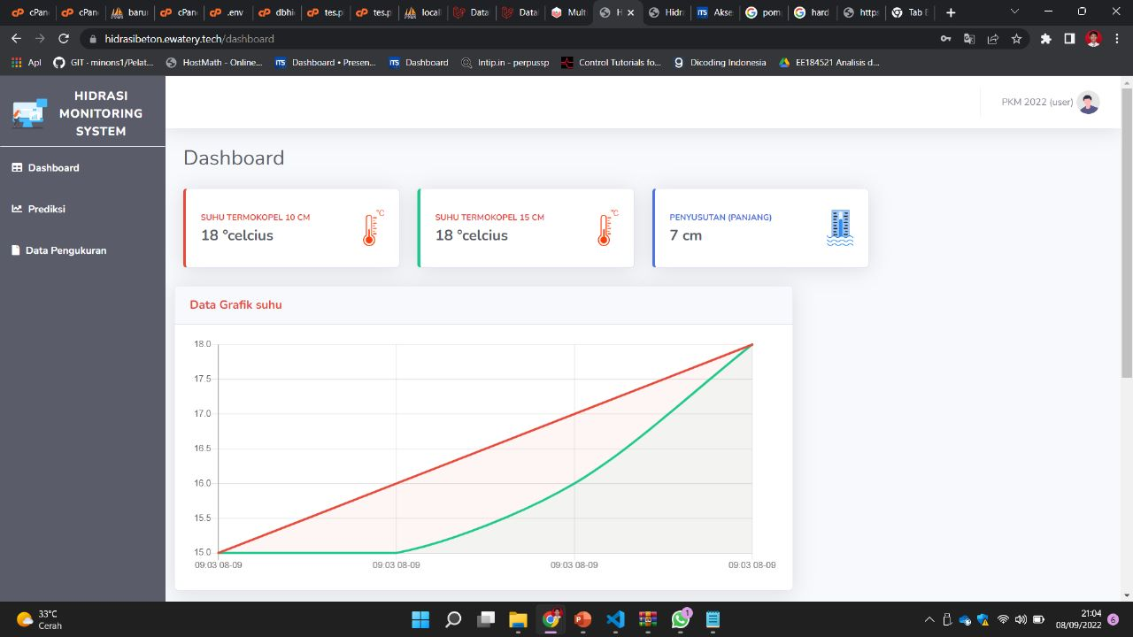
Luaran PKM (Video dan Foto)/Album foto/WhatsApp Image 2022-09-08 at 21.05.03.jpeg
