fariszuh/IoT-Concrete-Heat-Hidration/Luaran PKM (Video dan Foto)/Album foto/WhatsApp Image 2022-09-26 at 10.05.59.jpeg

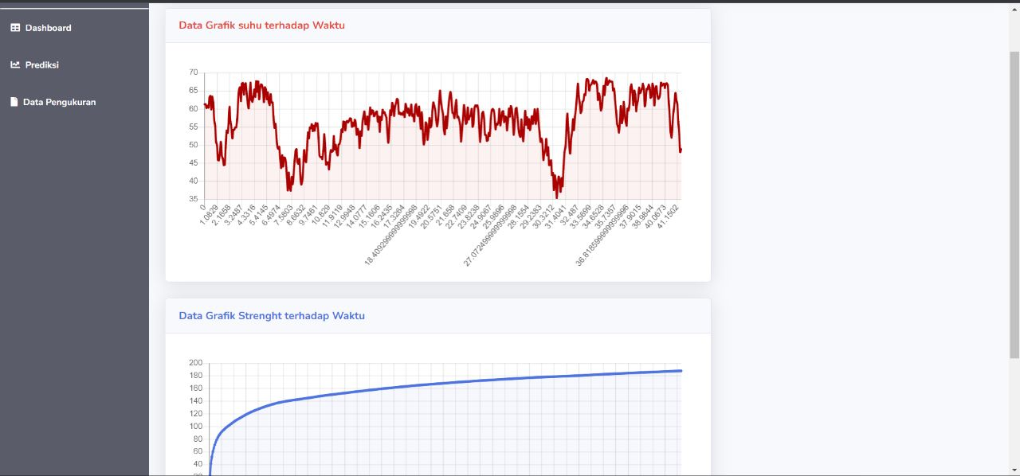
Luaran PKM (Video dan Foto)/Album foto/WhatsApp Image 2022-09-26 at 10.05.59.jpeg
