fariszuh/IoT-Concrete-Heat-Hidration/NOTA/7599.jpg

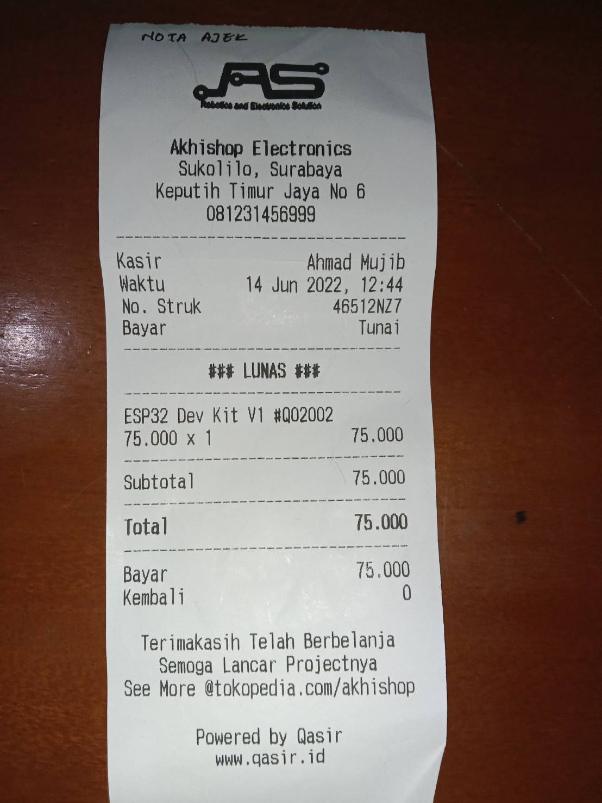
NOTA/7599.jpg
