fariszuh/IoT-Concrete-Heat-Hidration/NOTA/7600.jpg

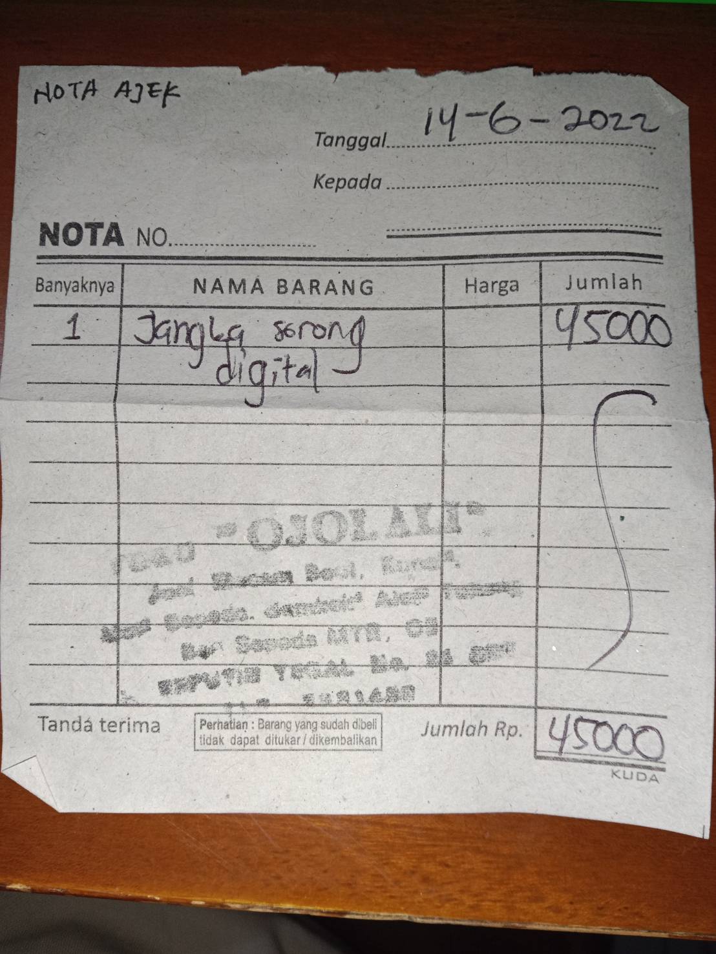
NOTA/7600.jpg
