fariszuh/IoT-Concrete-Heat-Hidration/NOTA/8167.jpg

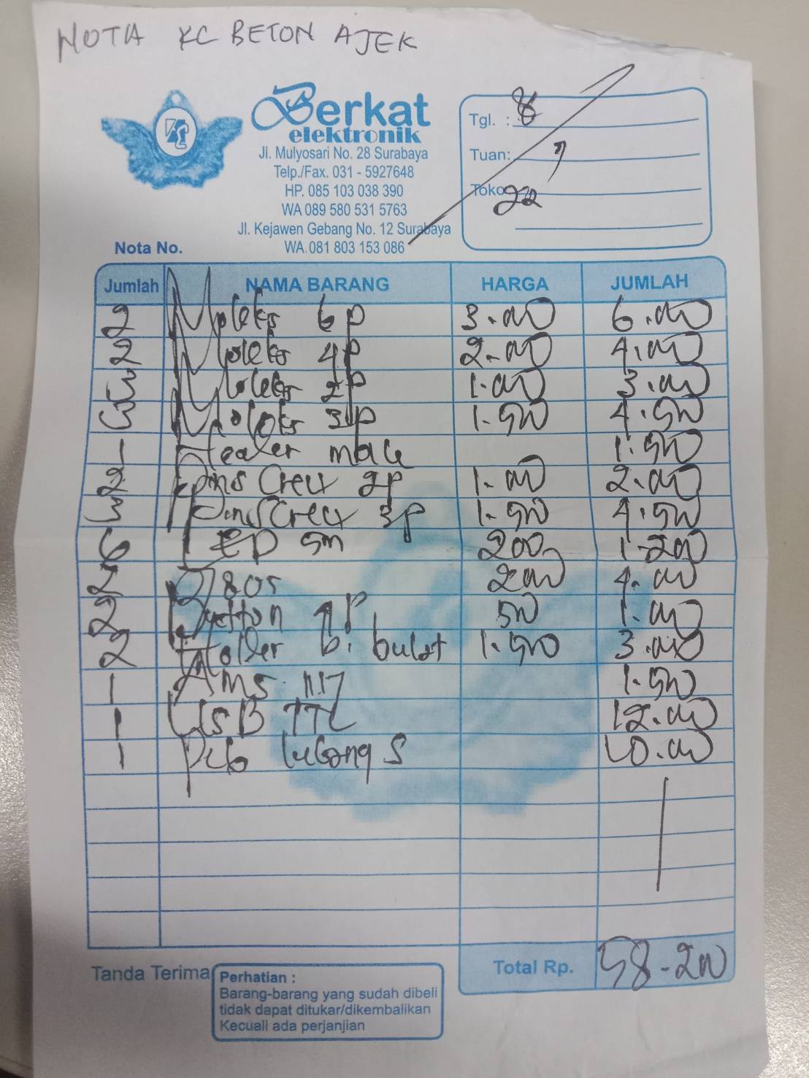
NOTA/8167.jpg
