fariszuh/IoT-Concrete-Heat-Hidration/NOTA/8168.jpg

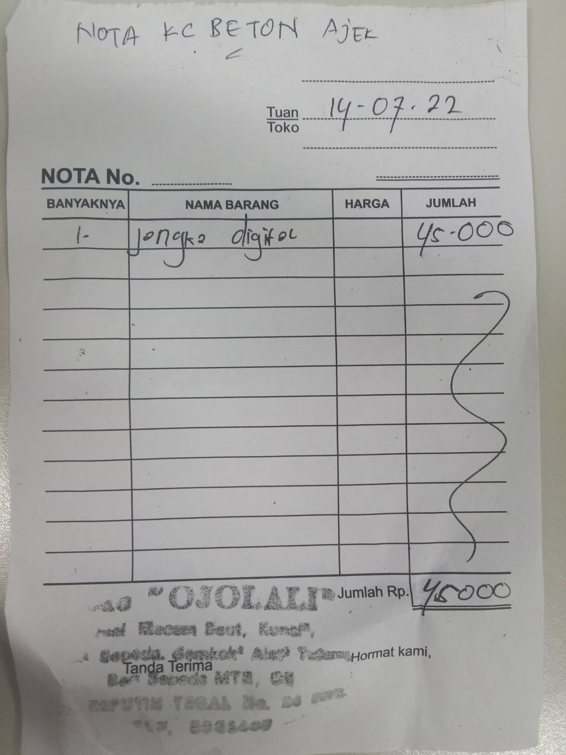
NOTA/8168.jpg
