fariszuh/IoT-Concrete-Heat-Hidration/NOTA/8169.jpg

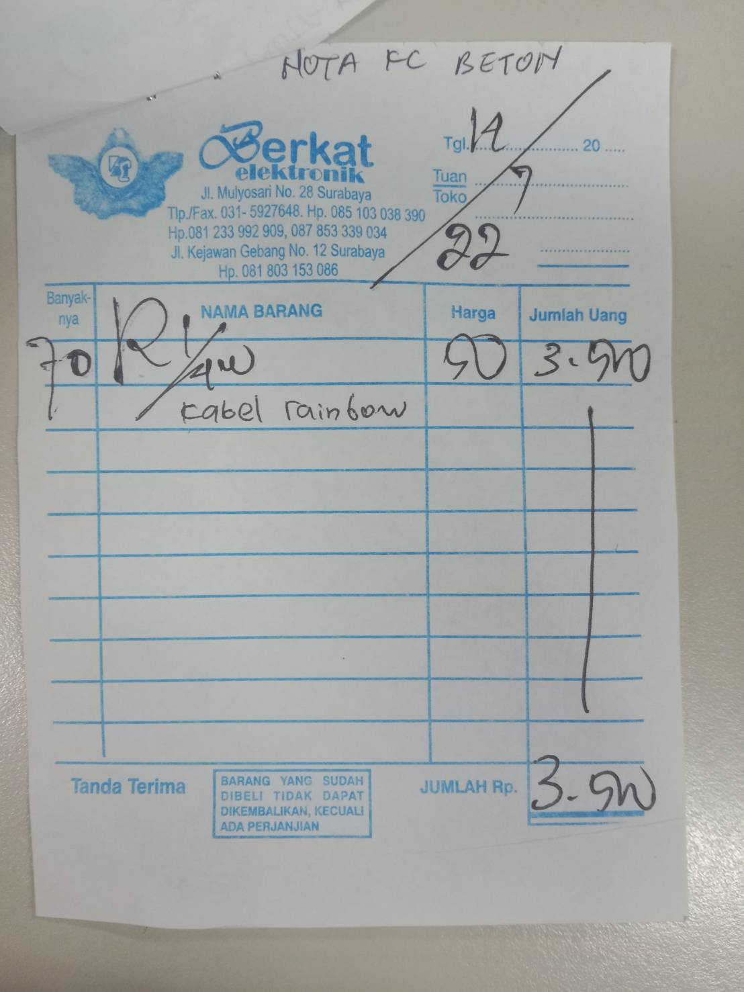
NOTA/8169.jpg
