fariszuh/IoT-Concrete-Heat-Hidration/NOTA/8170.jpg

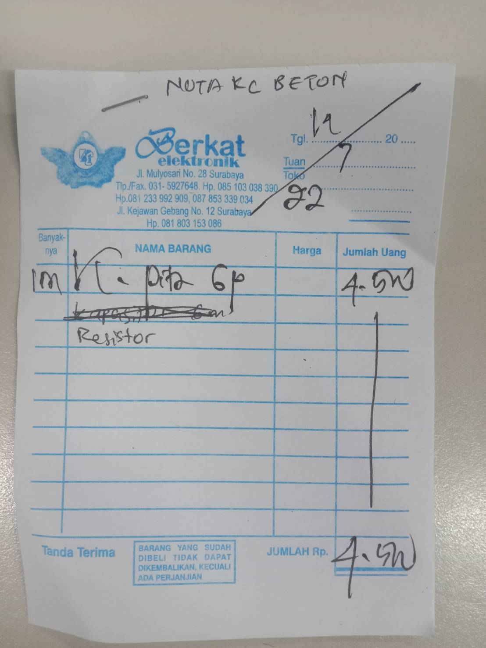
NOTA/8170.jpg
