fariszuh/IoT-Concrete-Heat-Hidration/NOTA/8171.jpg

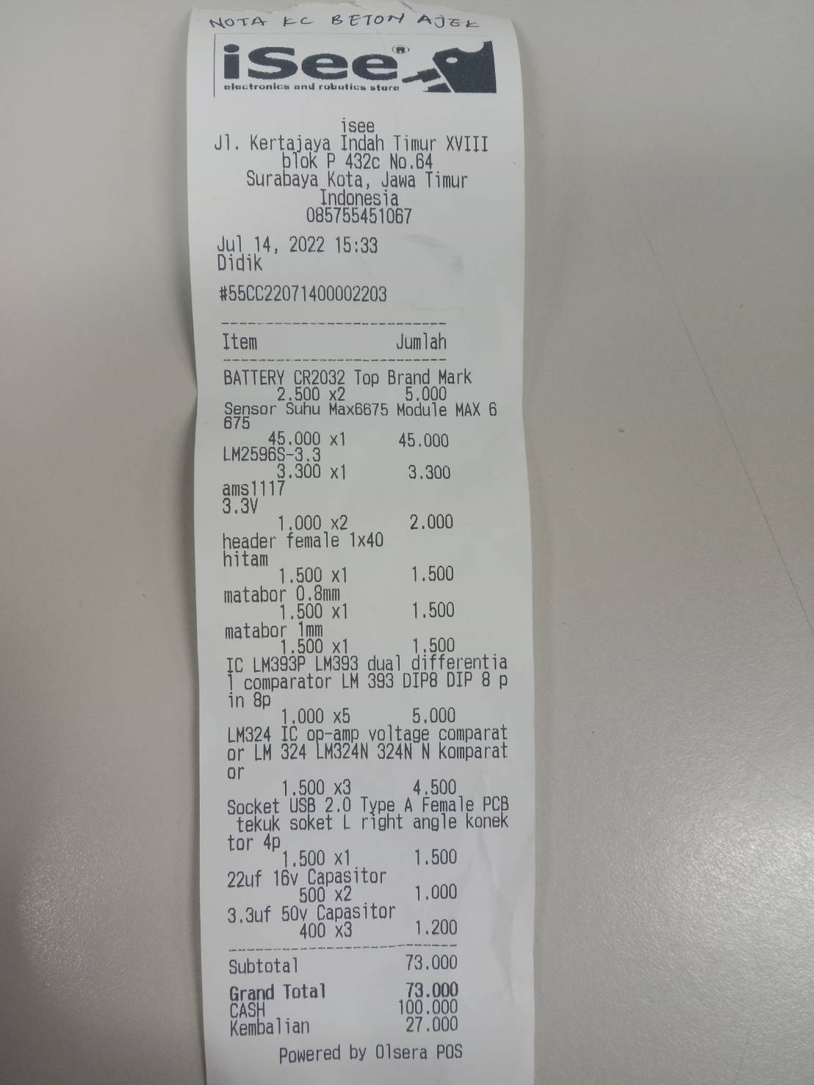
NOTA/8171.jpg
