fariszuh/IoT-Concrete-Heat-Hidration/NOTA/8172.jpg

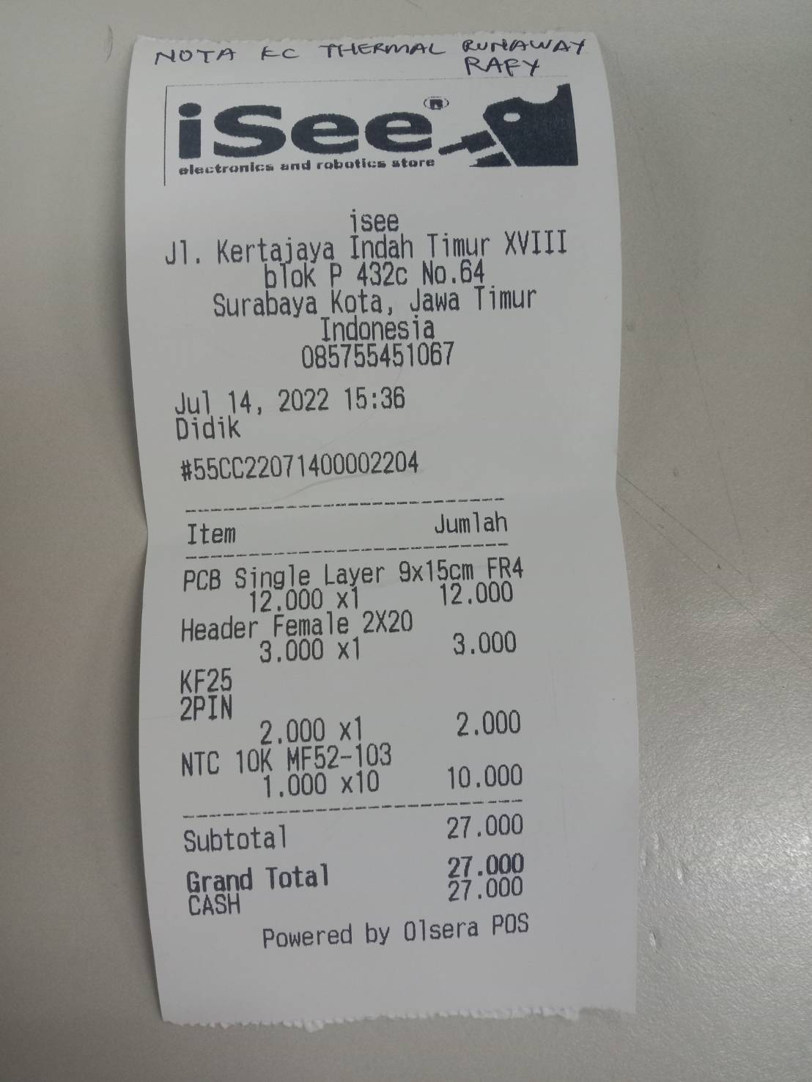
NOTA/8172.jpg
