fariszuh/IoT-Concrete-Heat-Hidration/NOTA/8186.jpg

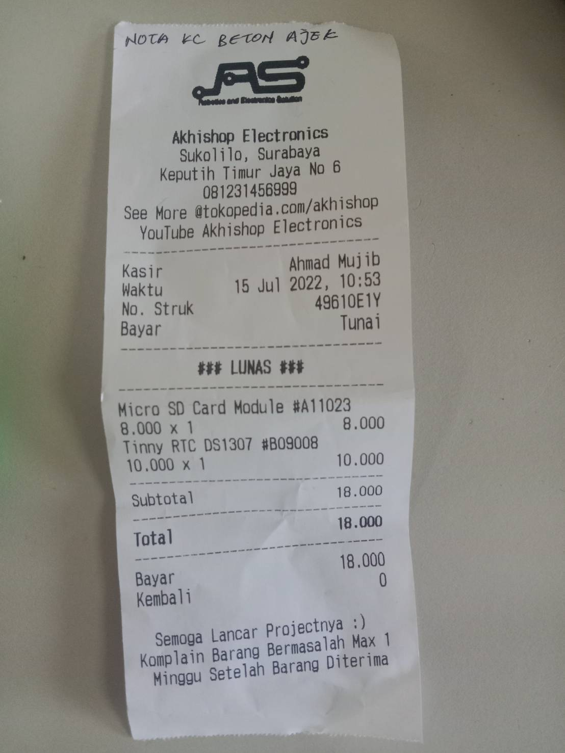
NOTA/8186.jpg
