fariszuh/IoT-Concrete-Heat-Hidration/NOTA/NOTA WEMOS D1 MINI SD CARD SHIELD.jpeg

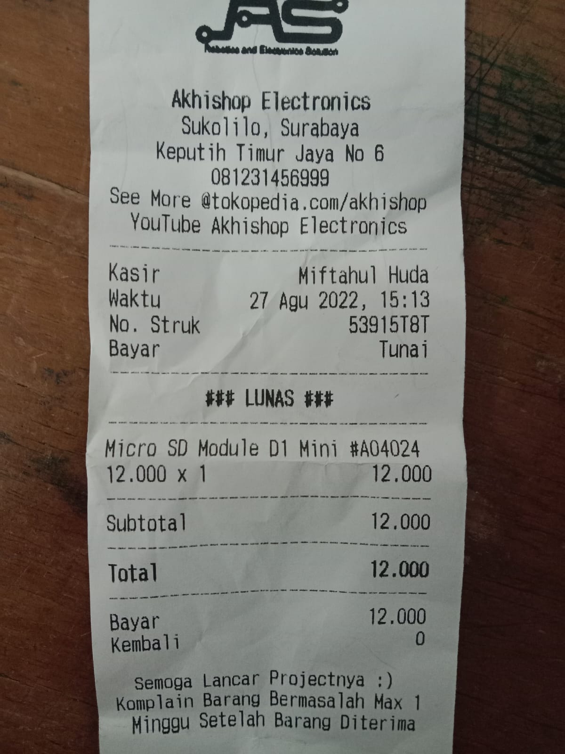
NOTA/NOTA WEMOS D1 MINI SD CARD SHIELD.jpeg
