fariszuh/IoT-Concrete-Heat-Hidration/PPT PKP2/PKP2 2022-09-14 214033.jpg

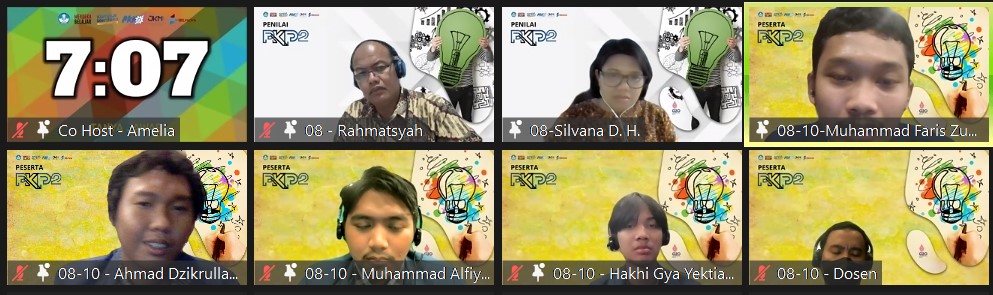
PPT PKP2/PKP2 2022-09-14 214033.jpg
