fariszuh/IoT-Concrete-Heat-Hidration/PPT PKP2/PKP2 2022-09-14 at 13.55.12.jpeg

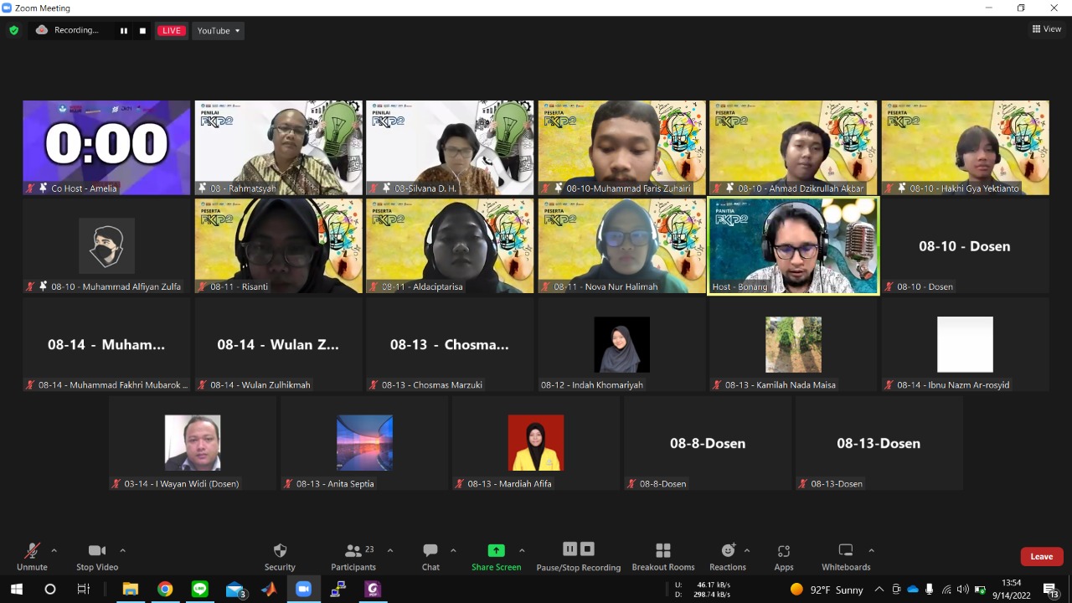
PPT PKP2/PKP2 2022-09-14 at 13.55.12.jpeg
