fariszuh/IoT-Concrete-Heat-Hidration/PPT PKP2/VBG.jpeg

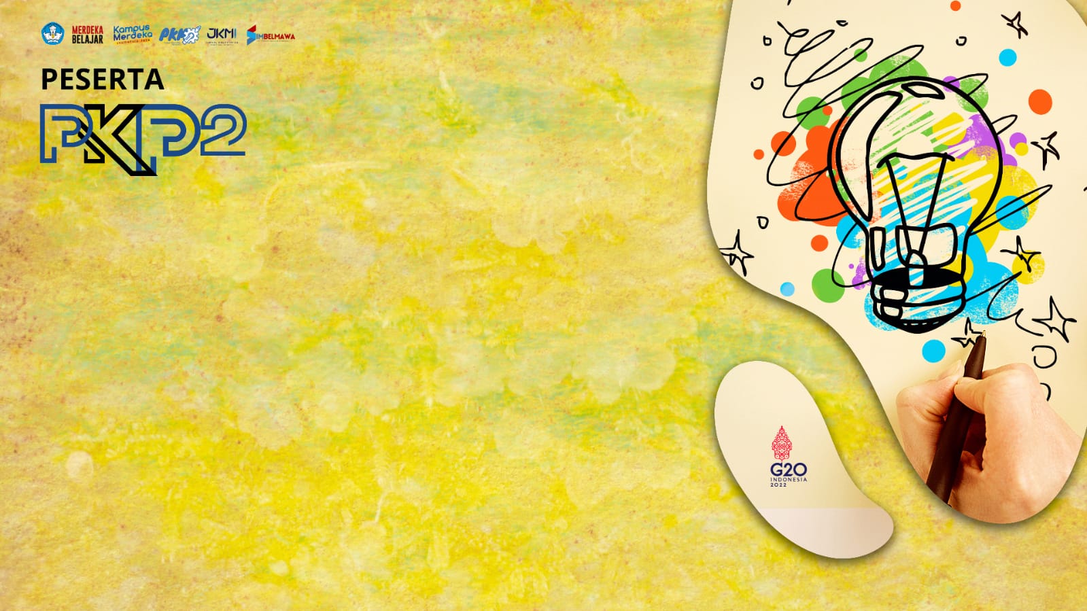
PPT PKP2/VBG.jpeg
