fariszuh/IoT-Concrete-Heat-Hidration/Proposal PKM KC/Biodata/WhatsApp Image 2022-02-13 at 20.30.27.jpeg

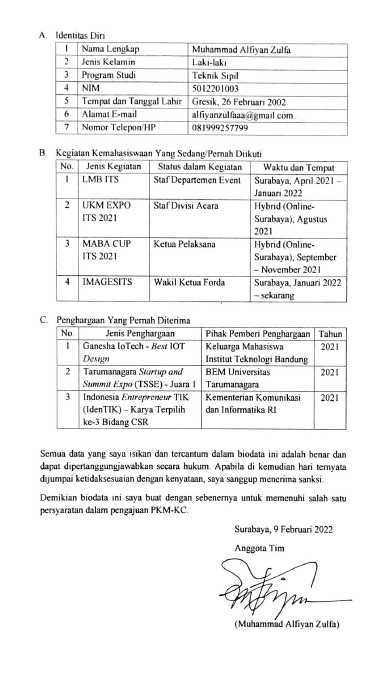
Proposal PKM KC/Biodata/WhatsApp Image 2022-02-13 at 20.30.27.jpeg
