fariszuh/IoT-Concrete-Heat-Hidration/Proposal PKM KC/Biodata/WhatsApp Image 2022-03-21 at 21.09.23.jpeg

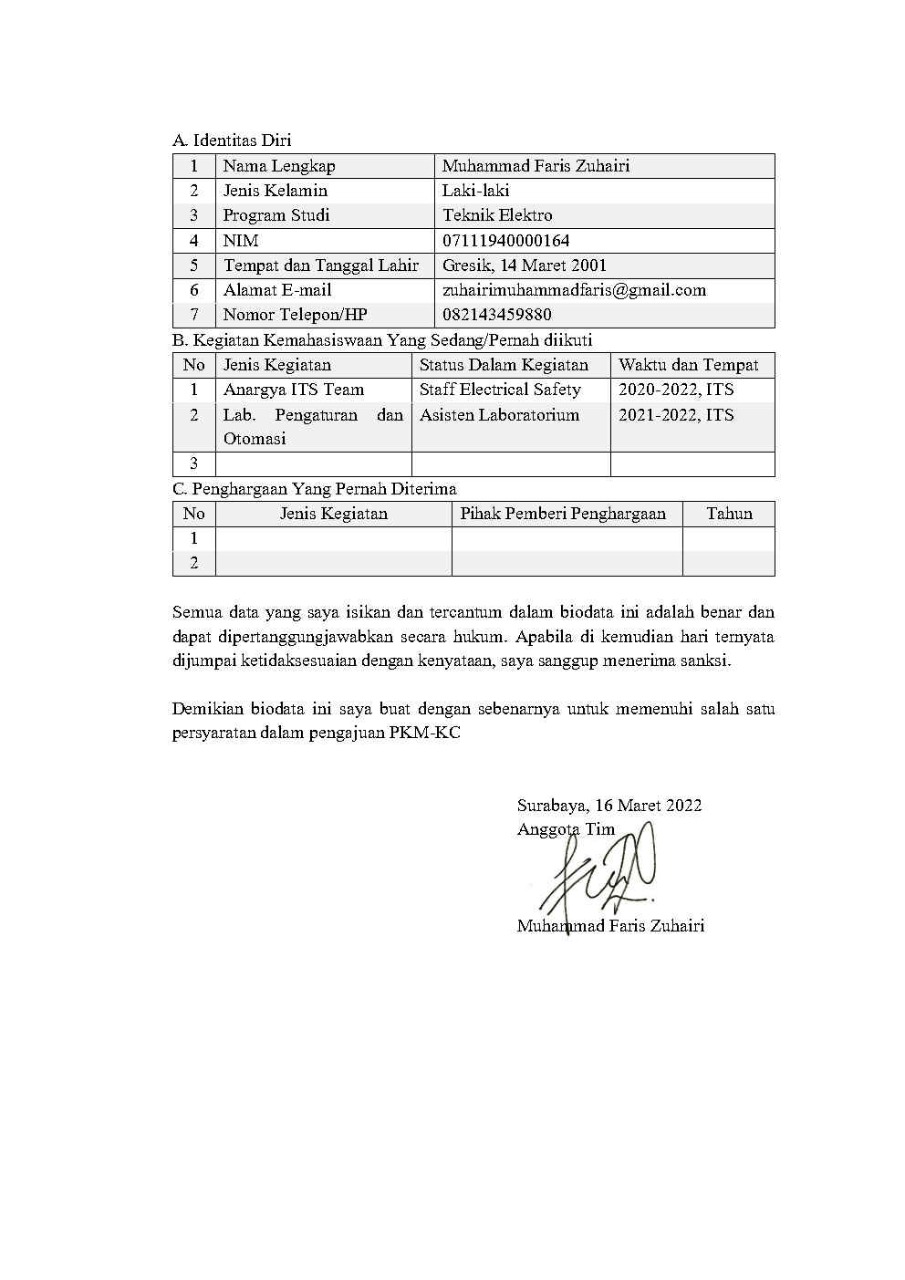
Proposal PKM KC/Biodata/WhatsApp Image 2022-03-21 at 21.09.23.jpeg
