fariszuh/IoT-Concrete-Heat-Hidration/Prototype/Foto thermocouple type T.jpeg

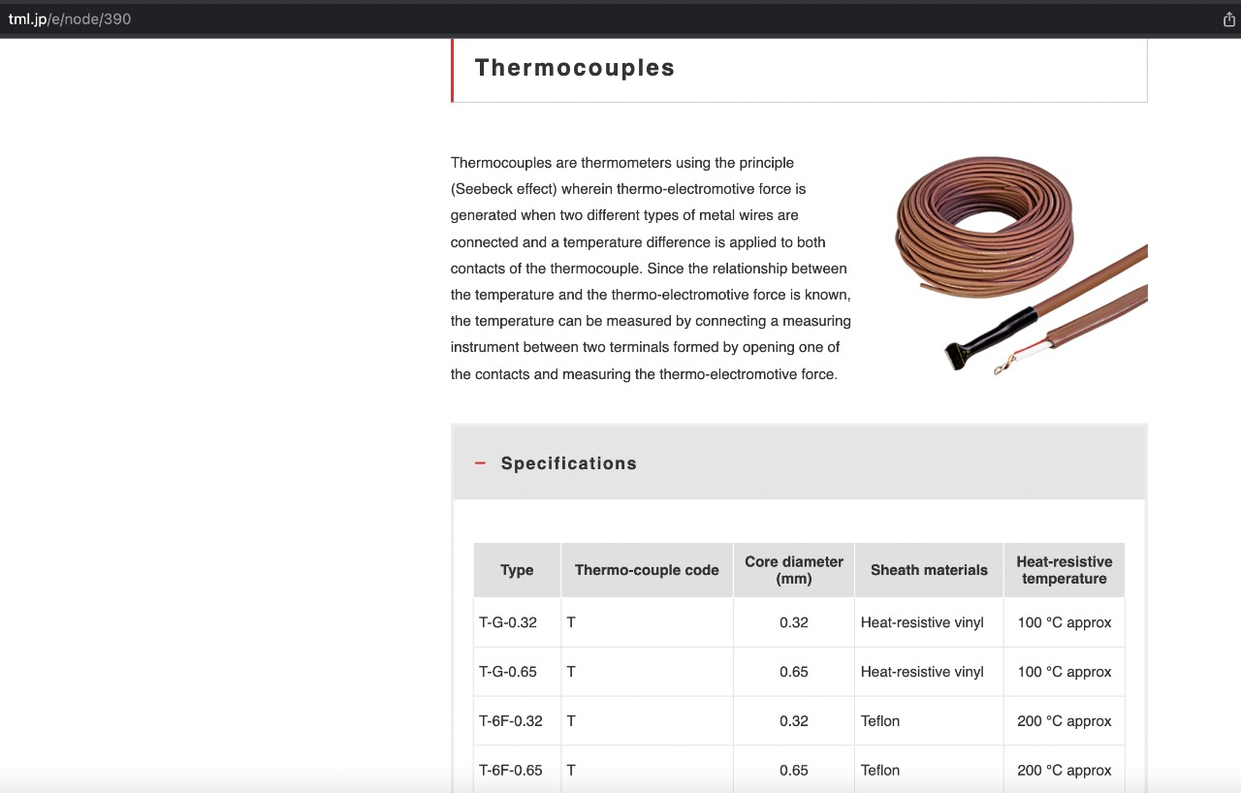
Prototype/Foto thermocouple type T.jpeg
