fariszuh/IoT-Concrete-Heat-Hidration/Prototype/Prototype 2018/Bird Eye 1.png

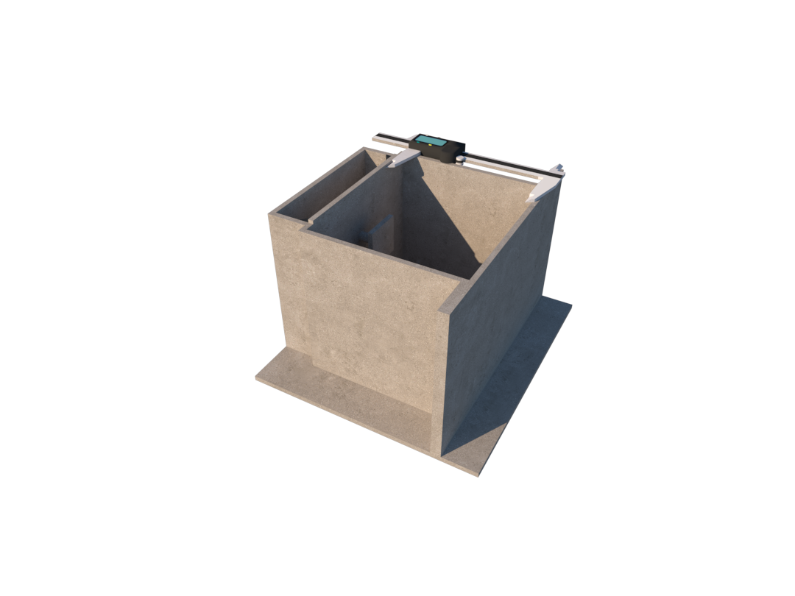
Prototype/Prototype 2018/Bird Eye 1.png
