fariszuh/IoT-Concrete-Heat-Hidration/Prototype/Prototype 2018/Bird Eye 3.png

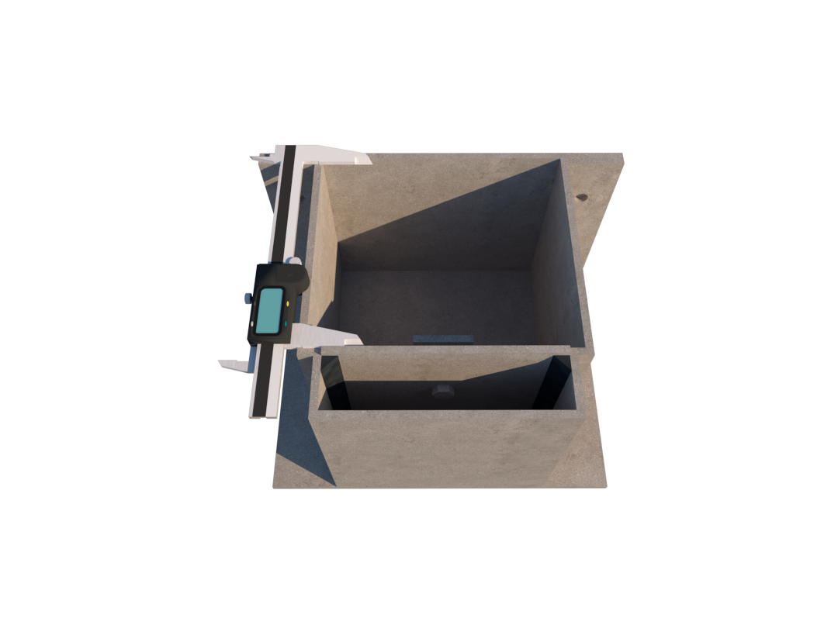
Prototype/Prototype 2018/Bird Eye 3.png
