fariszuh/IoT-Concrete-Heat-Hidration/Prototype/Prototype 2018/Detail Alat Pengukuran.png

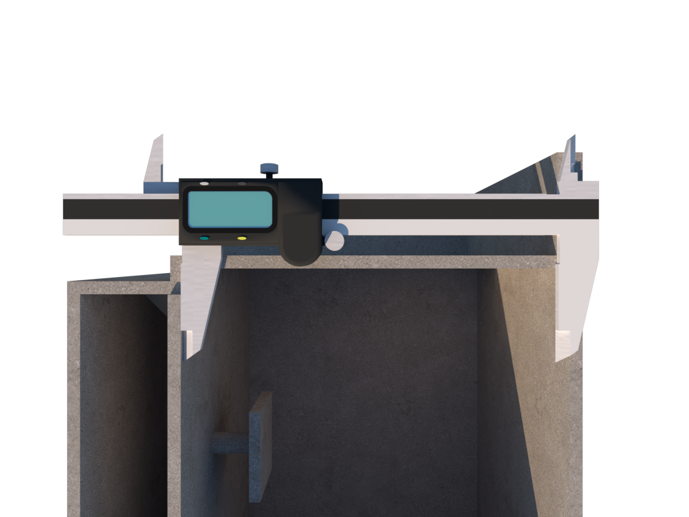
Prototype/Prototype 2018/Detail Alat Pengukuran.png
