fariszuh/IoT-Concrete-Heat-Hidration/Prototype/Prototype 2018/Tampak Atas.png

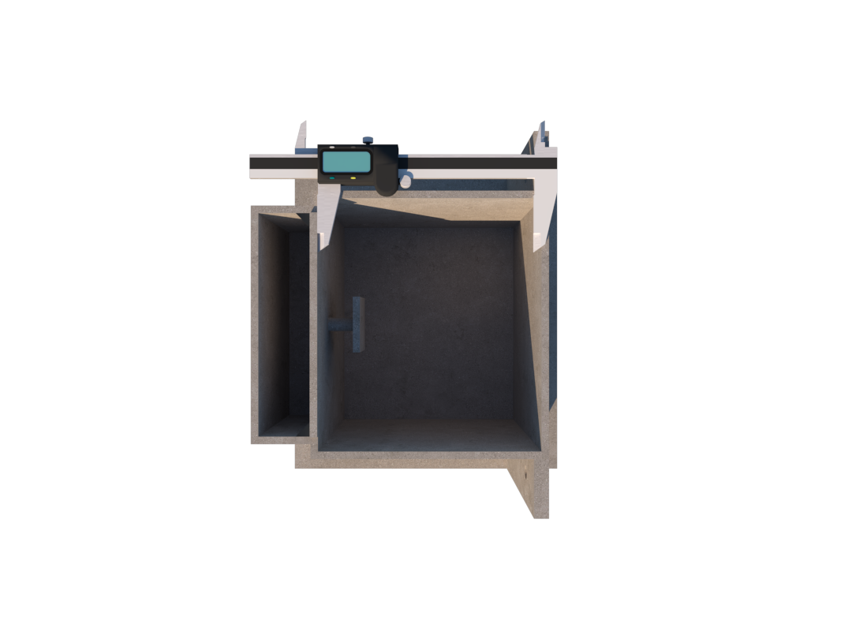
Prototype/Prototype 2018/Tampak Atas.png
