fariszuh/IoT-Concrete-Heat-Hidration/Prototype/Prototype 2018/Tampak Samping 1.png

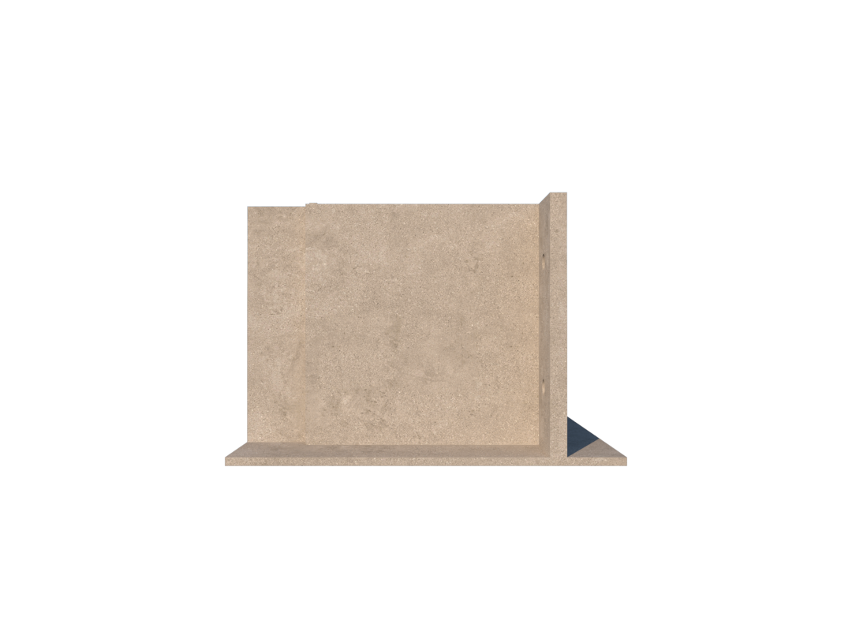
Prototype/Prototype 2018/Tampak Samping 1.png
