fariszuh/IoT-Concrete-Heat-Hidration/Prototype/Prototype 2018/Tampak Samping 2.png

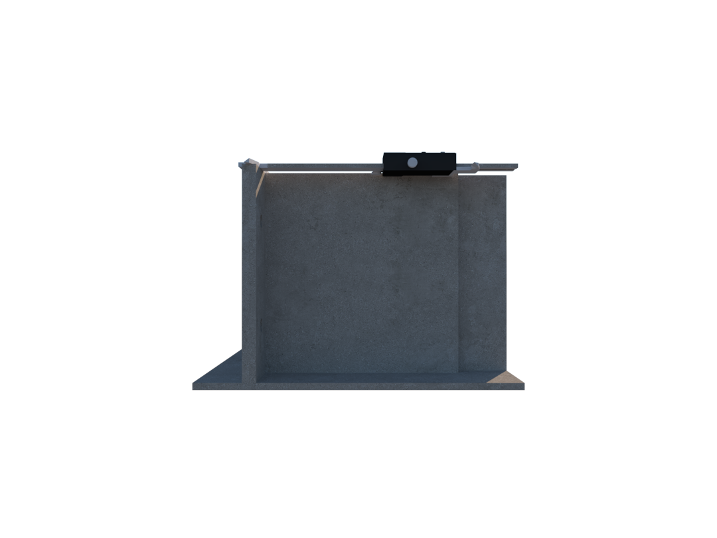
Prototype/Prototype 2018/Tampak Samping 2.png
