fariszuh/IoT-Concrete-Heat-Hidration/Prototype/Prototype 2018/Tampak Samping 4.png

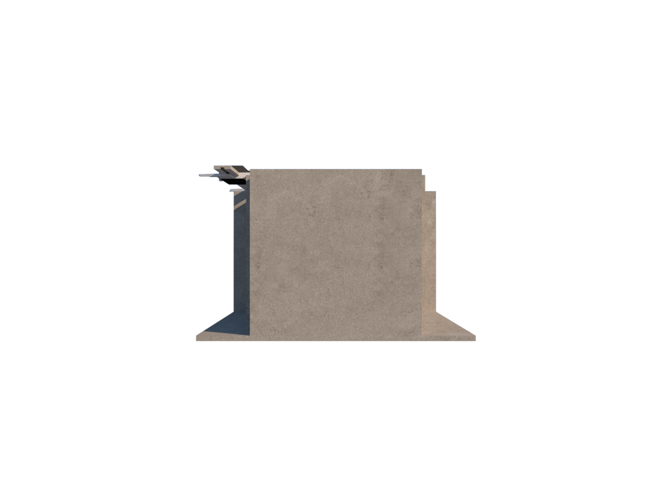
Prototype/Prototype 2018/Tampak Samping 4.png
