fariszuh/IoT-Concrete-Heat-Hidration/Proposal PKM KC/Biodata/Biodata Faris PKM KC print.pdf

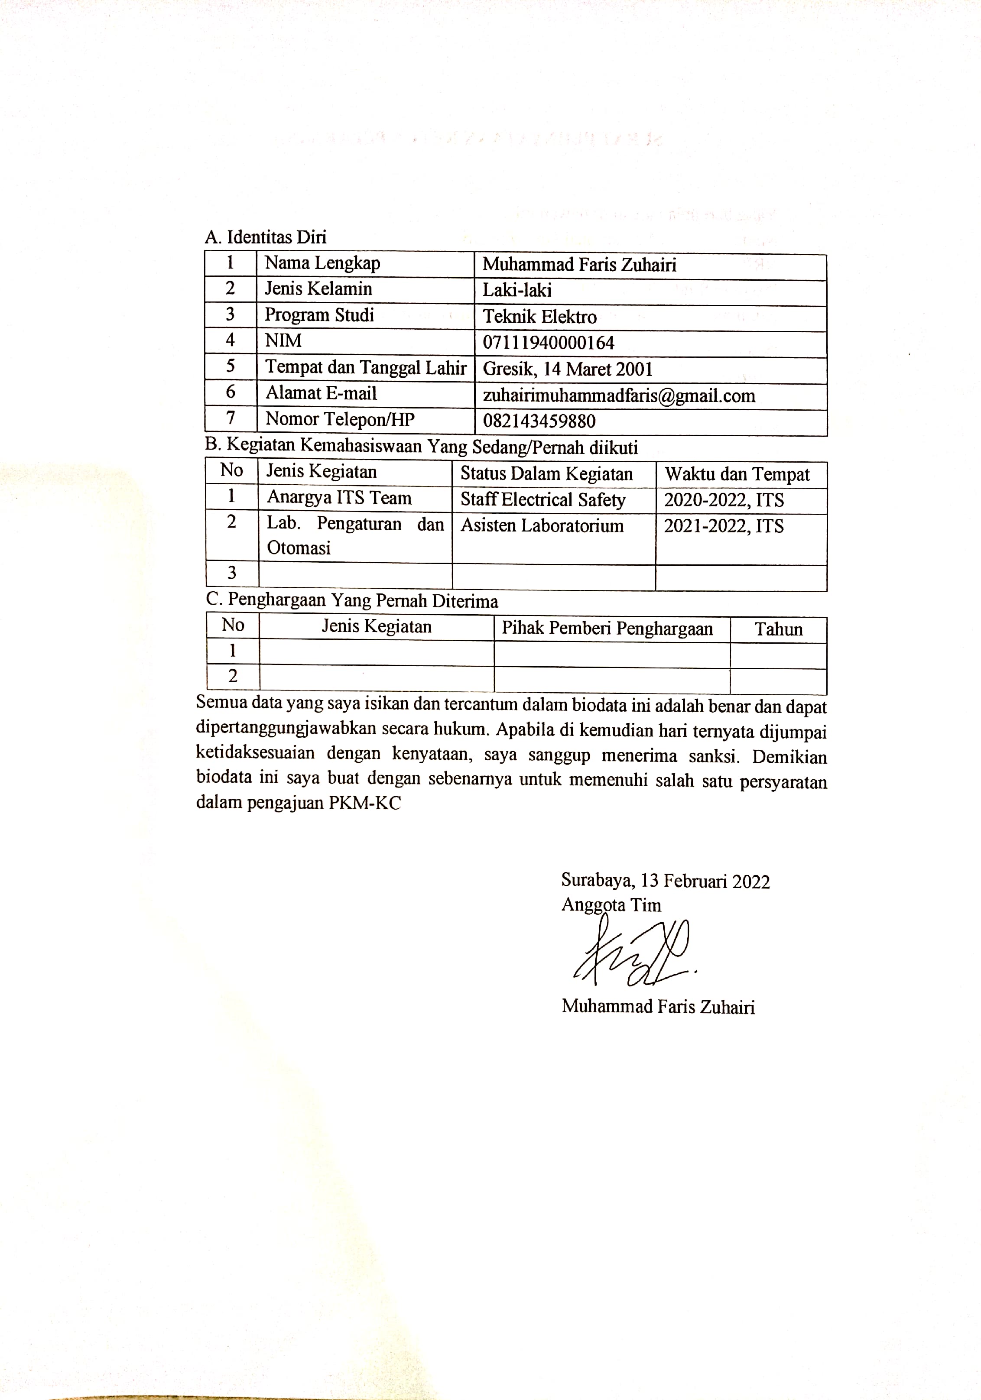
[picture p432: page 1]
