fariszuh/IoT-Concrete-Heat-Hidration/Prototype/Jumper LCD/HelloWorld/HelloWorld.ino

// ESP8266 or ARDUINO with 16x2 i2c LCD
// Compatible with the Arduino IDE 1.8.3
// Library https://github.com/lucasmaziero/LiquidCrystal_I2C
// Original Library https://github.com/fdebrabander/Arduino-LiquidCrystal-I2C-library
// Standard for ESP8266 with 4-SDA 5-SCL or ARDUINO with A4-SDA A5-SCL and LCD 16x2 display
// and access from ESP8266: lcd.begin(sda,scl) or ARDUINO: lcd.begin()

#include <LiquidCrystal_I2C.h>

// Set the LCD address to 0x27 for a 16 chars and 2 line display
LiquidCrystal_I2C lcd(0x27, 16, 2);

void setup()
{
  // initialize the LCD
  lcd.begin(); //Init with pin default ESP8266 or ARDUINO
  //lcd.begin(0, 2); //ESP8266-01 I2C with pin 0-SDA 2-SCL

  // Turn on the blacklight and print a message.
  lcd.backlight();
  
  lcd.setCursor(0, 0);
#if defined(ESP8266)
  lcd.print("PKM KC");
#else
  lcd.print("Beton ITS");
#endif
  lcd.setCursor(0, 1);
  lcd.print("S=22mm | T=39C");
}

void loop()
{
  // Do nothing here...
}
