fariszuh/IoT-Concrete-Heat-Hidration/Prototype/Source Code/WriteMicroSD/WriteMicroSD.ino

#include <SPI.h>
#include <SD.h>

File myFile;

// change this to match your SD shield or module;
const int chipSelect = 4;

void setup()
{
  // Open serial communications and wait for port to open:
  Serial.begin(9600);
  pinMode(chipSelect, OUTPUT);
  while (!Serial) {
    ; // wait for serial port to connect. Needed for Leonardo only
  }


  Serial.print("Initializing SD card...");

  SD.begin();
  if (SD.begin(4))
  {
    Serial.println("SD card is ready to use.");
  } else
  {
    Serial.println("SD card initialization failed");
    return;
  }

  // open the file. note that only one file can be open at a time,
  // so you have to close this one before opening another.
  
  myFile = SD.open("test.txt", FILE_WRITE);
  //printFiles(myFile,0);
  // if the file opened okay, write to it:
  if (myFile) {
    Serial.print("Writing to test.txt...");
    myFile.println("testing 1, 2, 3.");
    // close the file:
    myFile.close();
    Serial.println("done.");
  } else {
    // if the file didn't open, print an error:
    Serial.println("error opening test.txt");
  }

  // re-open the file for reading:
  myFile = SD.open("test.txt");
  if (myFile) {
    Serial.println("test.txt:");

    // read from the file until there's nothing else in it:
    while (myFile.available()) {
      Serial.write(myFile.read());
    }
    // close the file:
    myFile.close();
  } else {
    // if the file didn't open, print an error:
    Serial.println("error opening test.txt");
  }
}

void loop()
{
  // nothing happens after setup
}

void printFiles(File dir, int numTabs)
{
  while (true)
  {
    File entry =  dir.openNextFile();
    if (! entry)
    {
      break;
    }
    for (uint8_t i = 0; i < numTabs; i++)
    {
      Serial.print('\t');
    }
    Serial.println(entry.name());
    entry.close();
  }
}
