fariszuh/IoT-Concrete-Heat-Hidration/Prototype/Source Code/MAIN_CODE/WIFI.ino

String send(String url) {
  if (!client.connect(host, httpPort)) {
    return "Error Request Confirm";
  }
  client.print(String("GET ") + url + " HTTP/1.1\r\n" +
               "Host: " + host + "\r\n" +
               "User-Agent: BuildFailureDetectorESP8266\r\n" +
               "Connection: close\r\n\r\n");
}
