fariszuh/IoT-Concrete-Heat-Hidration/Luaran PKM (Video dan Foto)/Album foto/20220903_185714.jpg

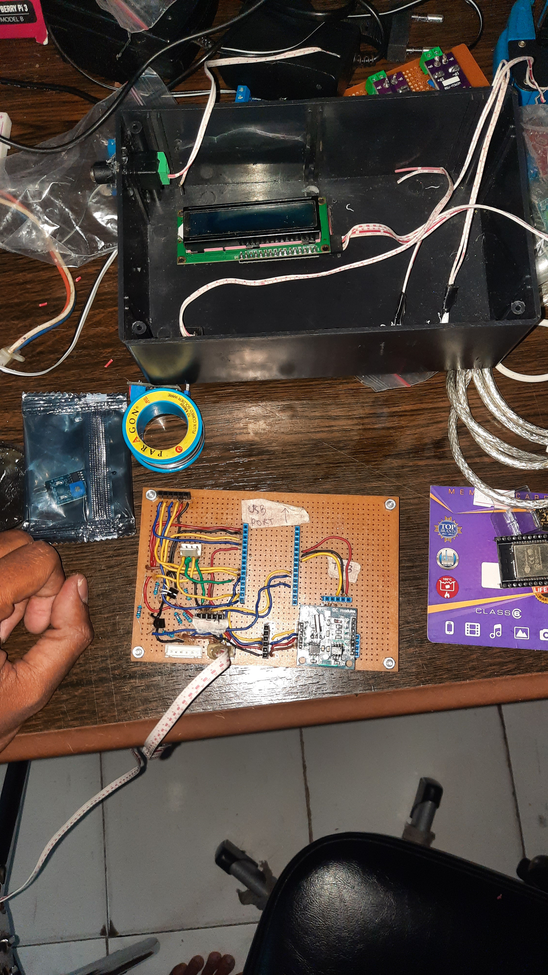
Luaran PKM (Video dan Foto)/Album foto/20220903_185714.jpg
